Nadya-85/Grupo-3--FUNBIO/Documentación/Taller/Taller 10 - Actividad 3.pdf

Parámetro | Valor Bajo | Valor Medio | Valor Alto | Efecto principal
Altura de capa | 0.1mm | 0.15mm | 0.2mm | La calidad superficial y tiempo de impresión
Densidad de relleno | 10% | 20% | 50% | Densidad mecánica de la pieza y consumo de material
Velocidad de impresión | 30 mm/s | 50 mm/s | 70 mm/s | Tiempo total de impresión y precisión/adhesi ón
Top/Bottom Thickness | 0.6 mm | 0.9 mm | 1.5 mm | Dirección de la resistencia mecánica
Walls thickness | 0.8 mm | 1.2 mm | 1.7 mm | Resistencia estructural externa y acabado estético
Cooling | 40% | 90% | 100% | En PLA, más ventilación mejora los detalles y evita deformaciones.
Temperatura de impresión | 190 °C | 200 °C | 220 °C | Temperatura de la boquilla de impresión.
Peso | 15g | 18g | 20g
Tiempo | 5 h 33 min | 3 h 0 min | 1 h 52 min
