Nadya-85/Grupo-3--FUNBIO/Documentación/Entregables/Entrgable N°9/Entregable N°9.pdf

GUIA DE ENTREGABLE N°9

CASO 3:
Lesión medular por proyectil / paraplejia

INTEGRANTES:
Quezada Ponciano, Nadya Lyz Peñaloza Díaz, Matias Alejandro Silva Avileno, Fabiana Valery Palacin Hilario, Jeanpierre Ramirez Rodriguez, Alexandra Fajardo Peña, Edwin José Guillermo

ÍNDICE:
a) Hardware electrónico
b) Software
c) Fabricación digital
d) Plan de usabilidad basado en evidencias

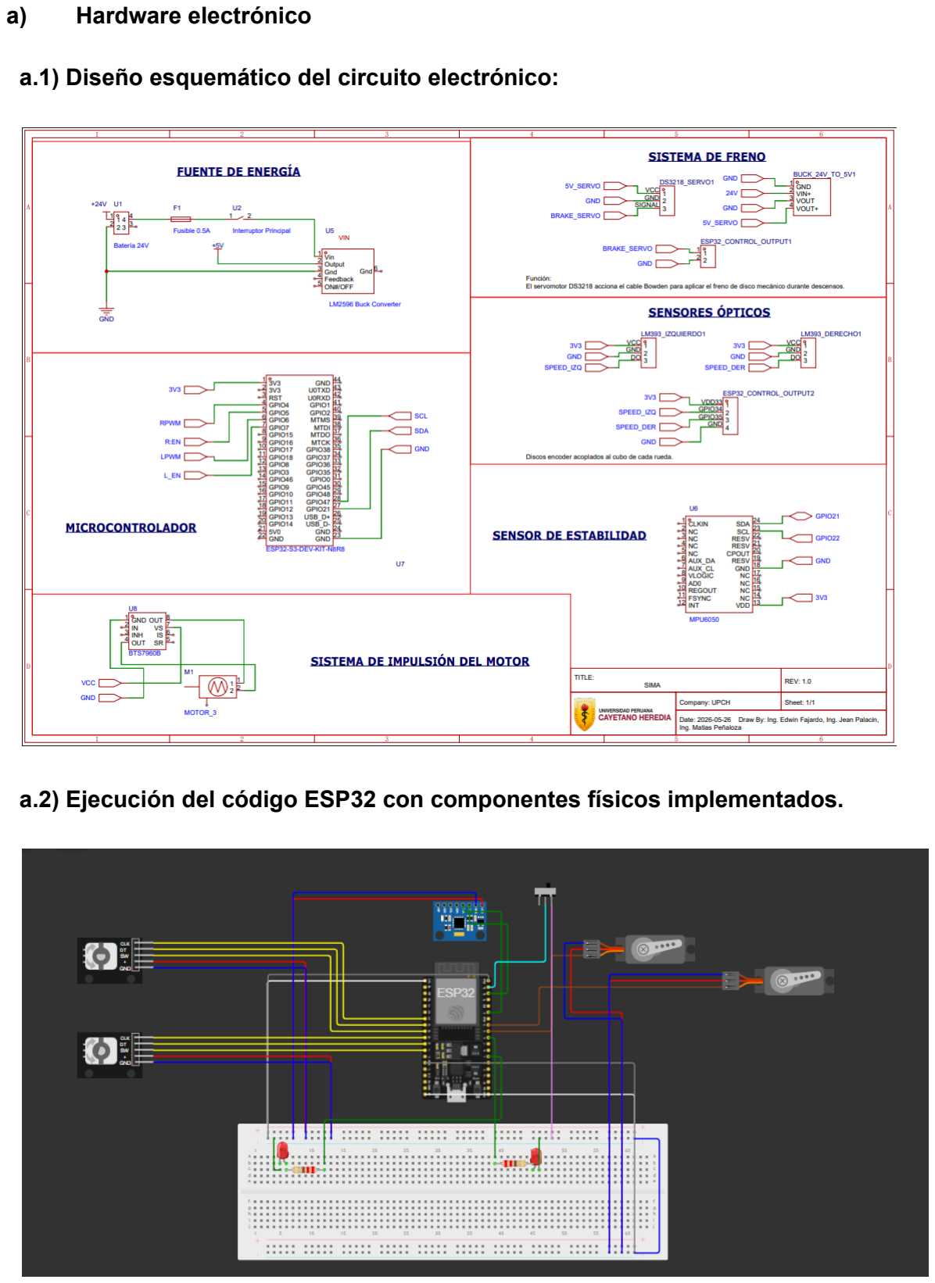
[picture p50: page 2]

a) Hardware electrónico

a.1) Diseño esquemático del circuito electrónico:

a.2) Ejecución del código ESP32 con componentes físicos implementados.

a.3) Avance de su prototipado electrónico.

Funcionamiento en casos:

- Caso 1: SISTEMA APAGADO

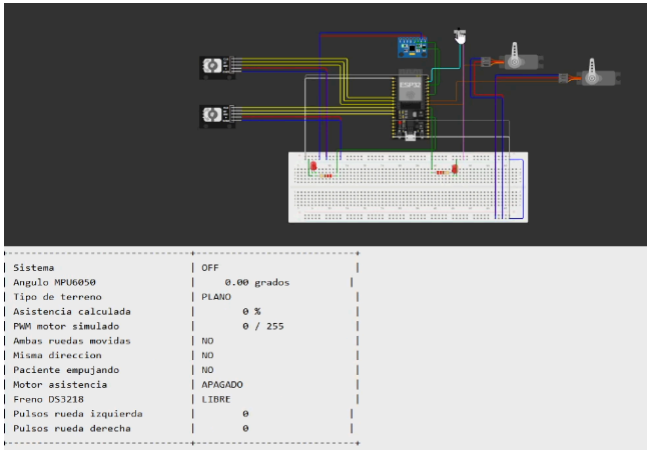
[picture p51: figure]

- Caso 2: MPU6050 detecta subida y el porcentaje de asistencia.

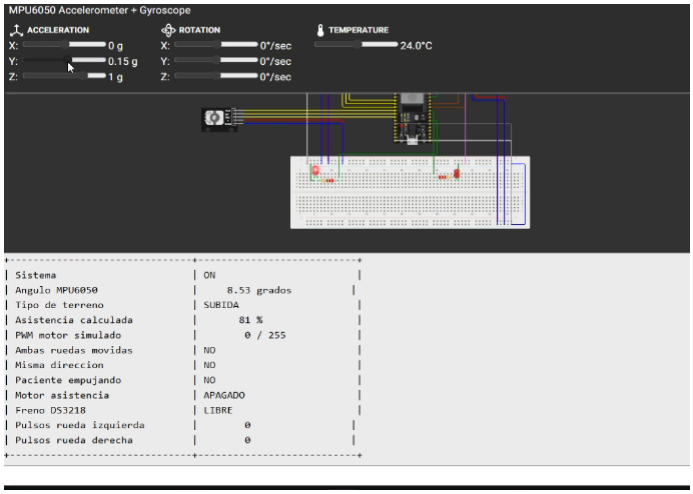
[picture p52: figure]

- Caso 3: MPU6050 detecta bajada e inhabilita la asistencia y activa los frenos intermitentemente.

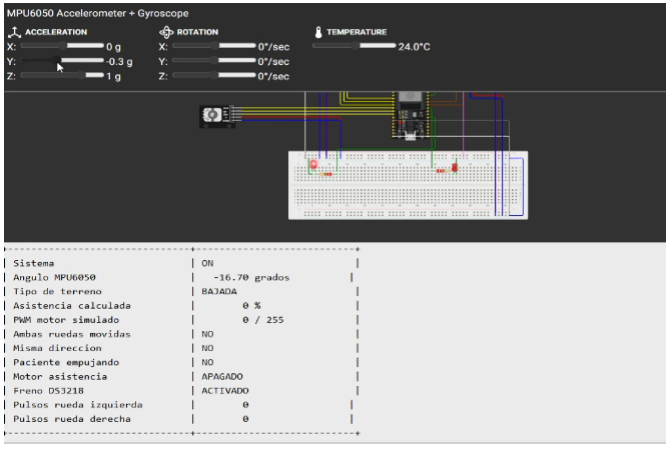
[picture p53: figure]

- Caso 4: Los sensores detectan el empuje y simultaneidad del movimiento de las ruedas y activa asistencia.

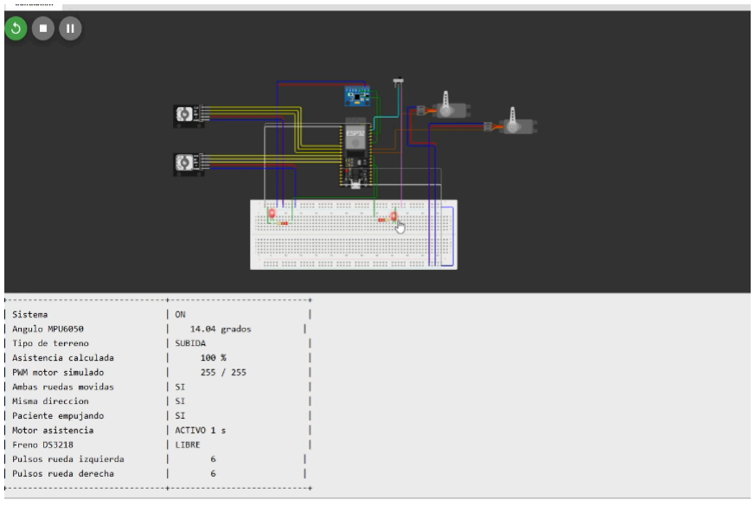
[picture p54: figure]

- Caso 5: Sensores detectan empuje y simultaneidad pero no activan la asistencia y bloquean el freno intermitentemente por bajada.

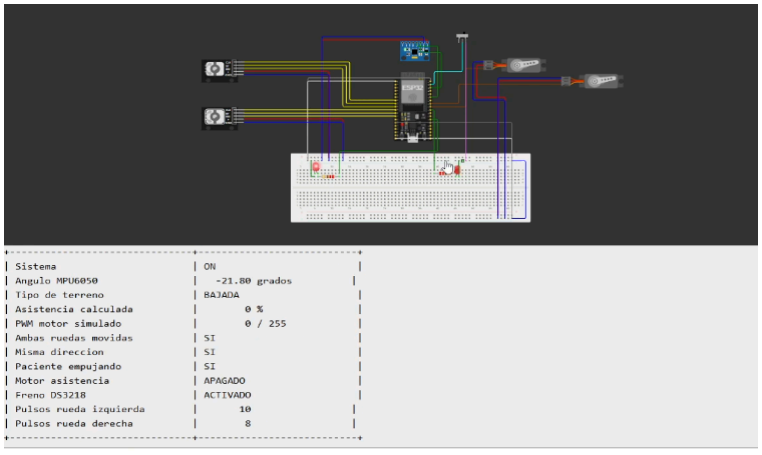
[picture p55: figure]

b) Software

b.1) Script de programación para el microcontrolador

Software.ino (https://drive.google.com/open?id=1QNNkiSALg92ZPX-Y5VDY9vaBm5gV7uGd)

c) Fabricación digital
c.1) Modelado digital del prototipo completo

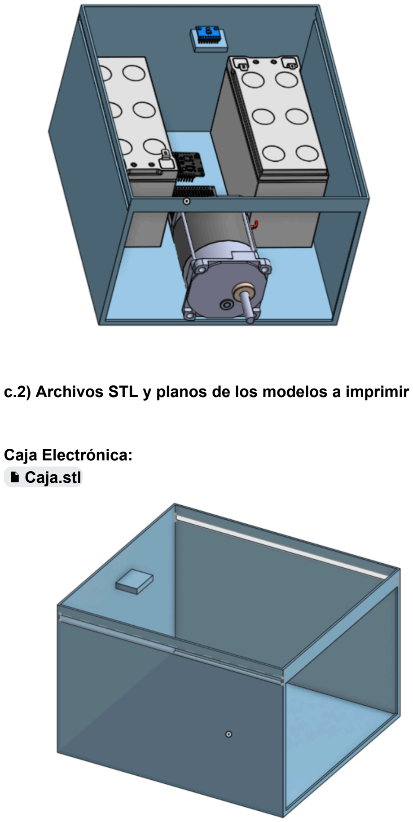
[picture p56: page 8]

c.2) Archivos STL y planos de los modelos a imprimir

Caja Electrónica:
Caja.stl (https://drive.google.com/open?id=1Idi60X_xnom6asZyzeSryu2H1RnrhICt)

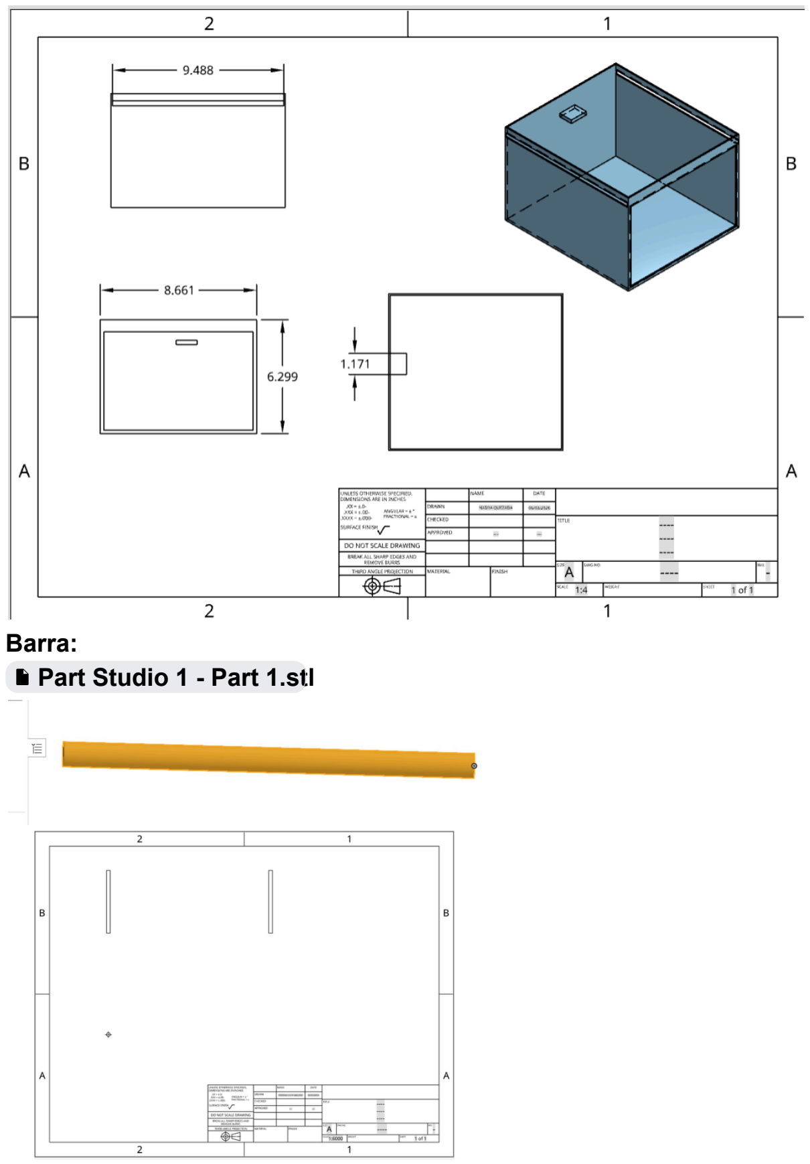
[picture p57: page 9]

Barra:
Part Studio 1 - Part 1.stl (https://drive.google.com/open?id=1k5roUTsqK_4T5D3ctGGkcU61z_Ii1c35)

Engranaje:
https://cad.onshape.com/documents/0c8cfb7354d4f6df7f082058/w/bfc970ec4490c92dce513070/e/b32831fdd1642657cbf62373 (https://cad.onshape.com/documents/0c8cfb7354d4f6df7f082058/w/bfc970ec4490c92dce513070/e/b32831fdd1642657cbf62373)

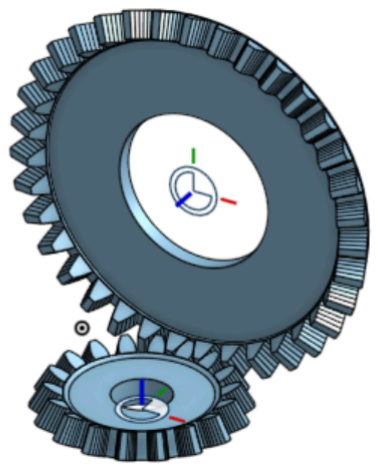
[picture p58: figure]
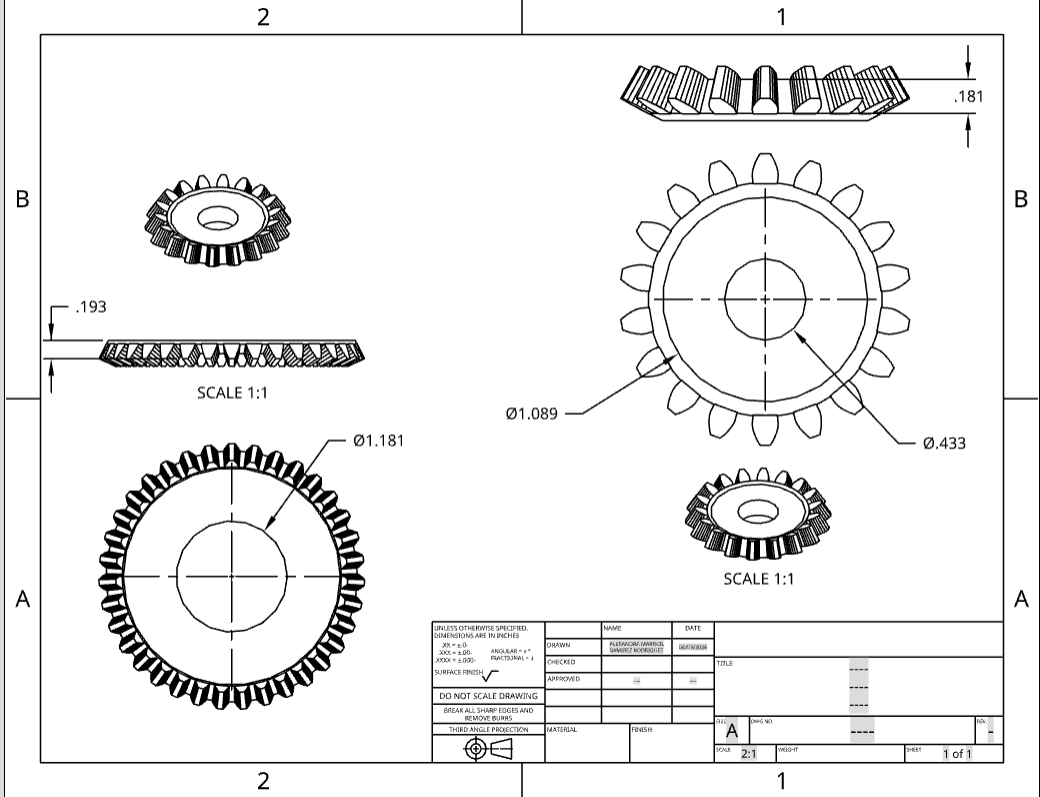
[picture p59: figure]

Archivos STL
https://github.com/Nadya-85/Grupo-3--FUNBIO/blob/5a6e28614ed48188a40b07a3fd94a64e7c92d70e/Documentaci%C3%B3n/Entregables/Entrgable%20N%C2%B09/Modelado%203D/engranaje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 (https://github.com/Nadya-85/Grupo-3--FUNBIO/blob/5a6e28614ed48188a40b07a3fd94a64e7c92d70e/Documentaci%C3%B3n/Entregables/Entrgable%20N%C2%B09/Modelado%203D/en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) https://github.com/Nadya-85/Grupo-3--FUNBIO/blob/5a6e28614ed48188a40b07a3fd94a64e7c92d70e/Documentaci%C3%B3n/Entregables/Entrgable%20N%C2%B09/Modelado%203D/engranaje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

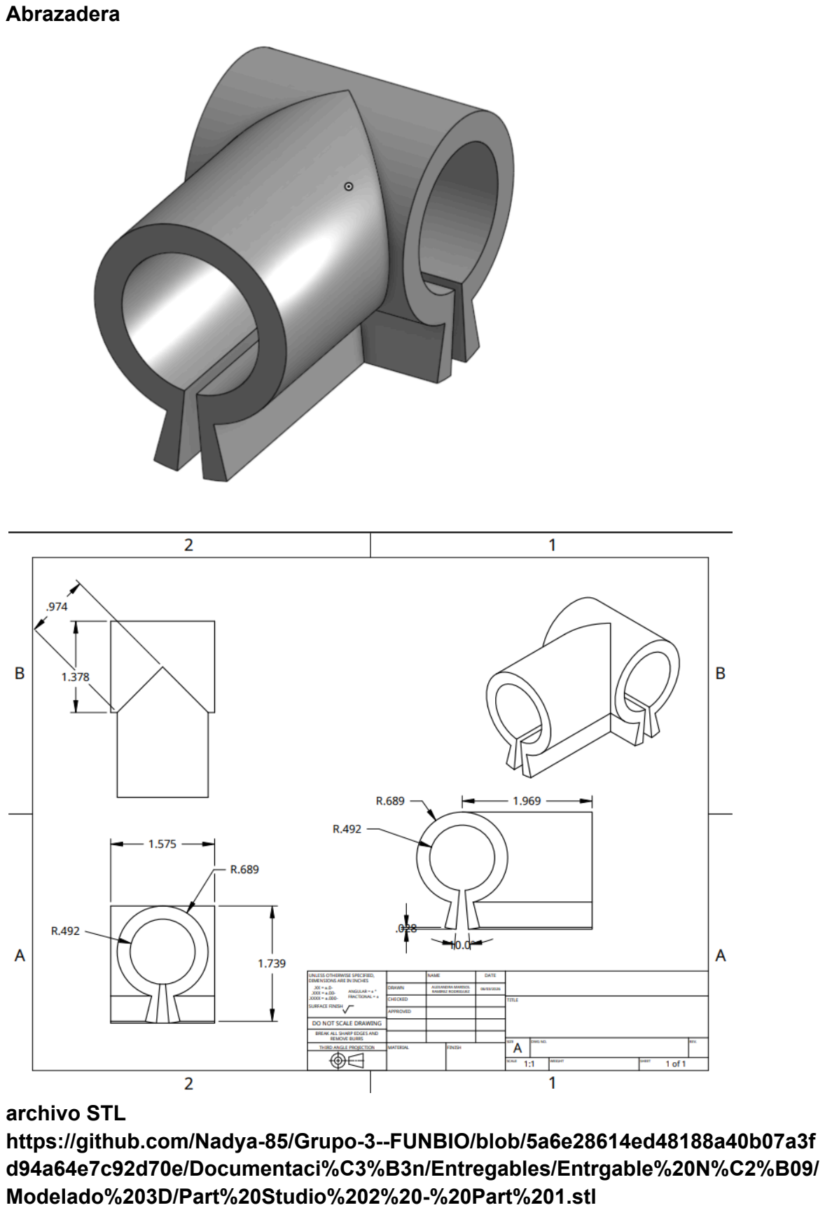
[picture p60: page 11]

Abrazadera

archivo STL
https://github.com/Nadya-85/Grupo-3--FUNBIO/blob/5a6e28614ed48188a40b07a3fd94a64e7c92d70e/Documentaci%C3%B3n/Entregables/Entrgable%20N%C2%B09/Modelado%203D/Part%20St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 d) Plan de usabilidad basado en evidencias
Sección de plan | ¿Qué es? | ¿Qué hacer ? | ¿Qué evidencias deben incluir ?
Contexto de uso | Sistema de asistencia y frenado inteligente para usuarios de silla de ruedas manual en entornos urbanos. | Identificar usuario, lugares de uso (rampas, veredas, hospitales) y frecuencia de uso. | Modelo 3D o boceto mostrando el Kit Urbano C7 instalado en la silla.
Perfil de usuario | Usuario de silla de ruedas con limitaciones motoras que afectan su movilidad e independencia. | Identificar limitaciones físicas relacionadas con movilidad y esfuerzo durante el desplazamiento. | Varón de 48 años destacando lesión medular, uso de silla de ruedas y dificultades de movilidad que justifican la implementación del Kit Urbano C7.
Analisis de tareas | Análisis de las acciones necesarias para instalar el Kit Urbano C7, activar la asistencia motorizada, desplazarse en pendientes y controlar la velocidad mediante el sistema de frenado. | Listar tareas como: instalar el kit, encender el sistema, desplazarse en terreno plano, subir pendientes con asistencia motorizada, bajar pendientes con frenado asistido y detener la silla. Identificar cuáles son críticas para la seguridad del usuario. | Tabla de tareas críticas, riesgos y consecuencias asociadas que se asocie a sus AVD (La tabla se mostrará en la siguiente figura) .
Criterios de exito | Definir valores aceptables para cada función del sistema, por ejemplo: precisión en la detección de pendientes, tiempo de respuesta, activación del frenado y nivel de seguridad durante el recorrido. | Definir objetivos de eficacia (activación correcta del sistema), eficiencia (tiempo de respuesta), satisfacción (comodidad y confianza del usuario) y seguridad (ausencia de incidentes). | Tabla con métricas cuantificables y resultados esperados. (La tabla se mostrará en la siguiente figura) .

Tabla de tareas críticas :

Tarea | Posible error | Riesgo | Criticidad
Instalar el kit | Mala fijación | Desprendimiento | Alta
Encender sistema | No verificar batería | Sistema inoperativo | Media
Subir pendiente | Asistencia insuficiente | Fatiga del usuario | Alta
Bajar pendiente | Fallo del frenado | Pérdida de control | Muy Alta

Tabla de métricas cuantificables y resultados esperados:

Indicador | Metodo de evaluacion | Valor objetivo
Detección de pendientes | Comparación con inclinación real | ≥ 95%
Activación de asistencia | Pruebas funcionales | ≥ 95%
Activación de frenado | Pruebas funcionales | ≥ 95%
Tiempo de respuesta | Cronómetro/registro del sistema | < 1 s
Satisfacción del usuario | Encuesta SUS | ≥ 80 puntos
Seguridad | Número de incidentes durante las pruebas | 0
