Nadya-85/Grupo-3--FUNBIO/Documentación/Entregables/Entregable N°8/Entregable N°8.pdf

GUIA DE ENTREGABLE N°8

CASO 3:
Lesión medular por proyectil / paraplejia

INTEGRANTES:
Quezada Ponciano, Nadya Lyz Peñaloza Díaz, Matias Alejandro Silva Avileno, Fabiana Valery Palacin Hilario, Jeanpierre Ramirez Rodriguez, Alexandra Fajardo Peña, Edwin José Guillermo

ÍNDICE
1. Importados
2. Modelados

Modelado 3D de los componentes

### 1. Importados

a) ESP32

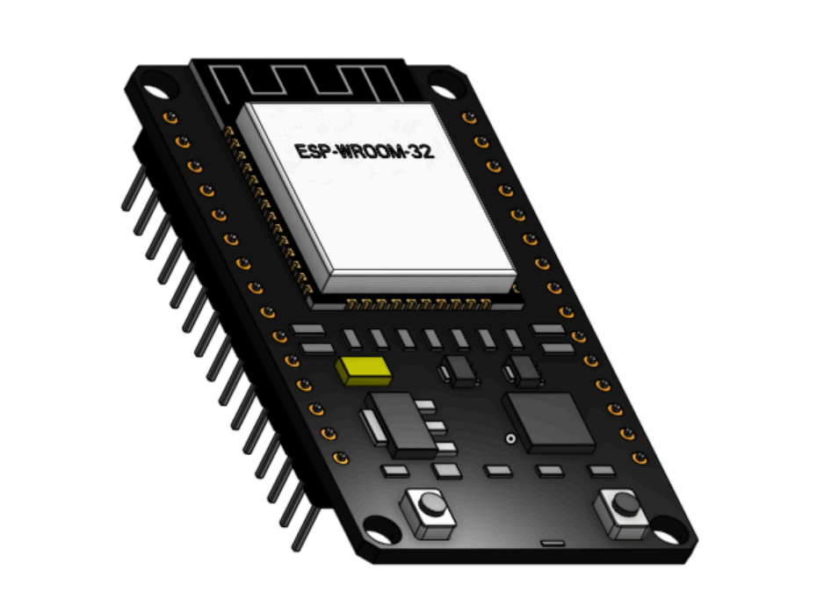
[picture p61: figure]

https://cad.onshape.com/documents/fe2fc5c113415b535518b715/w/49ef476d0d1d86e92a8f14a1/e/2e020fae72789caa4f564eb7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 23676df5edec03a35 (https://cad.onshape.com/documents/fe2fc5c113415b535518b715/w/49ef476d0d1d86e92a8f14a1/e/2e020fae72789caa4f564eb7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)

b) Motor DC 24V

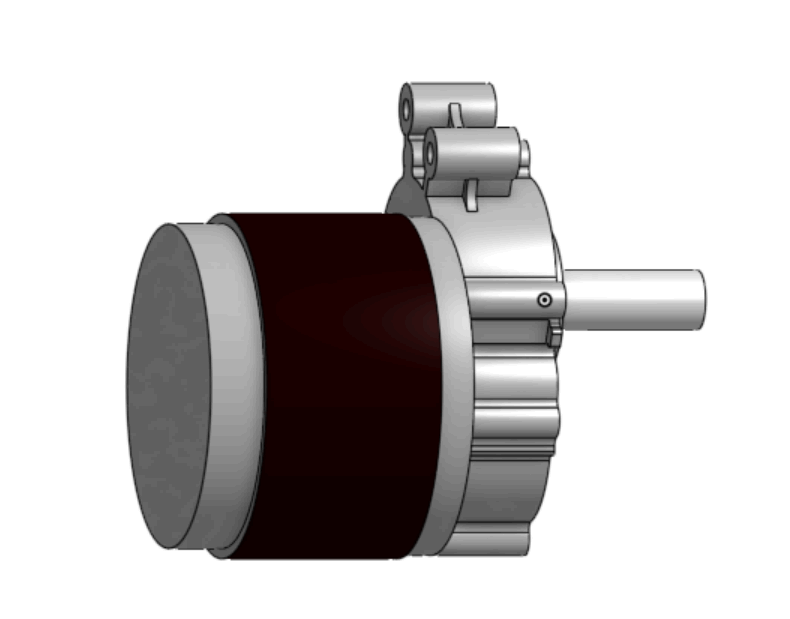
[picture p62: figure]

https://cad.onshape.com/documents/29574c1c496ad6fbb76fa65f/w/c6939c078cb6e51be4b720a7/e/403110079cfe1cae44fe99f7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 e4df02ca1f19e2636 (https://cad.onshape.com/documents/29574c1c496ad6fbb76fa65f/w/c6939c078cb6e51be4b720a7/e/403110079cfe1cae44fe99f7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)

c) Driver de motor (BTS7960 43A)

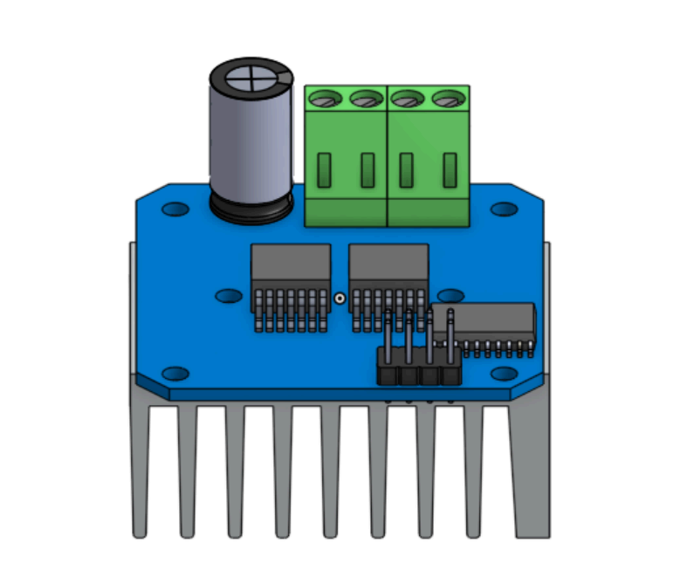
[picture p63: figure]

https://cad.onshape.com/documents/722dbbecc4ac26e69685e04b/w/de750ad9b3bf6ea111d73016/e/7e61f720ef6a980854f621ba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 9e605cd60c42166c (https://cad.onshape.com/documents/722dbbecc4ac26e69685e04b/w/de750ad9b3bf6ea111d73016/e/7e61f720ef6a980854f621ba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)

d) Regulador LM2596

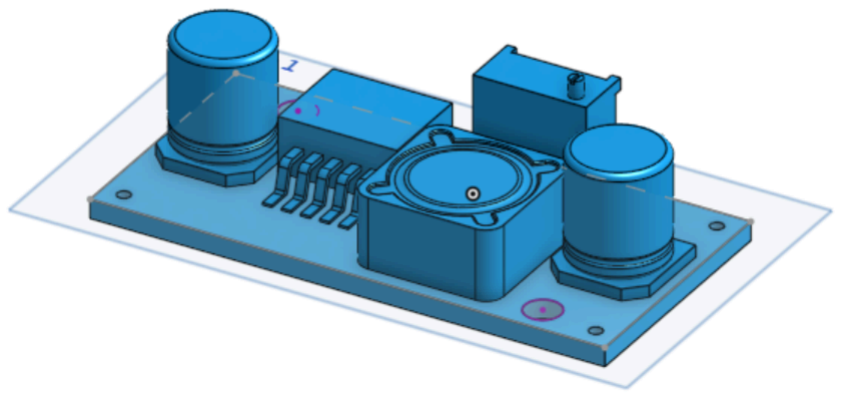
[picture p64: figure]

https://cad.onshape.com/documents/b7b84f8724b1efabd3e8bedd/w/a21f4455c5390d7d0d2bf8c8/e/14543a8e8df9499e86e28706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 45721502616d5c2a6 (https://cad.onshape.com/documents/b7b84f8724b1efabd3e8bedd/w/a21f4455c5390d7d0d2bf8c8/e/14543a8e8df9499e86e28706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)

e) Switch ON/OFF

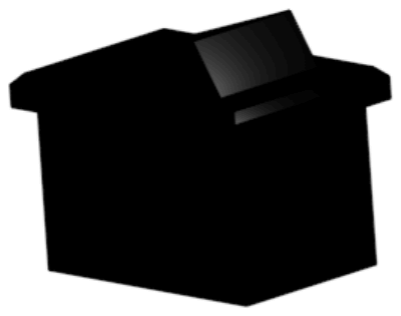
[picture p65: figure]

https://cad.onshape.com/documents/ade0a61845ae4fb3431f720c/w/565239054fb8be03dde38aee/e/1b88e0a8e63dd7065da3dd35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 3f5721502616d5c101 (https://cad.onshape.com/documents/ade0a61845ae4fb3431f720c/w/565239054fb8be03dde38aee/e/1b88e0a8e63dd7065da3dd35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)

f) LM393

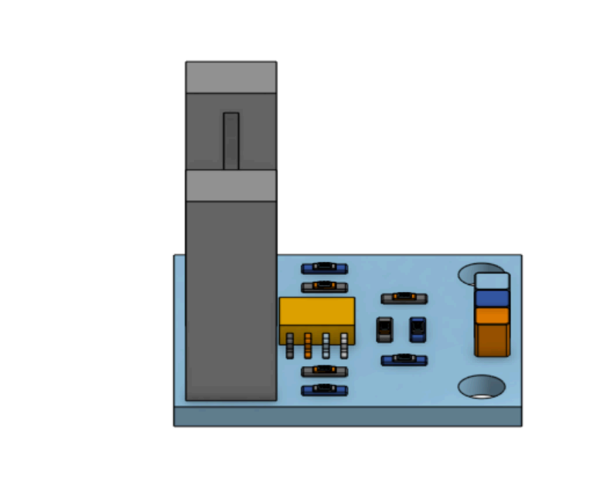
[picture p66: figure]

https://cad.onshape.com/documents/a74c2326ba62b3aa8945d9c9/w/44dd0150f07406c4244389be/e/a022ccecb725c4a6901df66b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 7b468401201dcc69f (https://cad.onshape.com/documents/a74c2326ba62b3aa8945d9c9/w/44dd0150f07406c4244389be/e/a022ccecb725c4a6901df66b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)

g) MPU 6050

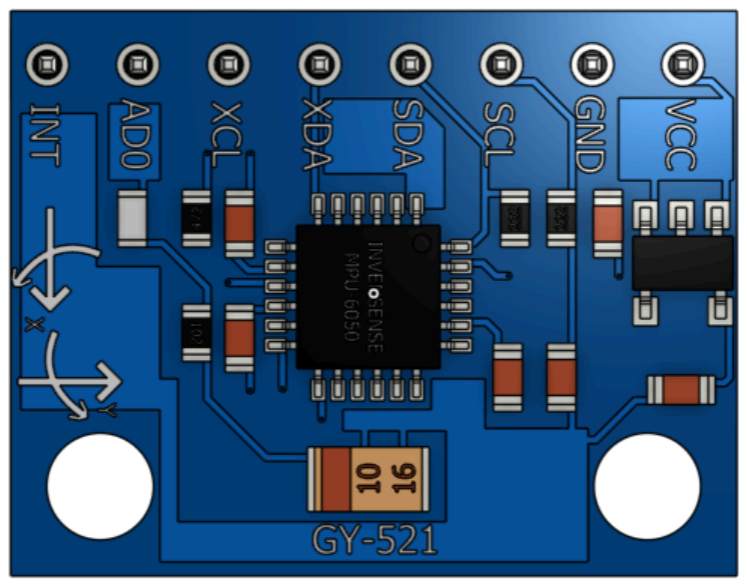
[picture p67: figure]

https://cad.onshape.com/documents/0f27ed9f233e3be8bb802911/w/502657e910908bda854d1360/e/78c170c33b39e40b5ba9a4cb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 c3bcc75bd5e84913b4 (https://cad.onshape.com/documents/0f27ed9f233e3be8bb802911/w/502657e910908bda854d1360/e/78c170c33b39e40b5ba9a4cb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)

h) Servo DS3218

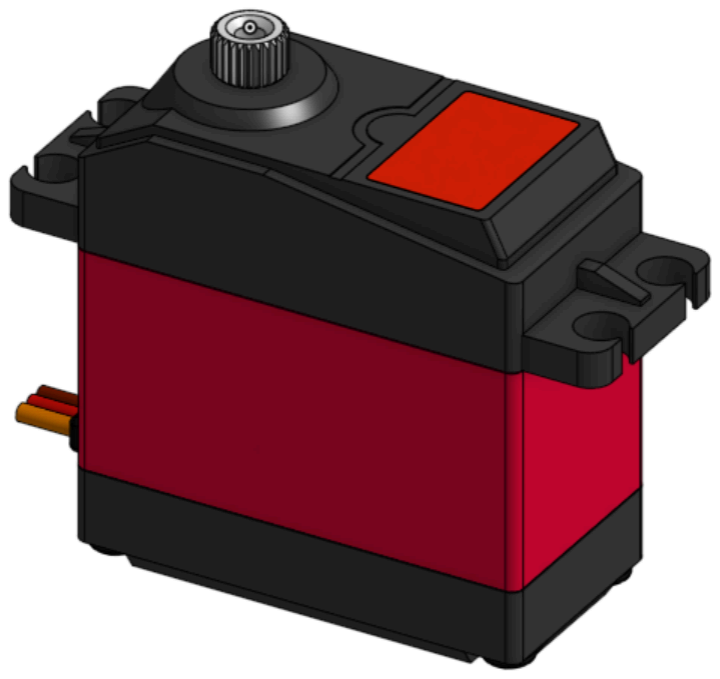
[picture p68: figure]

https://cad.onshape.com/documents/d5c7789b7a614957c1189cbd/w/ce6124b3abbf0c9b08c676d4/e/8ea79ae3aaf09e6f7db1e214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 0f739b181326bd891 (https://cad.onshape.com/documents/d5c7789b7a614957c1189cbd/w/ce6124b3abbf0c9b08c676d4/e/8ea79ae3aaf09e6f7db1e214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)
i) Buck 5V

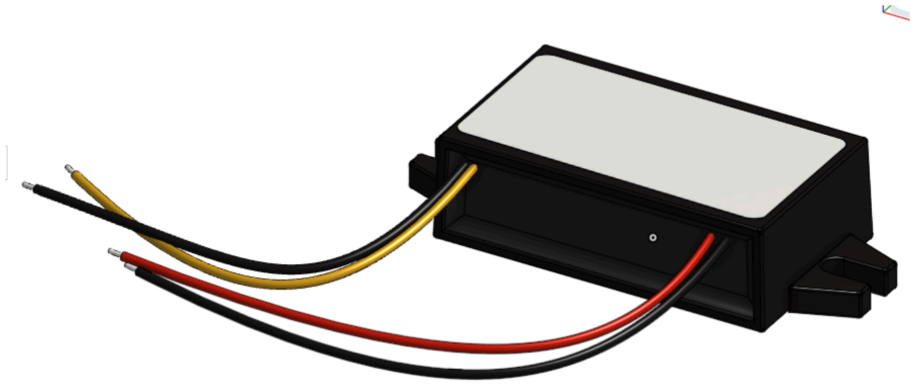
[picture p69: figure]

https://cad.onshape.com/documents/6bf642ec03a6724235cac885/w/3cc0e38e2b2c3b097d9072ba/e/ca223f1ae1df0242dc7e0e98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 73db0dc0b4097176f (https://cad.onshape.com/documents/6bf642ec03a6724235cac885/w/3cc0e38e2b2c3b097d9072ba/e/ca223f1ae1df0242dc7e0e98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)

### 2. Modelados (colocar la imagen y el link del componente)

a) Caja para la electrónica - Versión 1

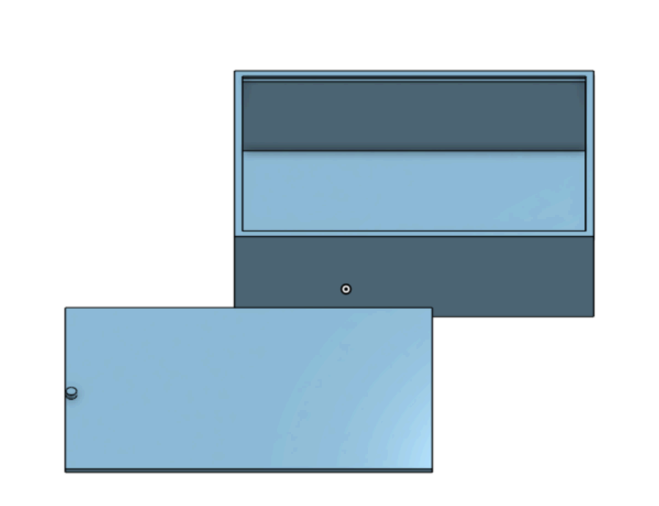
[picture p70: figure]

https://cad.onshape.com/documents/ded1ce054706ec6fbc7535f1/w/0c0e8277efb87ba04d14f22f/e/1e055f56dfcda0f58cce56e2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 57 (https://cad.onshape.com/documents/ded1ce054706ec6fbc7535f1/w/0c0e8277efb87ba04d14f22f/e/1e055f56dfcda0f58cce56e2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)
