Nadya-85/Grupo-3--FUNBIO/Documentación/Entregables/Presentaciones/PPT Entregable N°8.pdf

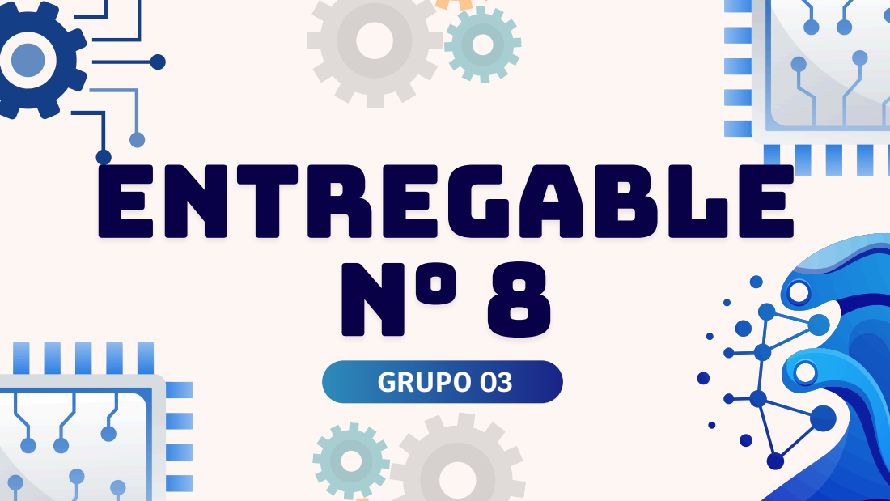
[picture p71: page 1]
GRUPO 03; ENTREGABLE N° 8

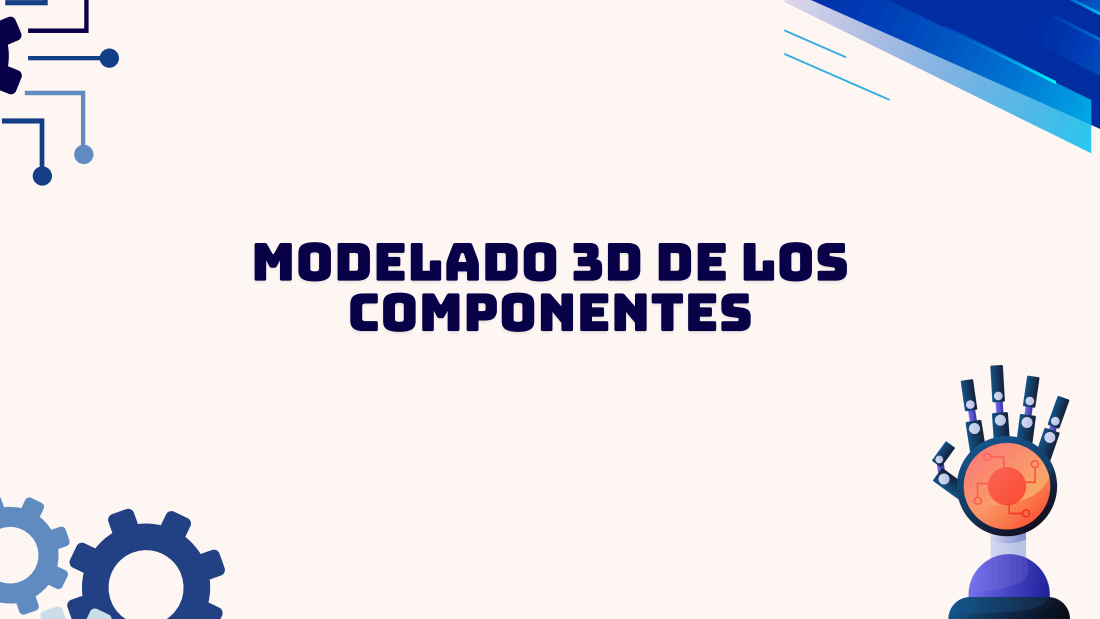
[picture p72: page 2]

Modelado 3D de los
componentes

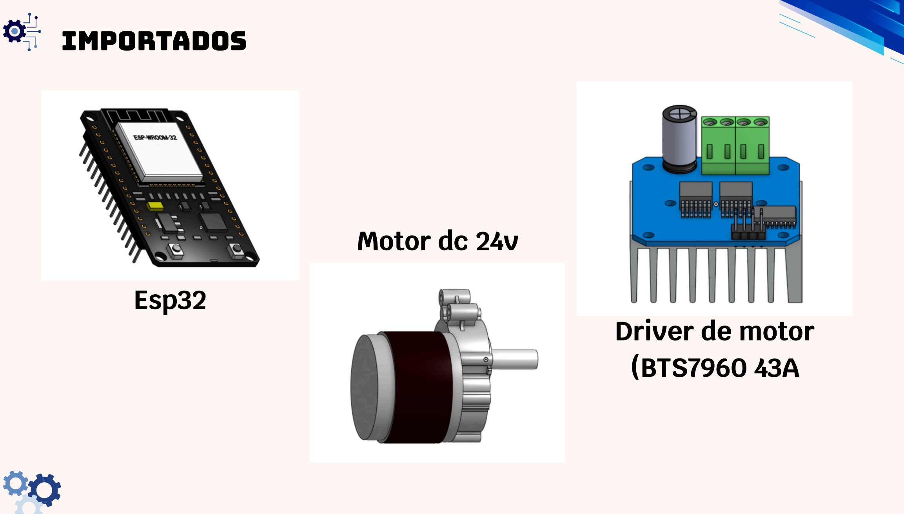
[picture p73: page 3]

Importados

Esp32

Motor dc 24v

Driver de motor
(BTS7960 43A

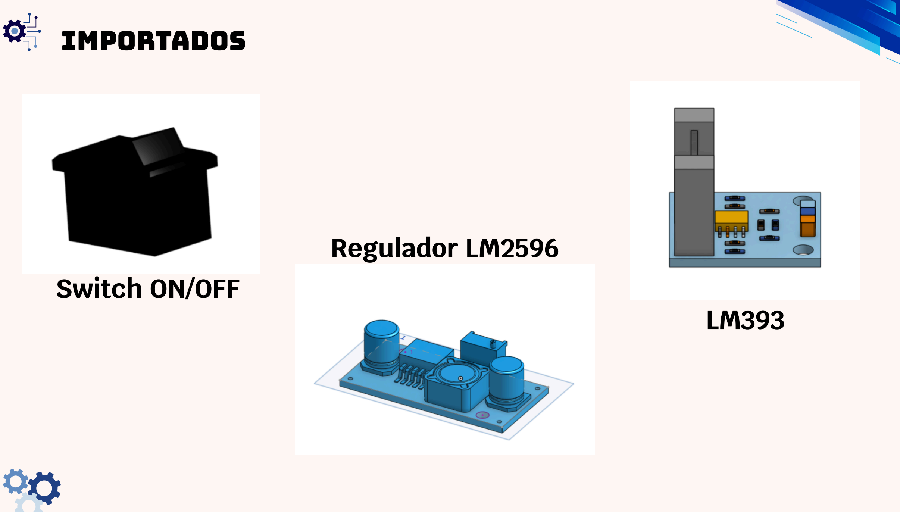
[picture p74: page 4]

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
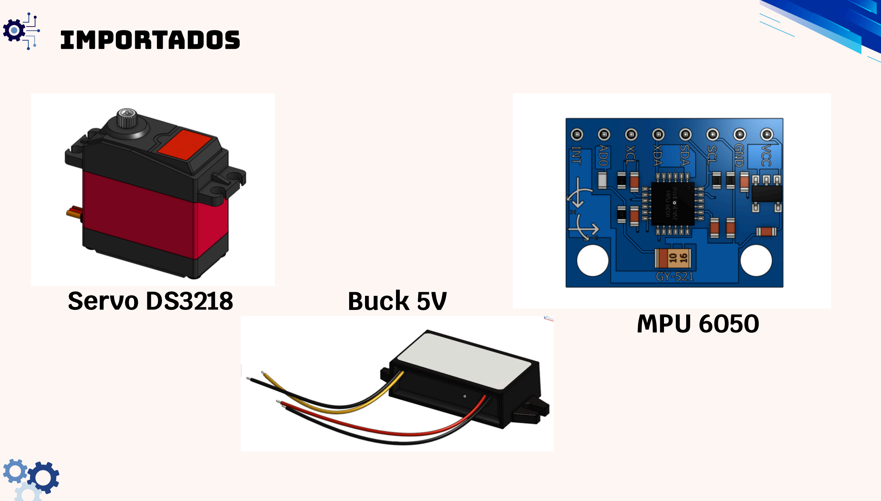
[picture p75: page 5]

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
Modelados


Caja para la
electrónica

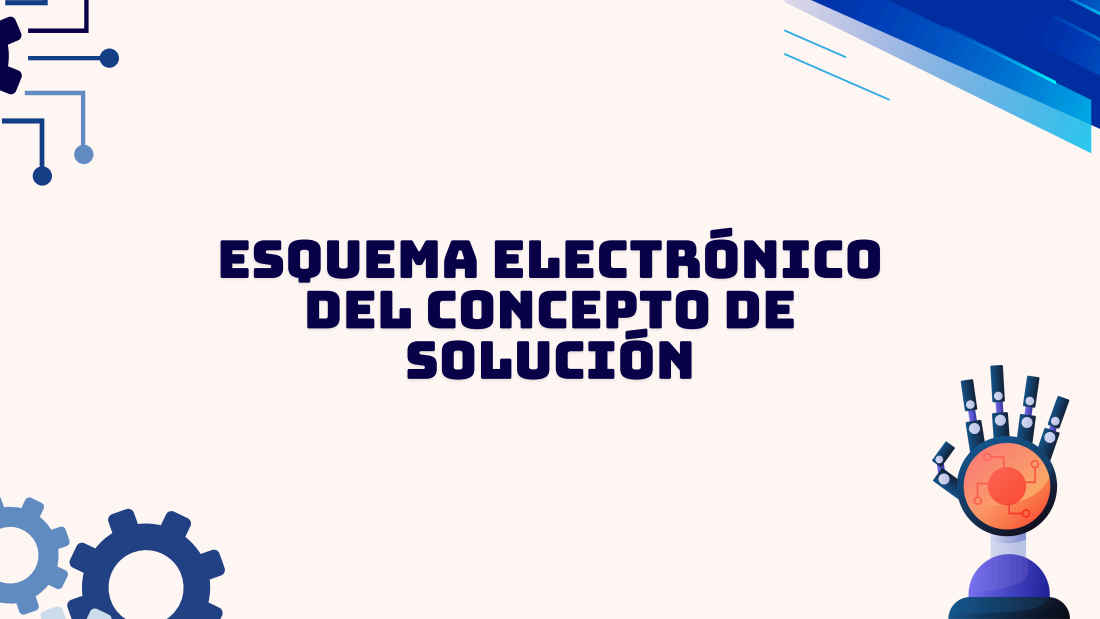
[picture p76: page 7]

Esquema Electrónico
del concepto de
solución

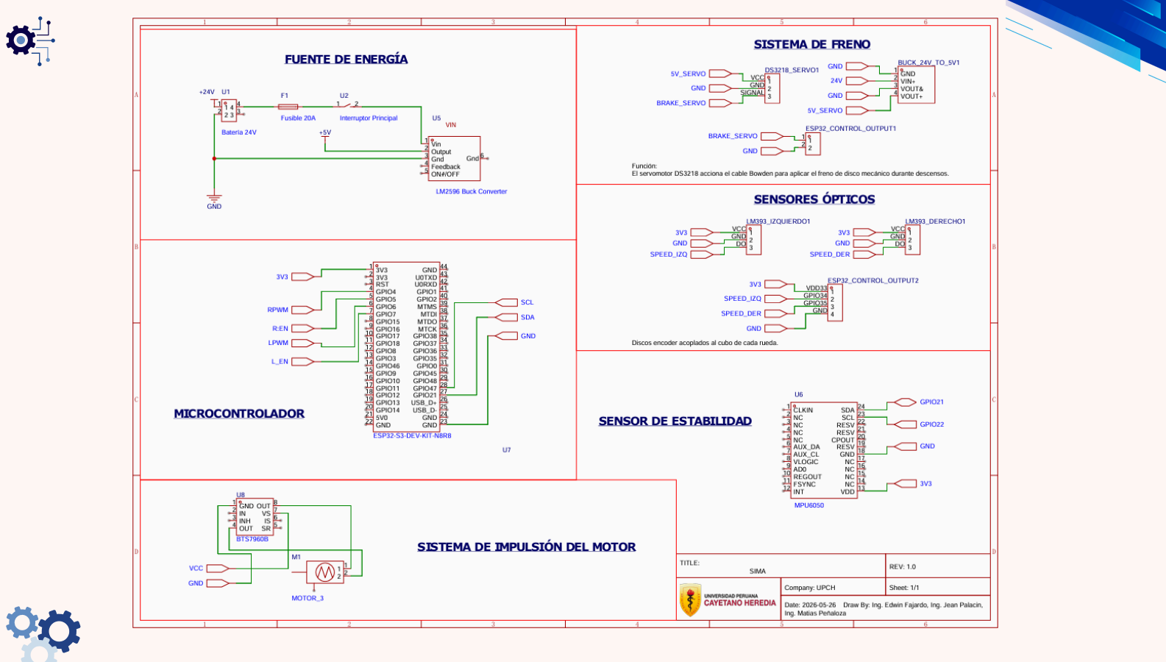
[picture p77: page 8]
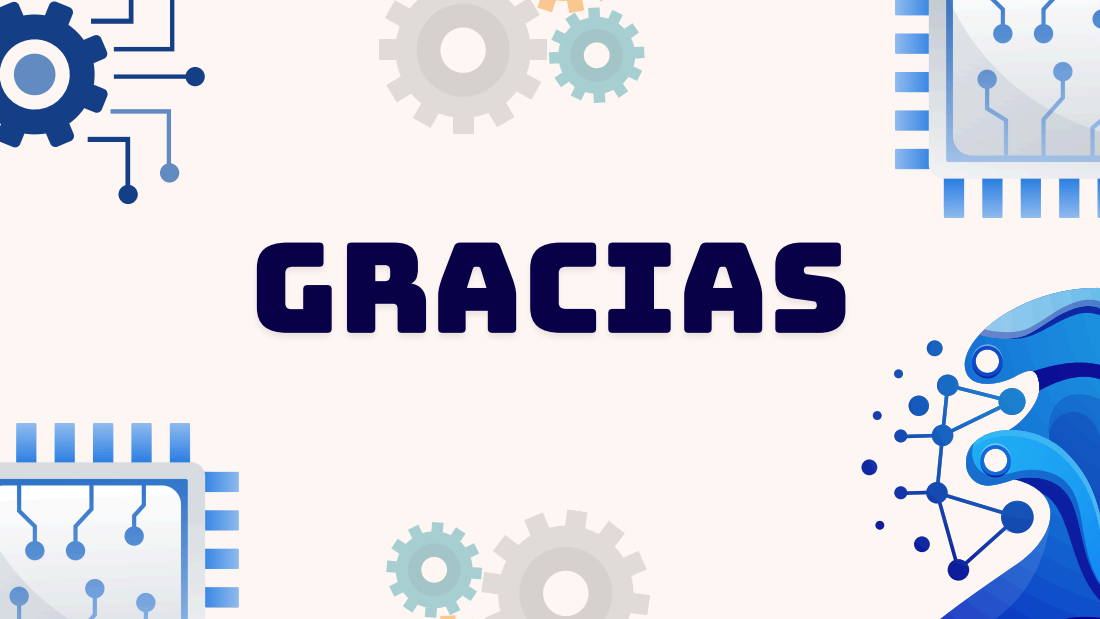
[picture p78: page 9]
GRACIAS
