Nadya-85/Grupo-3--FUNBIO/Documentación/Taller/Taller de Modelado 3D/Palacin Hilario, Jean/jeanpierre-palacin-hilario-b887ae31-cbae-40d7-aa20-296a3640dcb6-certificate.pdf

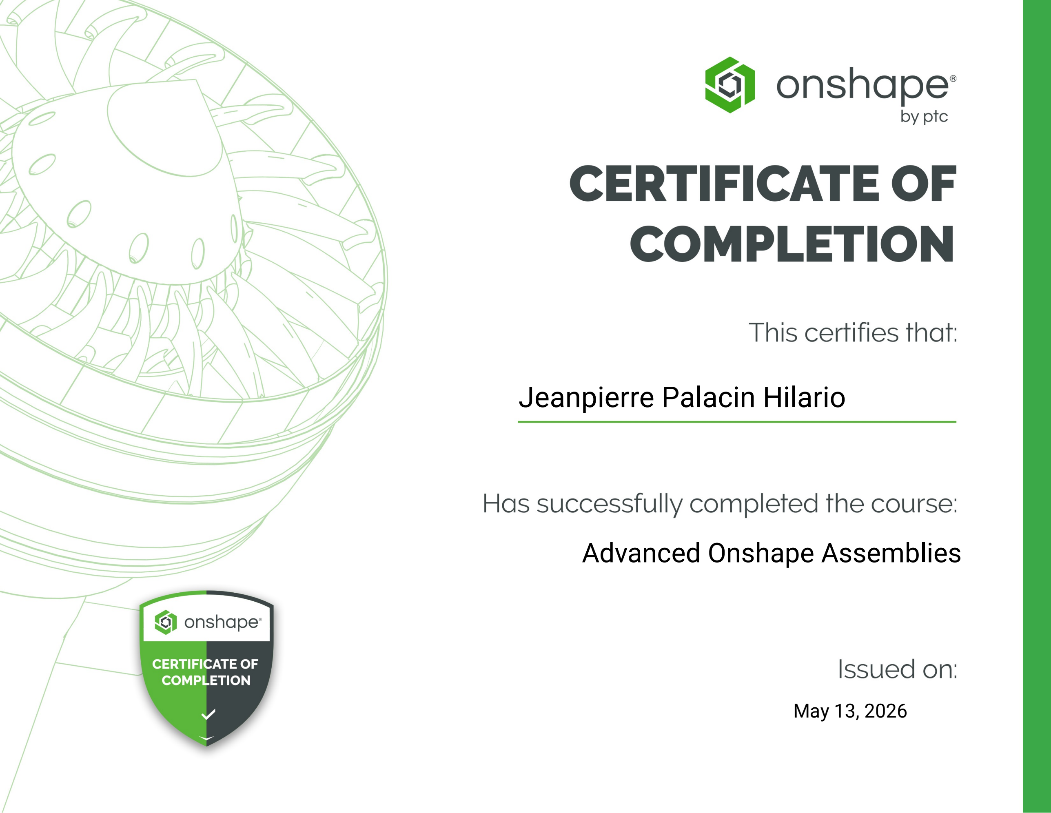
[picture p79: page 1]

Jeanpierre Palacin Hilario

Advanced Onshape Assemblies

May 13, 2026
