Nadya-85/Grupo-3--FUNBIO/Documentación/Taller/Taller de Modelado 3D/Silva Avileno, Fabiana/fabiana-silva-avileno-cdda89d0-f8d7-4462-bd3a-523eefe1cc21-certificate.pdf

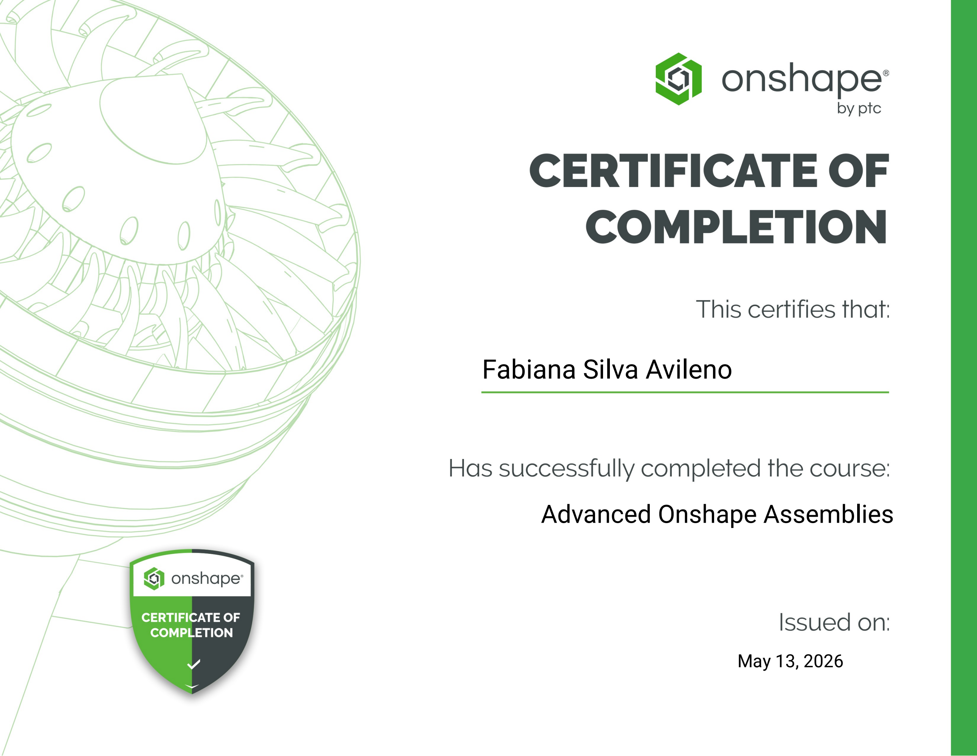
[picture p80: page 1]

Fabiana Silva Avileno

Advanced Onshape Assemblies

May 13, 2026
