Nadya-85/Grupo-3--FUNBIO/Documentación/Taller/Taller de Modelado 3D/Fajardo Peña, Edwin/Taller de Elementos Mecánicos.pdf

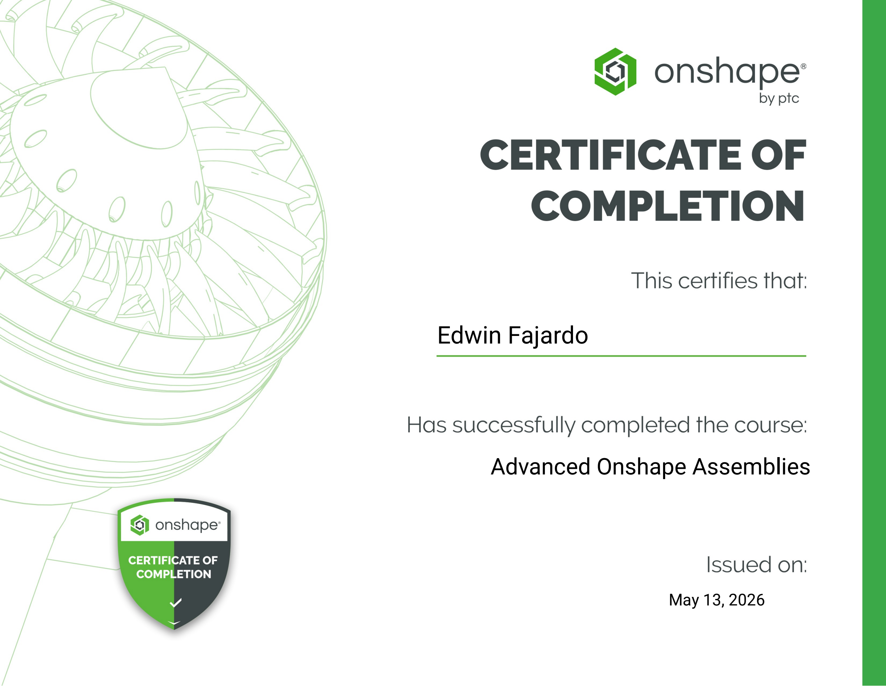
[picture p81: page 1]

Edwin Fajardo

Advanced Onshape Assemblies

May 13, 2026
