Nadya-85/Grupo-3--FUNBIO/Documentación/Taller/Taller de Modelado 3D/Silva Avileno, Fabiana/fabiana-silva-avileno-certificate.pdf

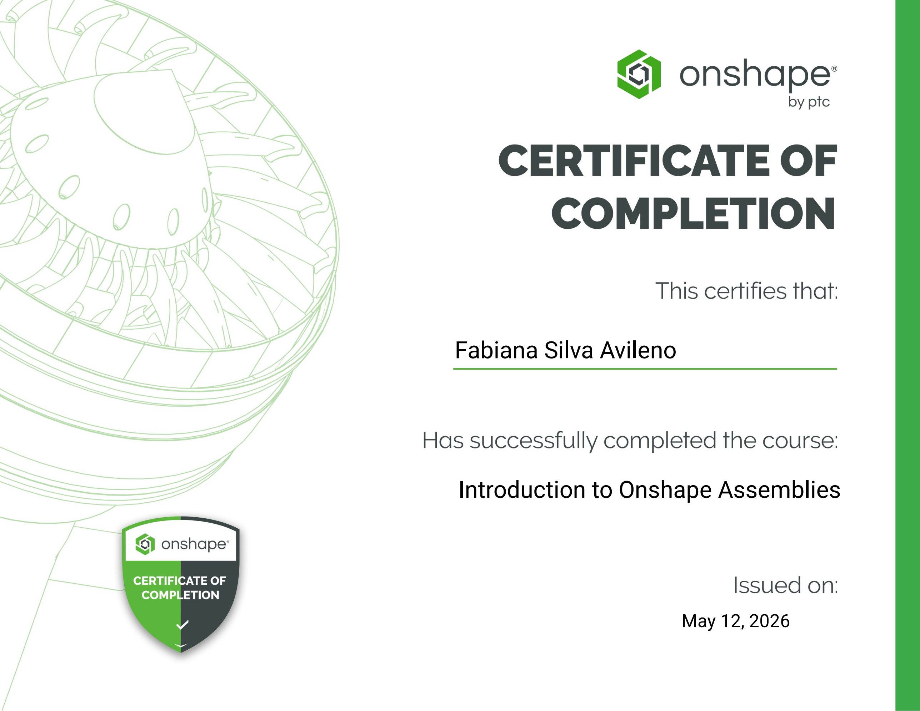
[picture p82: page 1]

Fabiana Silva Avileno

May 12, 2026

Introduction to Onshape Assemblies
