Nadya-85/Grupo-3--FUNBIO/Documentación/Taller/Taller de Modelado 3D/Palacin Hilario, Jean/jeanpierre-palacin-hilario-5044f47b-e34a-427e-8ce7-2f9dff3e71ce-certificate.pdf

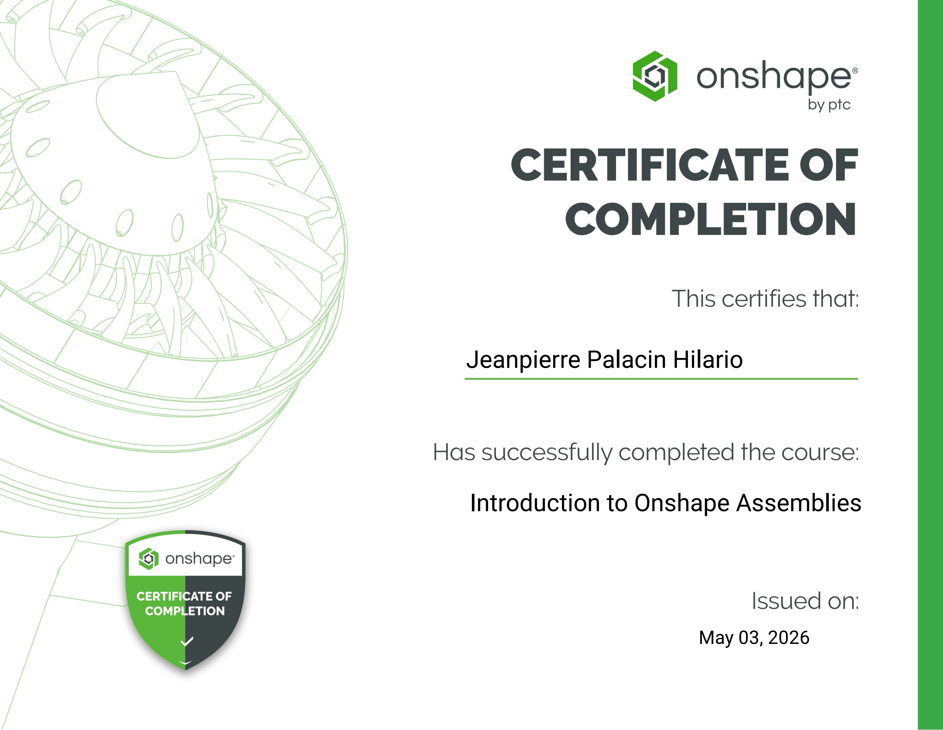
[picture p83: page 1]

Jeanpierre Palacin Hilario

May 03, 2026

Introduction to Onshape Assemblies
