Nadya-85/Grupo-3--FUNBIO/Documentación/Taller/Taller de Modelado 3D/Palacin Hilario, Jean/jeanpierre-palacin-hilario-8060c102-7970-424b-bebe-bbf9b13b87c1-certificate.pdf

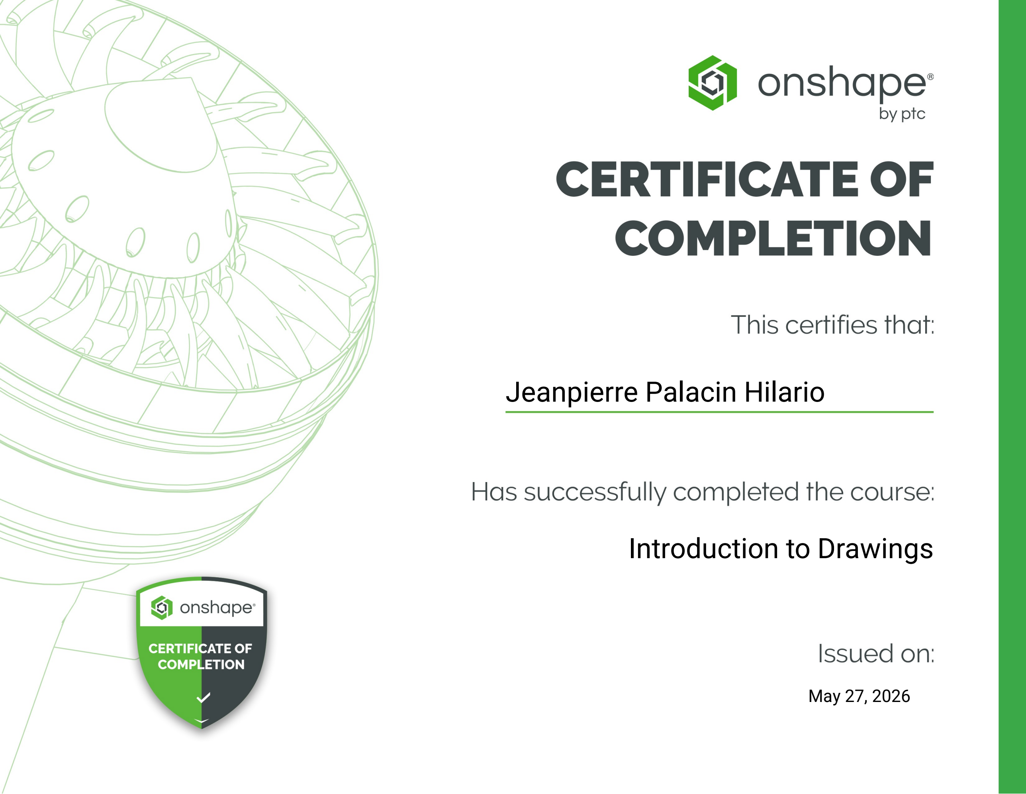
[picture p90: page 1]

Jeanpierre Palacin Hilario

May 27, 2026

Introduction to Drawings
