Nadya-85/Grupo-3--FUNBIO/Documentación/Taller/Taller de Modelado 3D/Fajardo Peña, Edwin/Introducción al dibujo.pdf

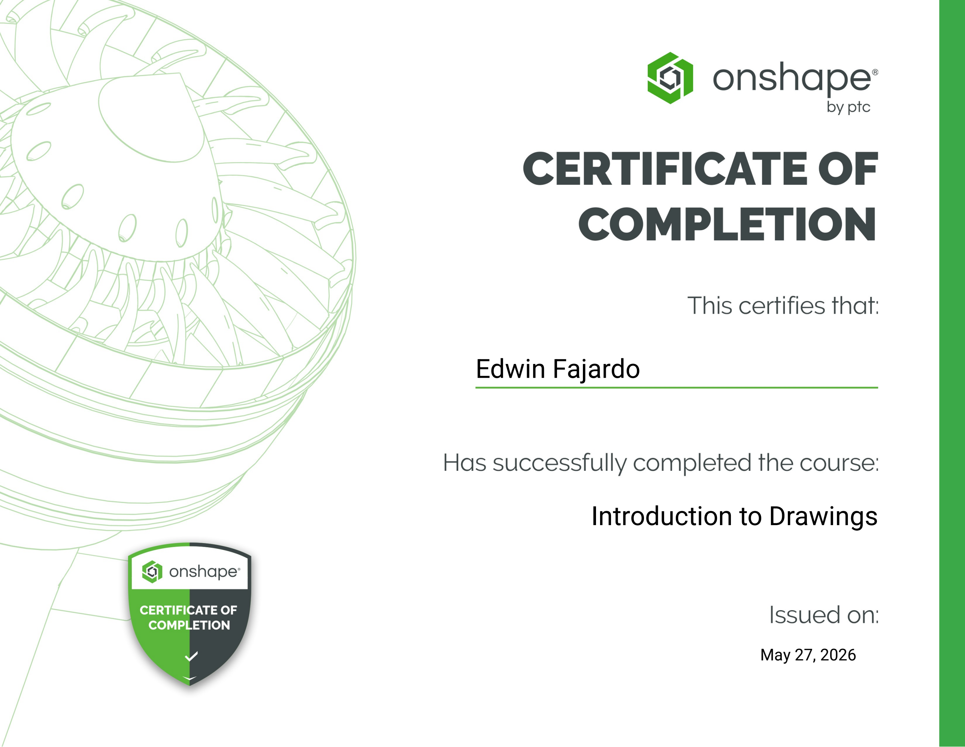
[picture p91: page 1]

Edwin Fajardo

May 27, 2026

Introduction to Drawings
