Nadya-85/Grupo-3--FUNBIO/Documentación/Taller/Taller de Modelado 3D/Ramirez Rodrigruez, Alexandra/alexandra-marisol-ramirez-rodriguez-234f79e6-4456-4ad6-a180-819df46c84fc-certificate.pdf

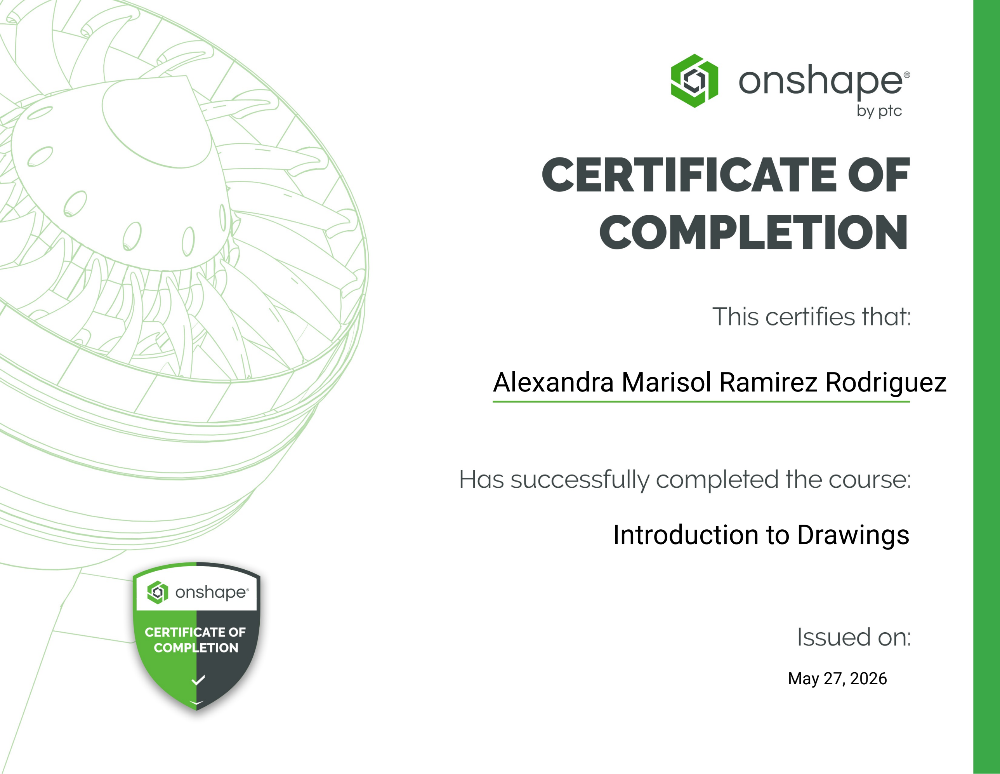
[picture p92: page 1]

Alexandra Marisol Ramirez Rodriguez

May 27, 2026

Introduction to Drawings
