Nadya-85/Grupo-3--FUNBIO/Documentación/Taller/Taller de Modelado 3D/Silva Avileno, Fabiana/fabiana-silva-avileno-78b4e4ff-3e47-40f5-b854-3cc98decb57e-certificate.pdf

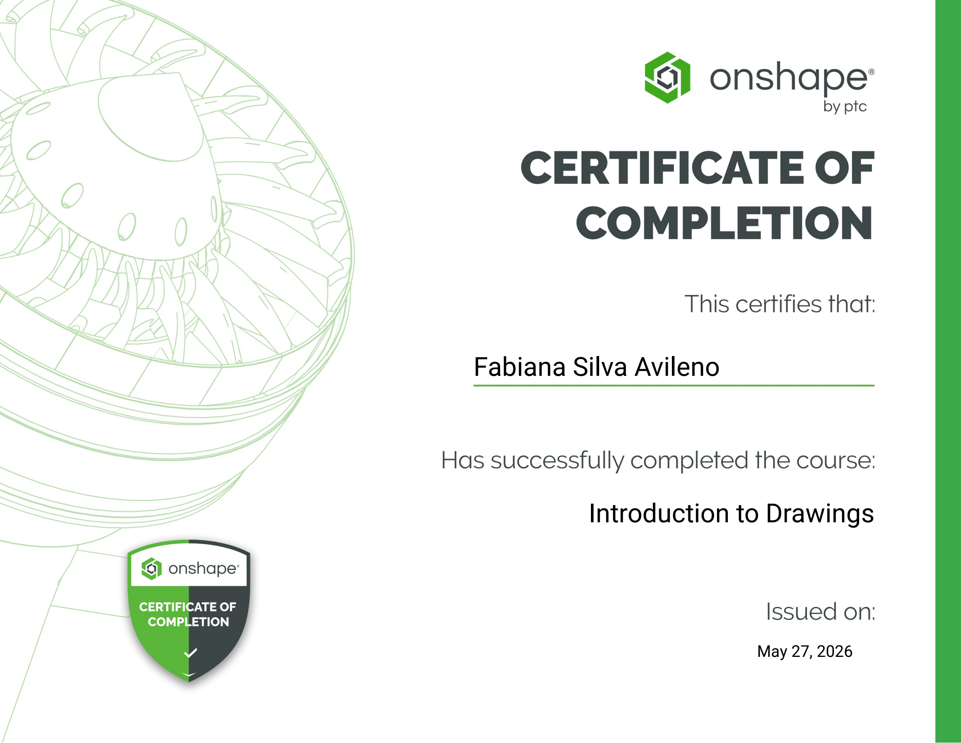
[picture p93: page 1]

Fabiana Silva Avileno

May 27, 2026

Introduction to Drawings
