Nadya-85/Grupo-3--FUNBIO/Documentación/Taller/Taller de Modelado 3D/Peñaloza Días, Matías/INTRODUCTION TO DRAWINGS CERTIFICATE.pdf

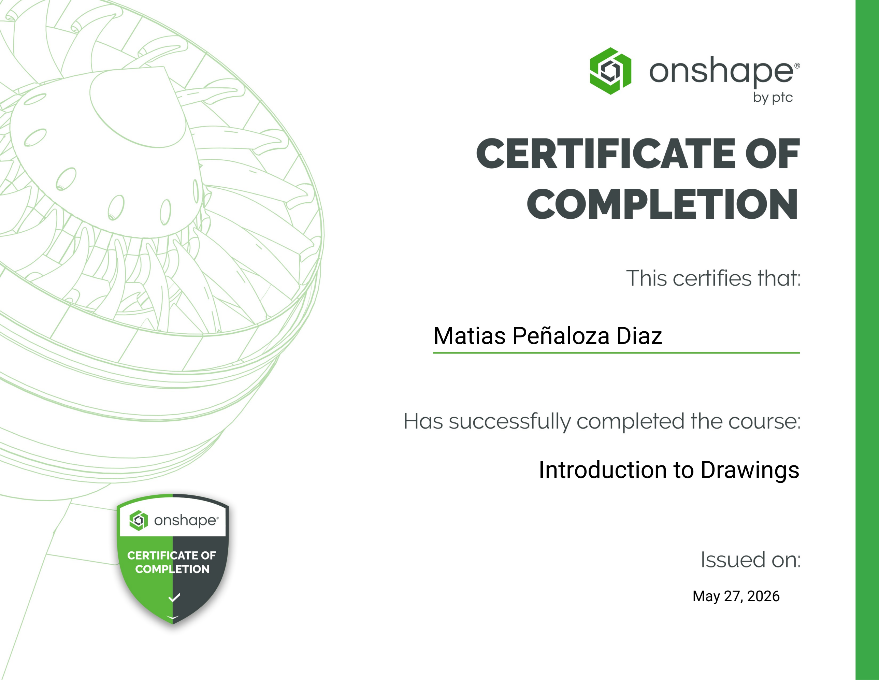
[picture p94: page 1]

Matias Peñaloza Diaz

May 27, 2026

Introduction to Drawings
