Nadya-85/Grupo-3--FUNBIO/Documentación/Taller/Taller de Modelado 3D/Quezada Ponciano, Nadya/Certificado Introduction to Drawings.pdf

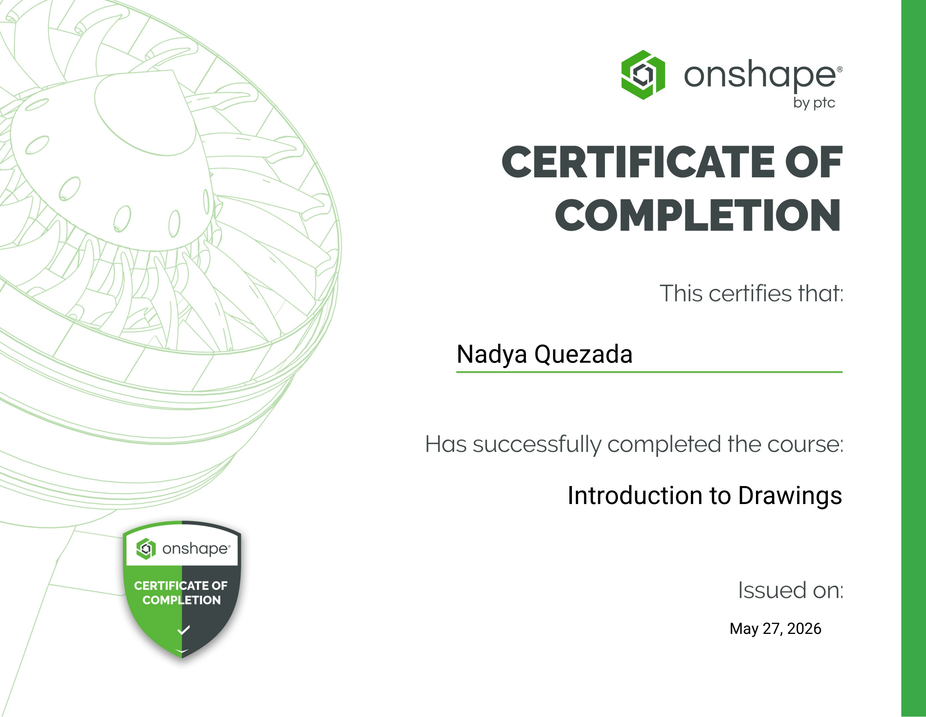
[picture p95: page 1]

Nadya Quezada

May 27, 2026

Introduction to Drawings
