Nadya-85/Grupo-3--FUNBIO/Documentación/Taller/Taller de Modelado 3D/Peñaloza Días, Matías/Certificate Detailed Drawings.pdf

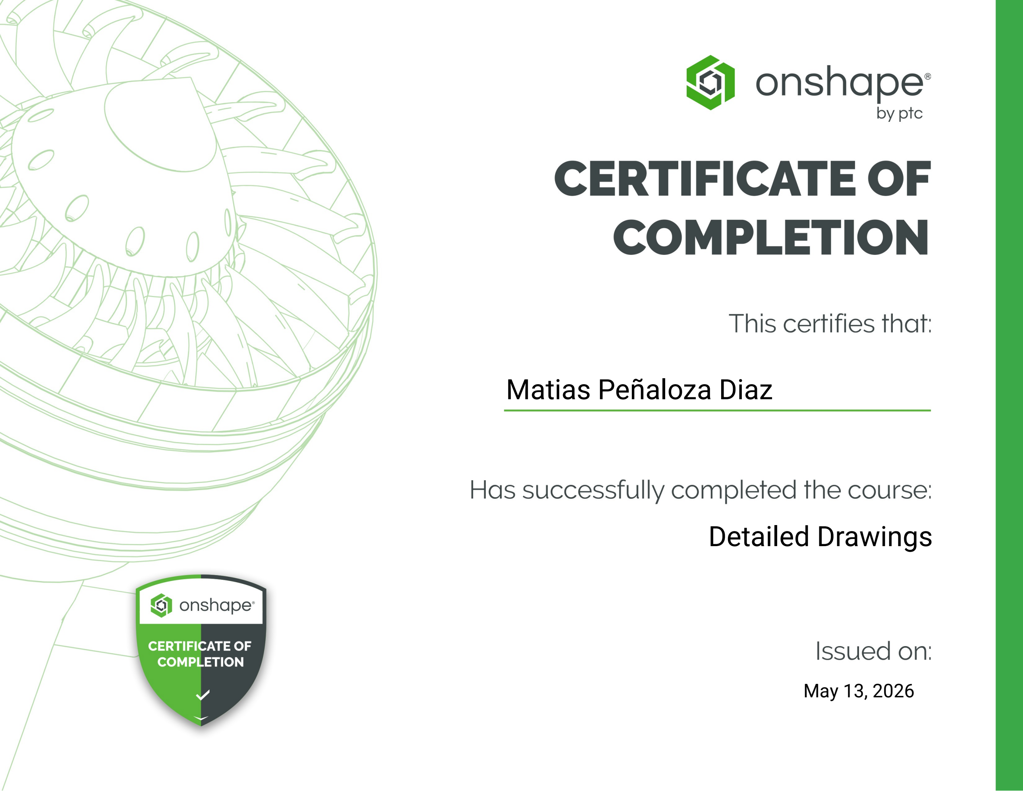
[picture p96: page 1]

Matias Peñaloza Diaz

May 13, 2026

Detailed Drawings
