Nadya-85/Grupo-3--FUNBIO/Documentación/Taller/Taller de Modelado 3D/Quezada Ponciano, Nadya/Certificado Detailed Drawings.pdf

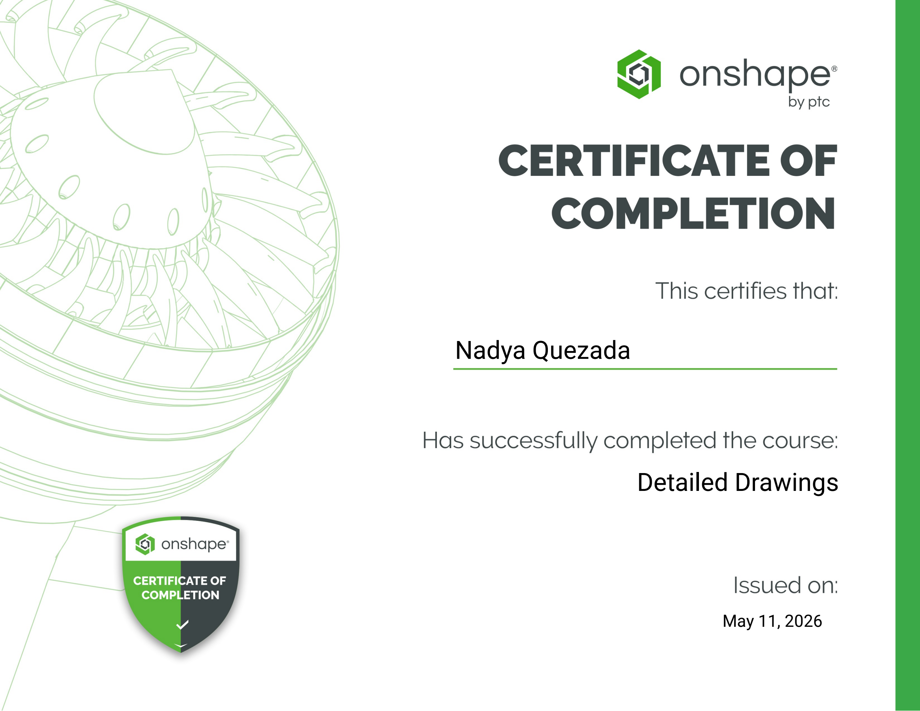
[picture p98: page 1]

Nadya Quezada

May 11, 2026

Detailed Drawings
