Nadya-85/Grupo-3--FUNBIO/Documentación/Taller/Taller de Modelado 3D/Silva Avileno, Fabiana/fabiana-silva-avileno-b40027ed-caf4-42f7-b9bb-7214b6094ab7-certificate.pdf

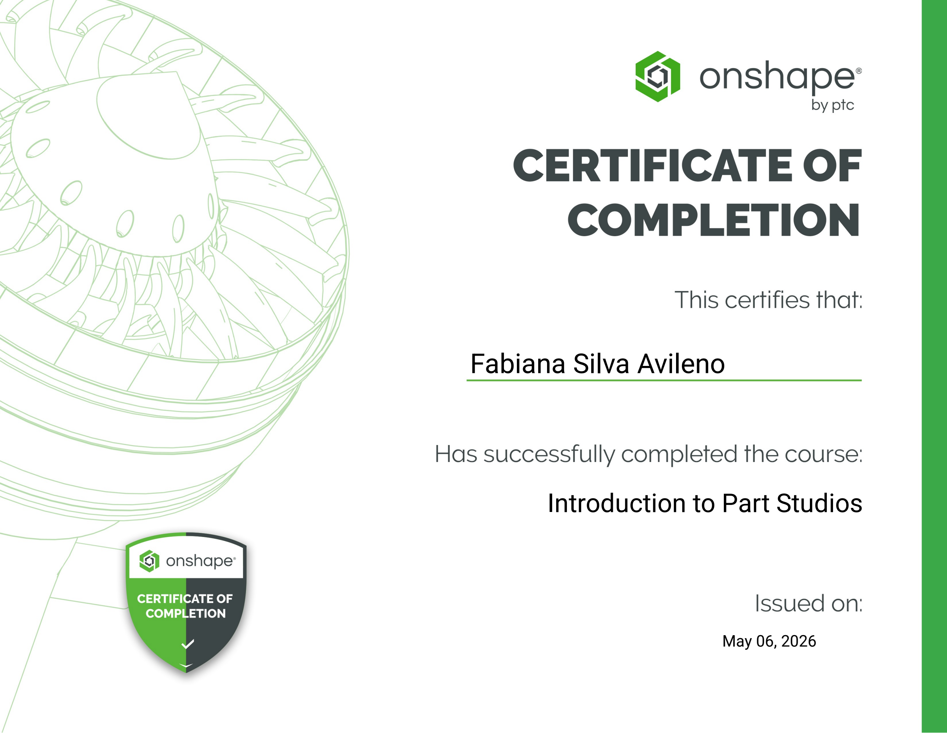
[picture p99: page 1]

Fabiana Silva Avileno

Introduction to Part Studios

May 06, 2026
