Nadya-85/Grupo-3--FUNBIO/Documentación/Taller/Taller de Modelado 3D/Silva Avileno, Fabiana/fabiana-silva-avileno-06bc0f4b-026d-48a2-befe-6cc15d7d204a-certificate.pdf

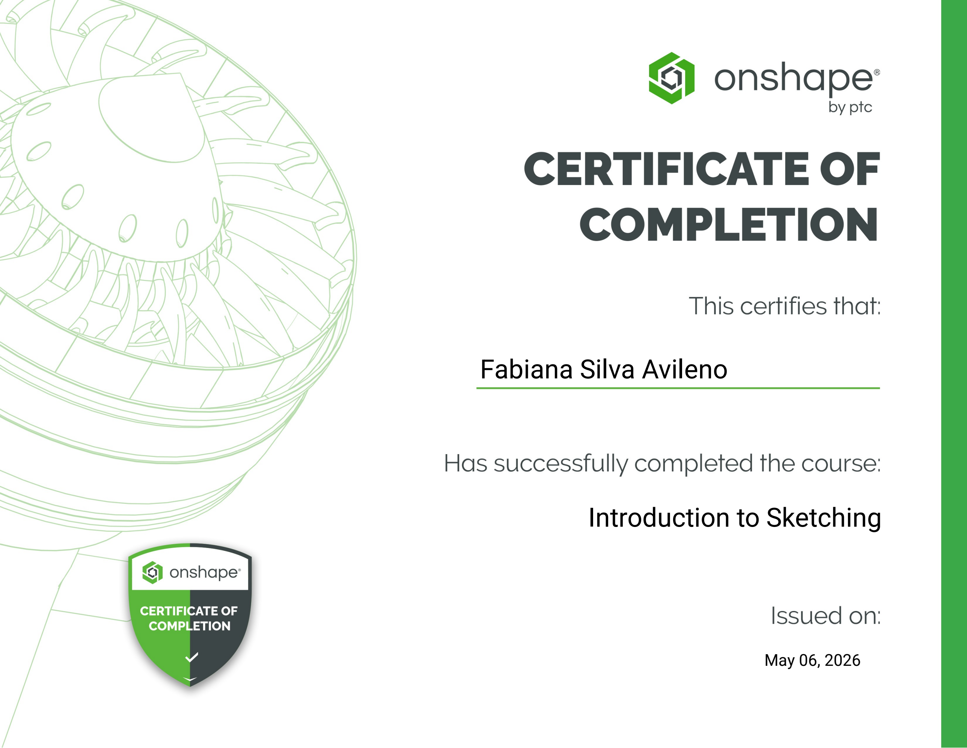
[picture p100: page 1]

Fabiana Silva Avileno

Introduction to Sketching

May 06, 2026
