Nadya-85/Grupo-3--FUNBIO/Documentación/Taller/Taller de Modelado 3D/Palacin Hilario, Jean/jeanpierre-palacin-hilario-adb4fa14-db75-4a18-b274-abc16a8aa3f7-certificate.pdf

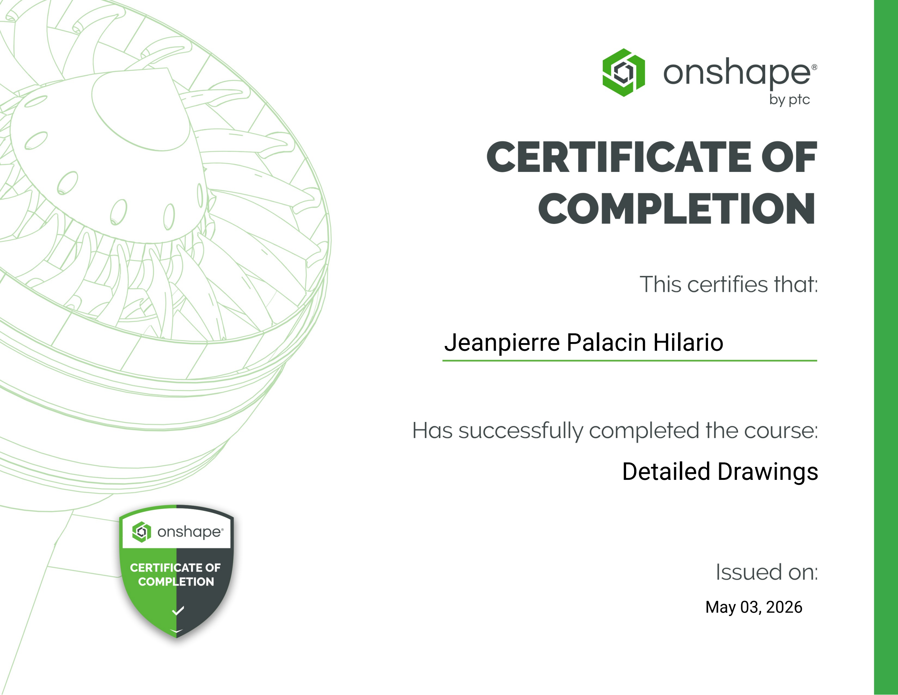
[picture p101: page 1]

Jeanpierre Palacin Hilario

May 03, 2026

Detailed Drawings
