Nadya-85/Grupo-3--FUNBIO/Documentación/Taller/Taller de Modelado 3D/Palacin Hilario, Jean/jeanpierre-palacin-hilario-bdbf6ba0-1abd-4a10-af73-c884655db4cd-certificate.pdf

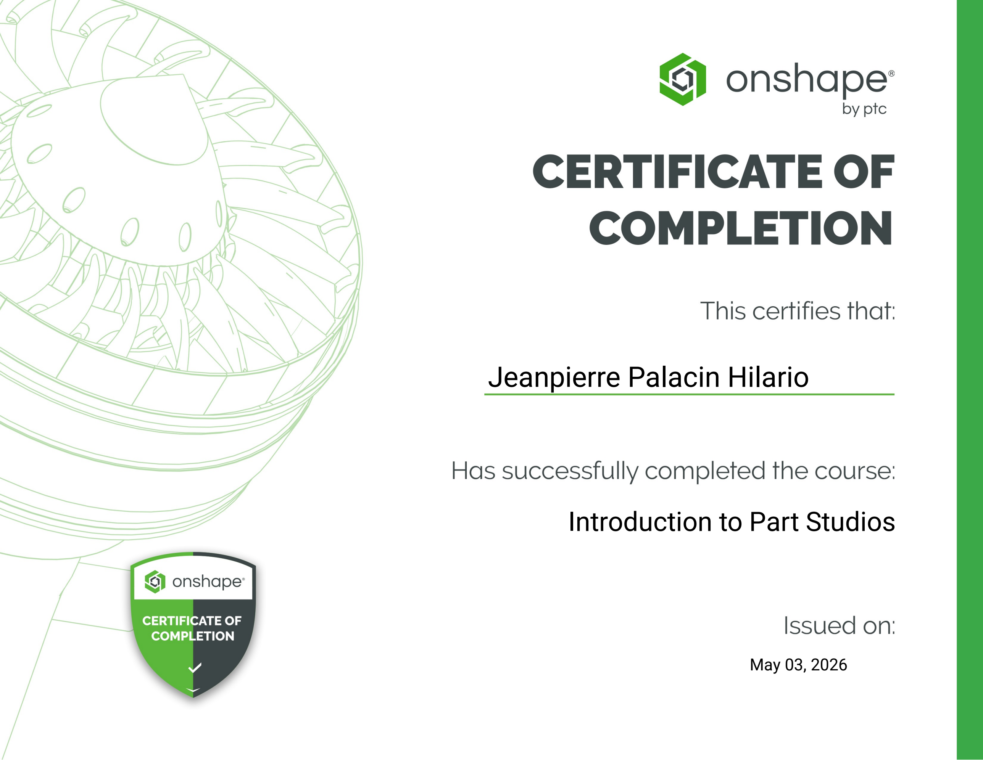
[picture p102: page 1]

Jeanpierre Palacin Hilario

Introduction to Part Studios

May 03, 2026
