Nadya-85/Grupo-3--FUNBIO/Documentación/Taller/Taller de Modelado 3D/Palacin Hilario, Jean/jeanpierre-palacin-hilario-ed611196-b9ae-48b9-a2fc-f8175e02a7de-certificate.pdf

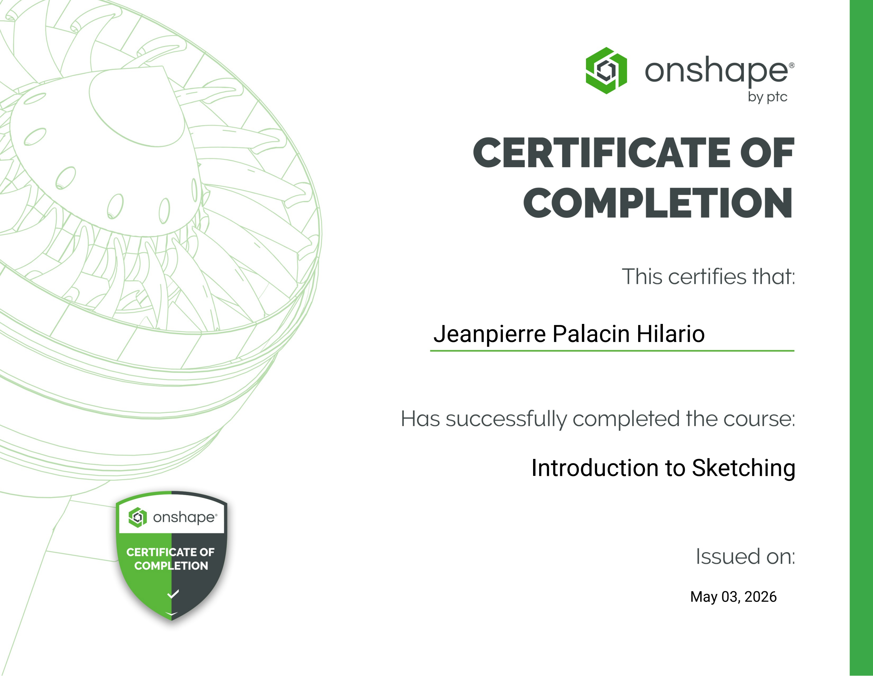
[picture p103: page 1]

Jeanpierre Palacin Hilario

Introduction to Sketching

May 03, 2026
