Nadya-85/Grupo-3--FUNBIO/Documentación/Taller/Taller de Modelado 3D/Quezada Ponciano, Nadya/Certificado Introduction to Part Studios.pdf

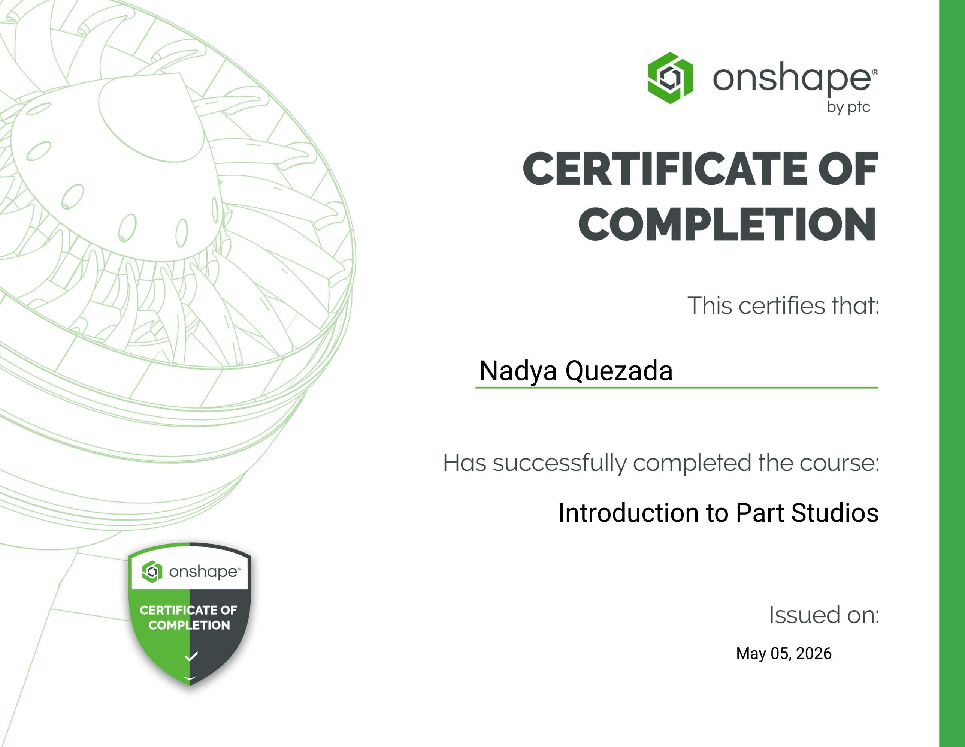
[picture p104: page 1]

Nadya Quezada

Introduction to Part Studios

May 05, 2026
