Nadya-85/Grupo-3--FUNBIO/Documentación/Taller/Taller de Modelado 3D/Quezada Ponciano, Nadya/Certificado Introduction to Sketching.pdf

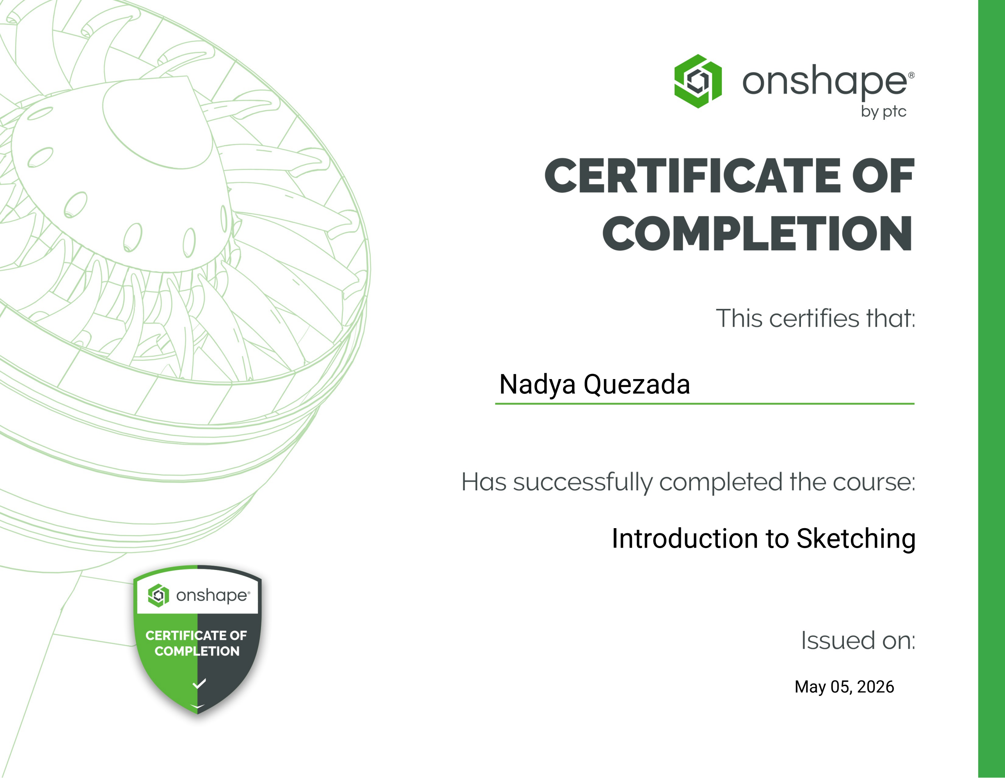
[picture p105: page 1]

Nadya Quezada

Introduction to Sketching

May 05, 2026
