Nadya-85/Grupo-3--FUNBIO/Documentación/Taller/Taller de Modelado 3D/Ramirez Rodrigruez, Alexandra/DIBUJO DETALLADO.pdf

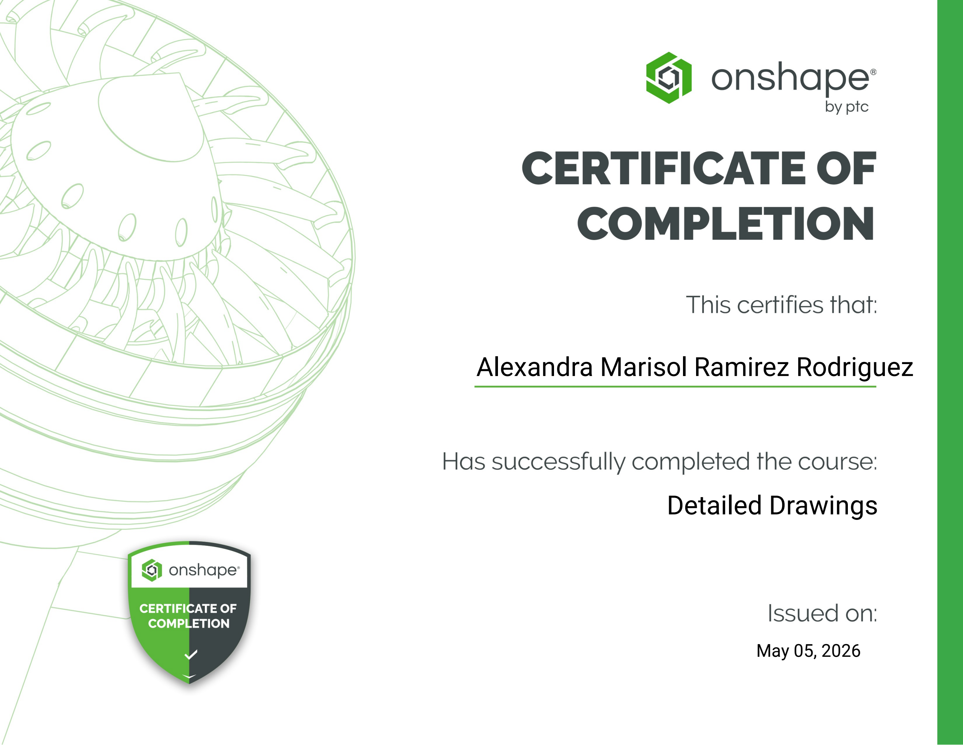
[picture p106: page 1]

Alexandra Marisol Ramirez Rodriguez

May 05, 2026

Detailed Drawings
