Nadya-85/Grupo-3--FUNBIO/Documentación/Taller/Taller de Modelado 3D/Ramirez Rodrigruez, Alexandra/INTRODUCCTION TO SKETCHING.pdf

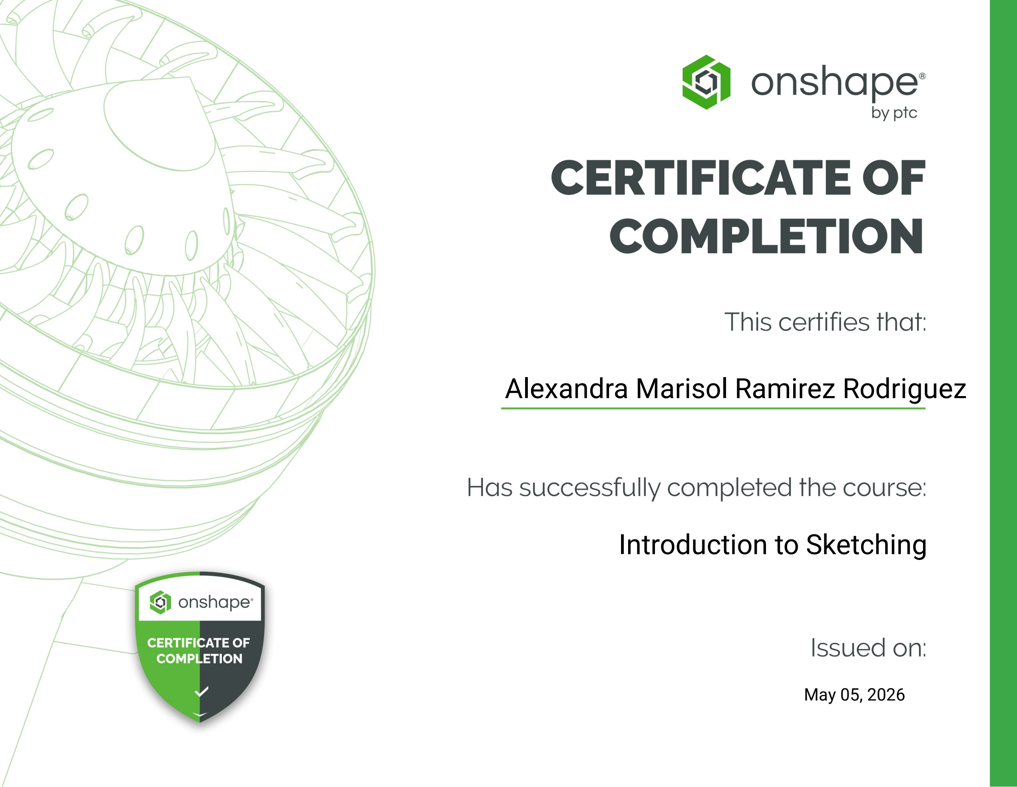
[picture p107: page 1]

Alexandra Marisol Ramirez Rodriguez

Introduction to Sketching

May 05, 2026
