Nadya-85/Grupo-3--FUNBIO/Documentación/Taller/Taller de Modelado 3D/Ramirez Rodrigruez, Alexandra/INTRODUCION A PART STUDIO.pdf

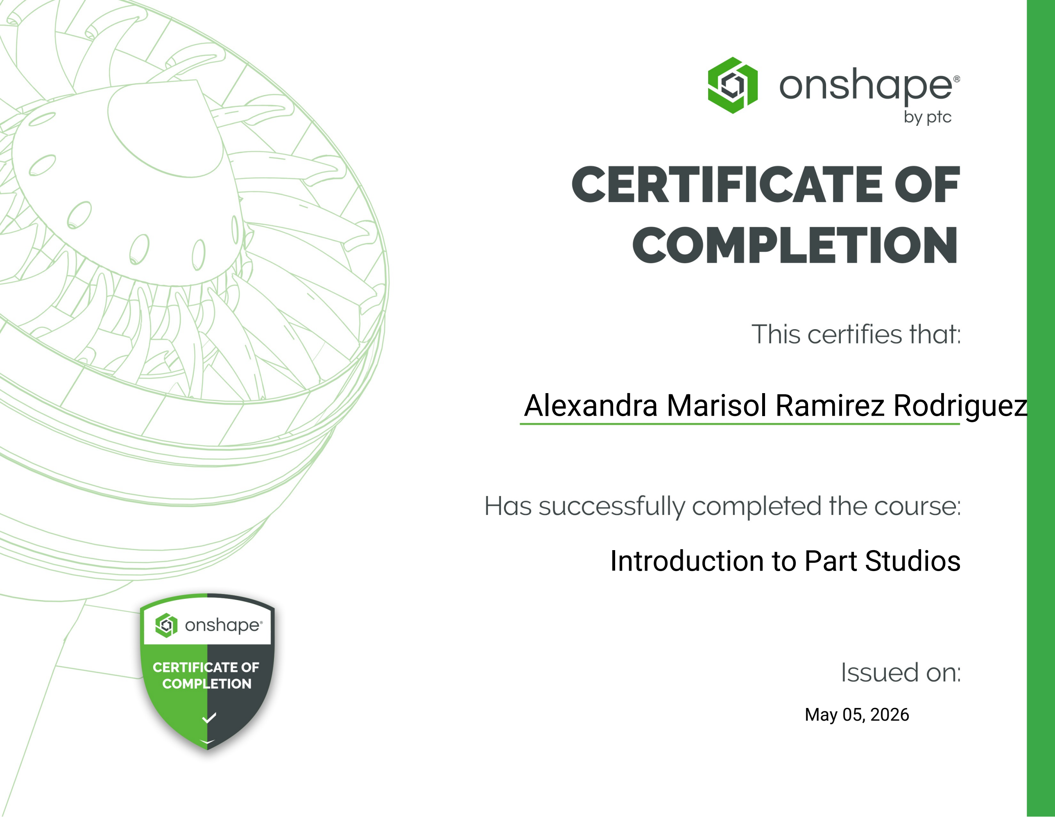
[picture p108: page 1]

Alexandra Marisol Ramirez Rodriguez

Introduction to Part Studios

May 05, 2026
