Nadya-85/Grupo-3--FUNBIO/Documentación/Taller/Taller de Modelado 3D/Peñaloza Días, Matías/CERTIFICADO Introduction to Part Studios.pdf

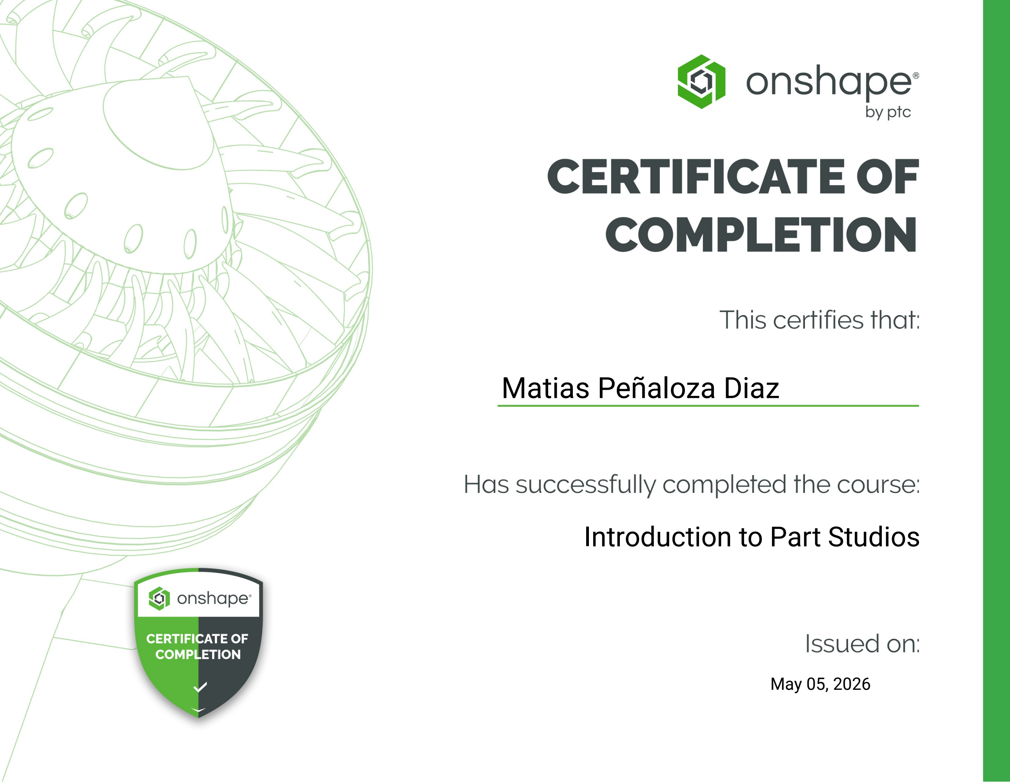
[picture p109: page 1]

Matias Peñaloza Diaz

Introduction to Part Studios

May 05, 2026
