Nadya-85/Grupo-3--FUNBIO/Documentación/Taller/Taller de Modelado 3D/Peñaloza Días, Matías/CERTIFICADO Introduction to Sketching.pdf

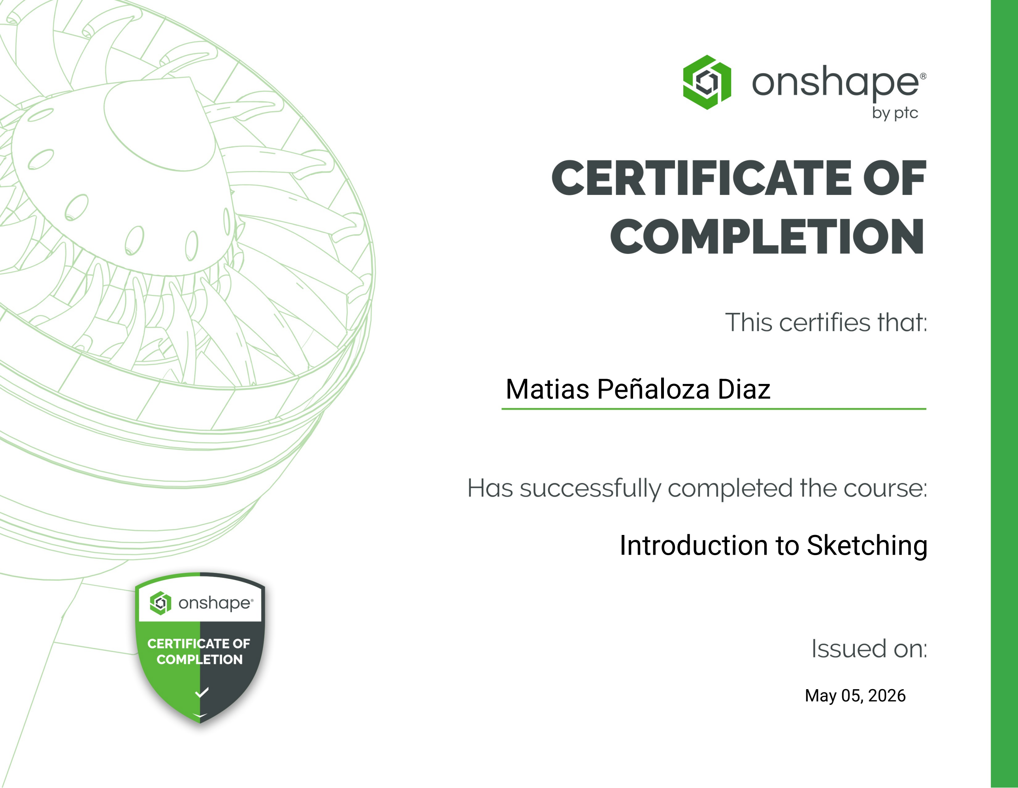
[picture p110: page 1]

Matias Peñaloza Diaz

Introduction to Sketching

May 05, 2026
