Nadya-85/Grupo-3--FUNBIO/Documentación/Taller/Taller de Modelado 3D/Fajardo Peña, Edwin/Dibujos detallados.pdf

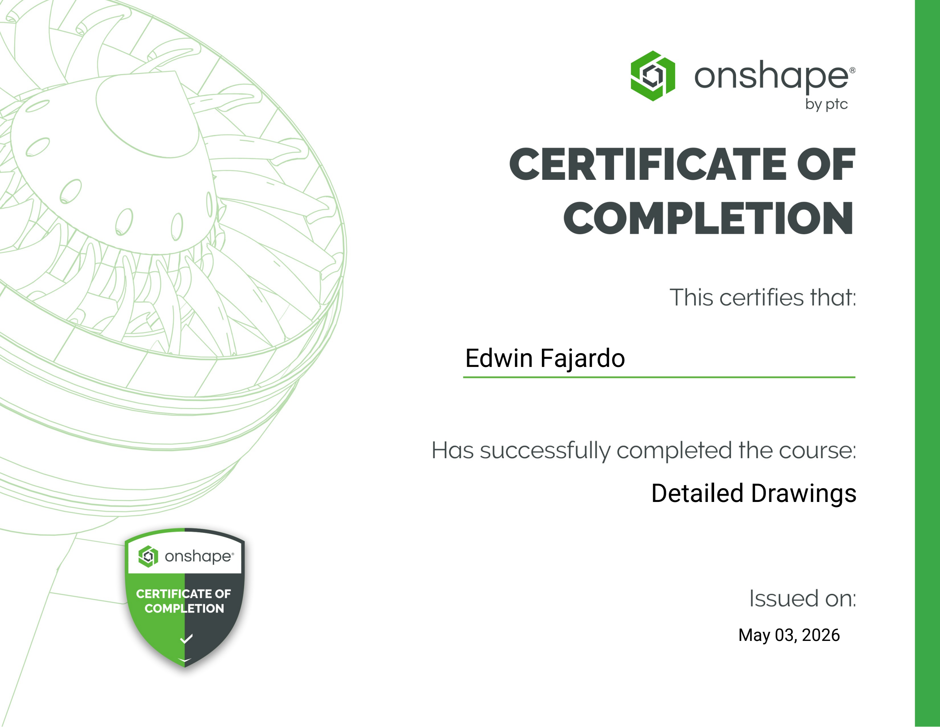
[picture p111: page 1]

Edwin Fajardo

May 03, 2026

Detailed Drawings
