Nadya-85/Grupo-3--FUNBIO/Documentación/Taller/Taller de Modelado 3D/Fajardo Peña, Edwin/Introducción a Part Studios.pdf

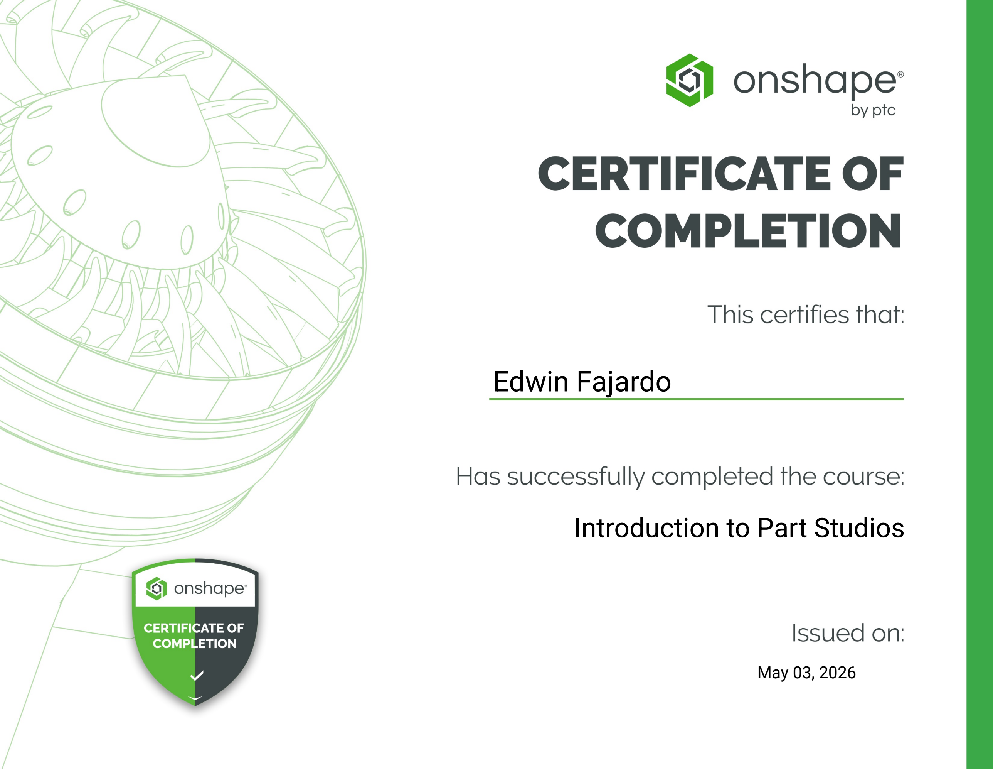
[picture p112: page 1]

Edwin Fajardo

Introduction to Part Studios

May 03, 2026
