Nadya-85/Grupo-3--FUNBIO/Documentación/Taller/Taller de Modelado 3D/Fajardo Peña, Edwin/Introducción al dibujo técnico.pdf

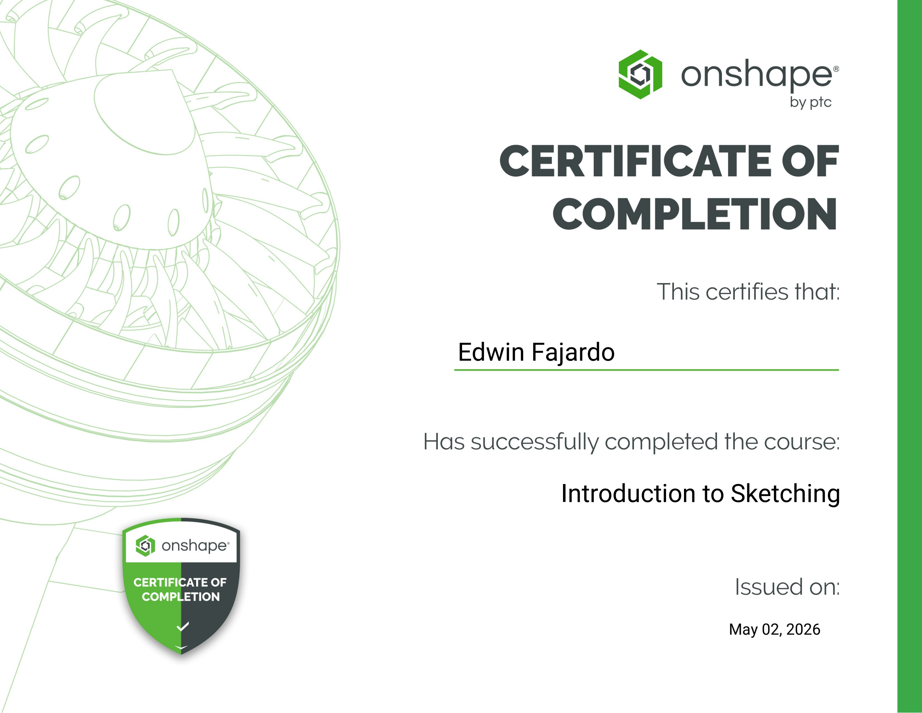
[picture p113: page 1]

Edwin Fajardo

Introduction to Sketching

May 02, 2026
