Nadya-85/Grupo-3--FUNBIO/Documentación/Hitos/Presentaciones/PPT Hito N°2 (1).pdf

GRUPO 03; HITO 2: SIMA

Sistema Inteligente de
Movilidad Asistida

# Integrantes y roles


1.Nadya Quezada Ponciano - Diseño y
Mecánica
2.Matías Peñaloza Díaz - Electrónica y
Diseño
3.Fabiana Valery Silva Avileno -
Diseño e Investigación
4.JeanPierre Palacin Hilario -
Electrónica y Programación
5.Edwin José Guillermo Fajardo Peña -
6.Alexandra Ramirez Rodriguez -
Prototipado

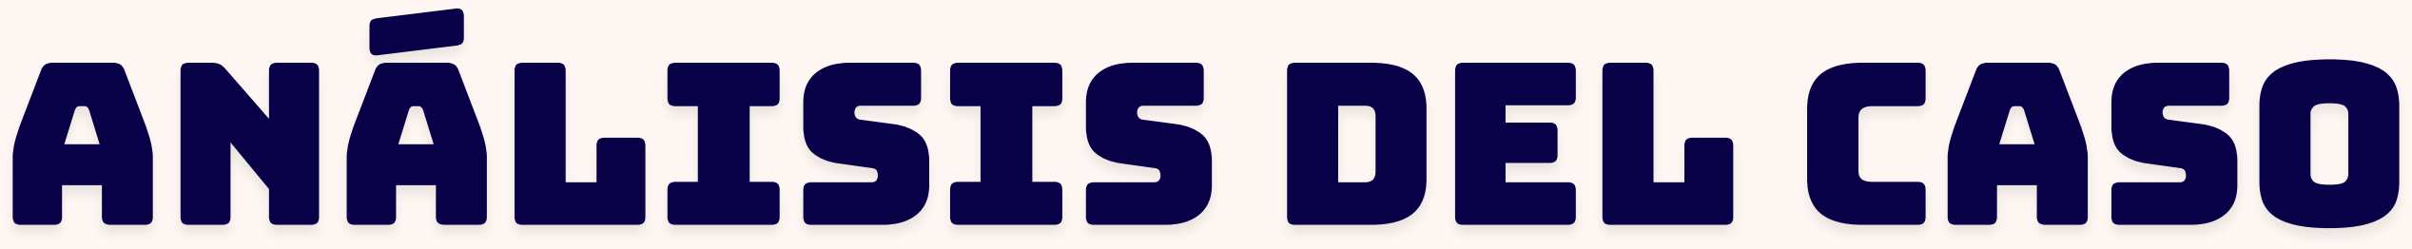
[picture p158: figure]
análisis del caso
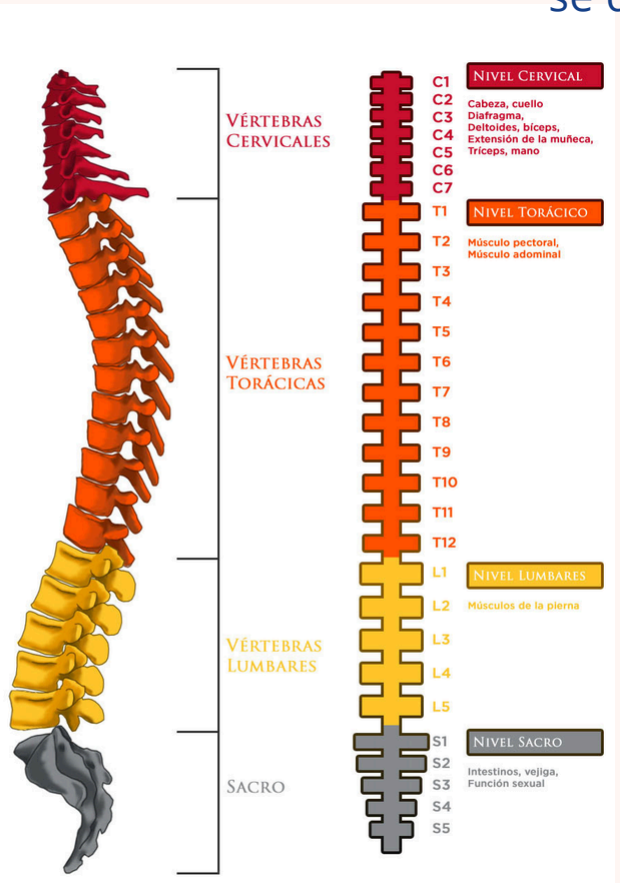
[picture p159: figure]

# C7 - ASIA “A”

## Más de 15,4 millones de personas con lesiones medulares y en la mayoría se deben a traumatismos causados por caídas o accidentes. OMS:

## Parálisis de miembros

inferiores.

## Aumento del tono muscular en extremidades inferiores

## Médula espinal: Transmitir información motora, sensitiva y autonómica entre el cerebro y el resto del cuerpo

## Ausencia total función motora ni sensitiva

## Debilidad en muñecas y

manos (C6-C8).

## Conserva función en

hombros y codos (C5).

# Problemática

## ¿Qué sucede en este caso?

hombros.; manual.; OMS:

Las sillas eléctricas son
costosas y reemplazan
totalmente la propulsión

Las sillas de ruedas
manuales requieren un alto
esfuerzo físico.

Produce fatiga en brazos y

El esfuerzo aumenta en
rampas y terrenos
irregulares.

Más de 80 millones de personas en el
mundo requieren una silla de ruedas, y
muchas no tienen acceso a soluciones
eléctricas por su alto costo.

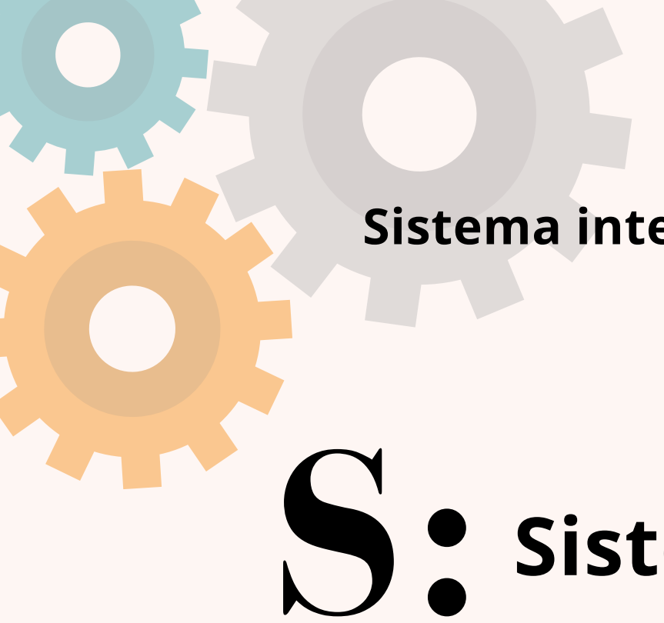
[picture p160: figure]
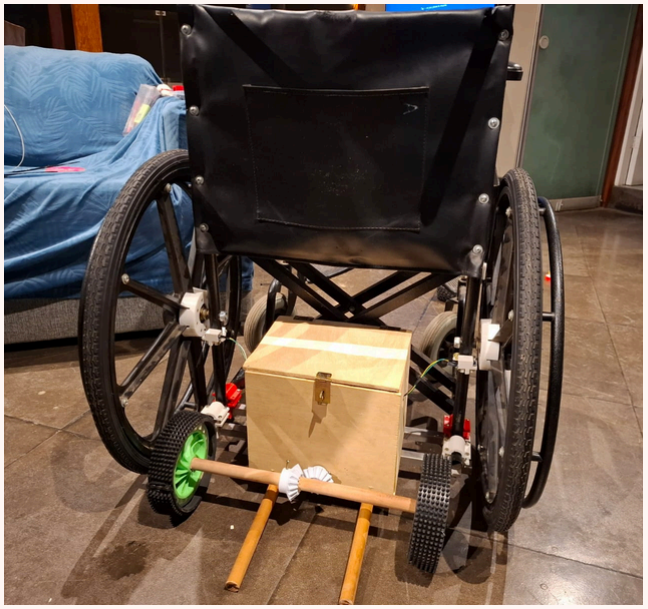
[picture p161: figure]

I:

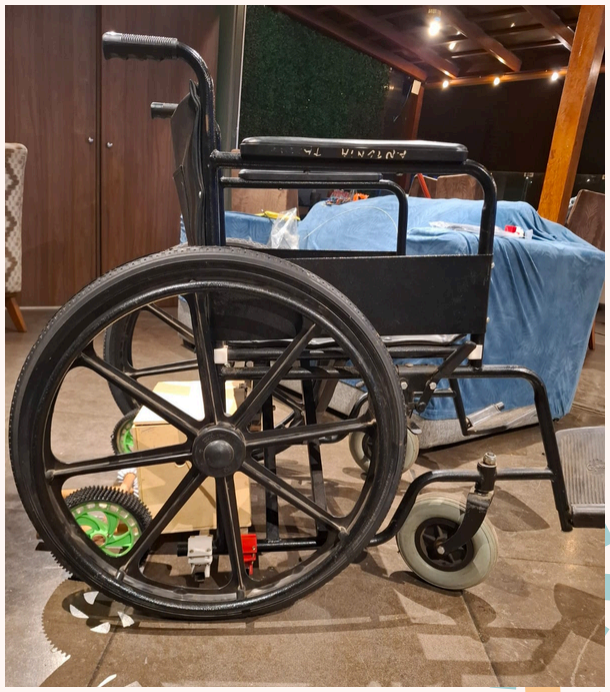
[picture p162: figure]

M:
A:

# Sistema

# Asistida

# Movilidad

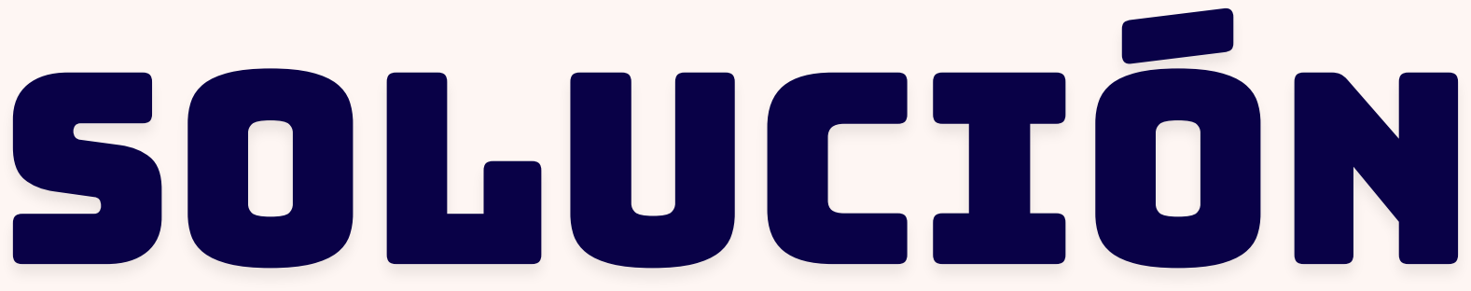
[picture p163: figure]
Solución

# Inteligente

Sistema inteligente de asistencia adaptable para sillas de ruedas manuales.

# funcionamiento

El MPU6050 detecta continuamente la inclinación del terreno.

El ESP32 procesa
dicha información
junto con la
velocidad medida
mediante sensores
Hall.

El driver BTS7960
controla el motor de
asistencia entregando
únicamente la potencia
necesaria para facilitar
el desplazamiento.

# Tracción

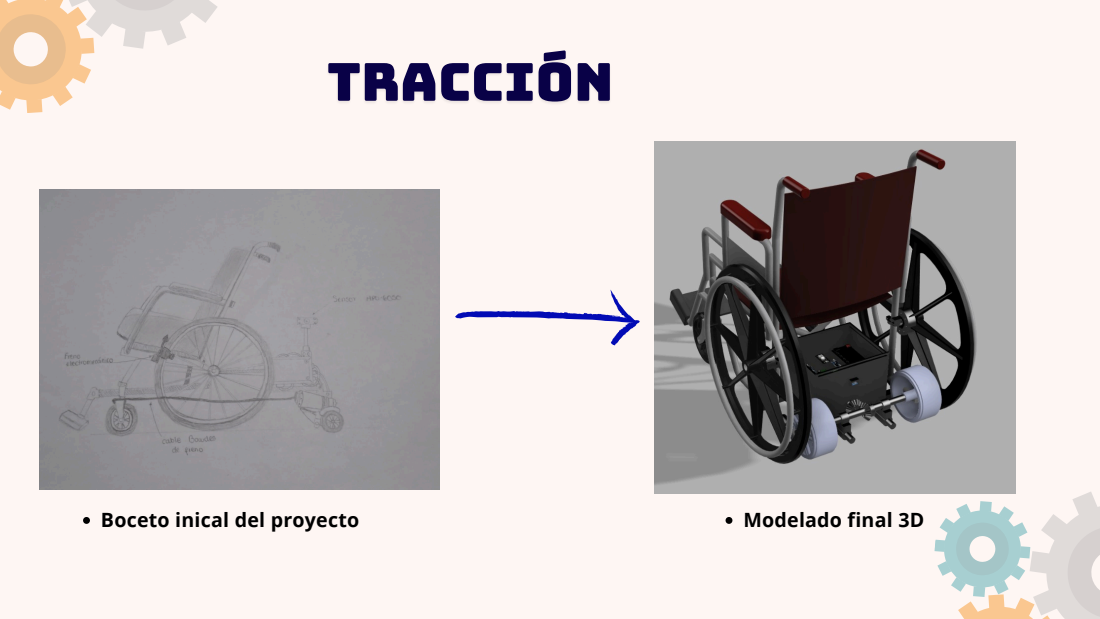
[picture p164: page 7]
Boceto inical del proyecto; Modelado final 3D

# manufacturación digital

## Durante el proceso se realizaron múltiples interacciones de fabricación

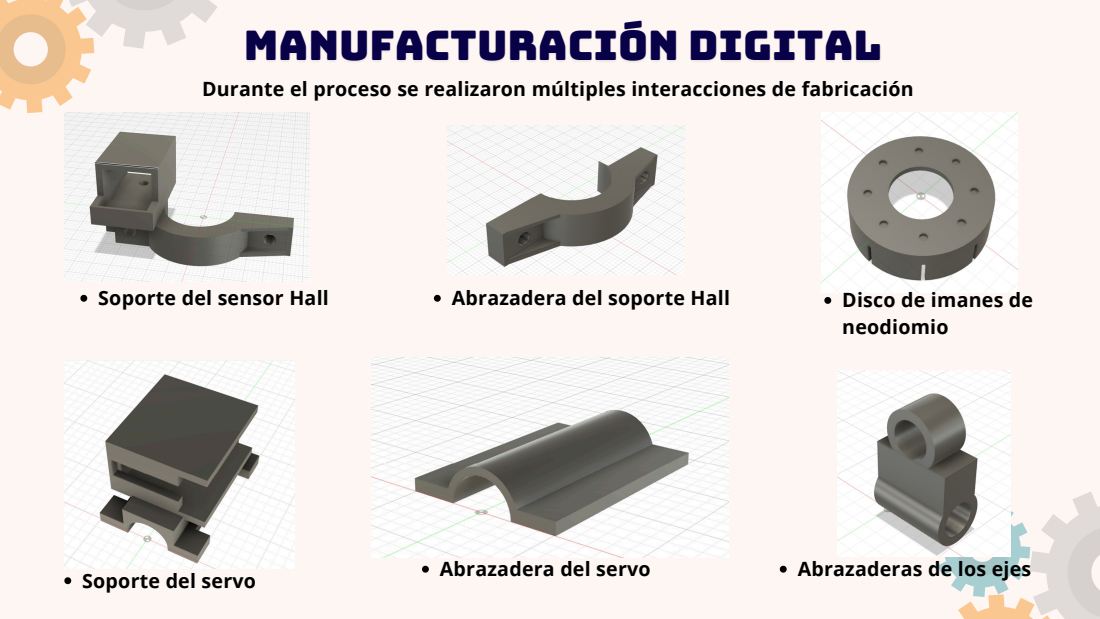
[picture p165: page 8]

Soporte del sensor Hall

Abrazadera del soporte Hall

Disco de imanes de
neodiomio

Abrazadera del servo

Abrazaderas de los ejes

Soporte del servo

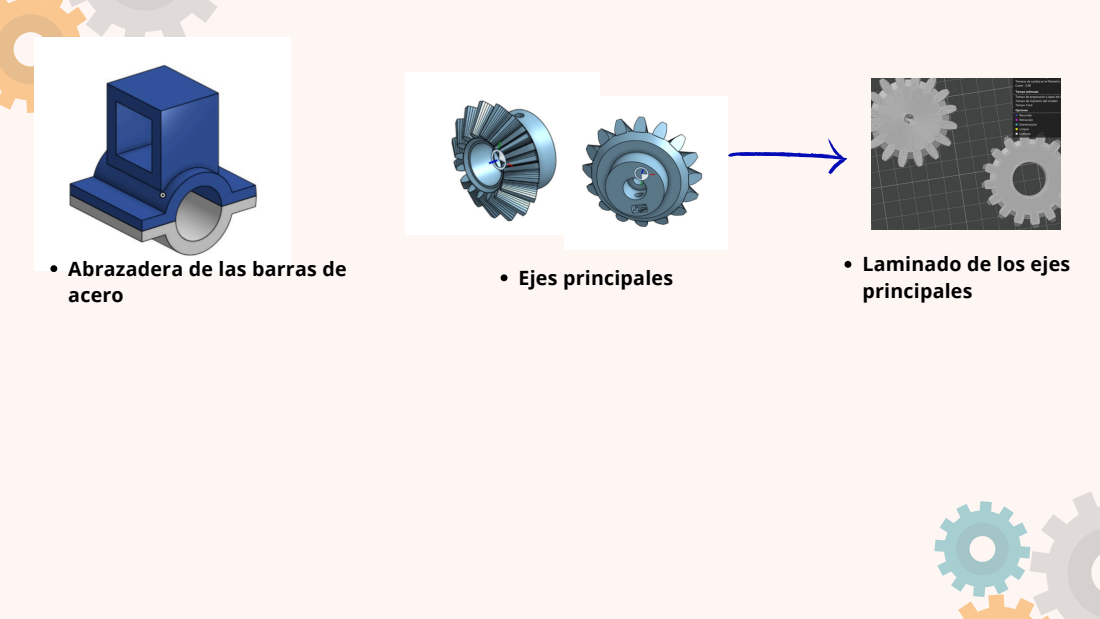
[picture p166: page 9]

# DIAGRAMA DEL PROTOTIPADO


# DIAGRAMA DEL PROTOTIPADO

https://cdn.phototourl.com/free/2026-07-01-995f4cc3-2f15-4c13-87ca-a7493f3b246b.png

# COMPONENTES ELECTRÓNICOS

## ESP32: unidad principal de procesamiento


Componente | Cantidad

ESP32 | 1

MPU6050: mide inclinación
BTS7950: control del motor
Motor DC 24V: proporciona la asistencia
Sensores Hall: calculan la velocidad
Convertidores Buck: alimenta la electrónica

Sensor MPU6050 | 1

Sensor Hall A3144 | 2

Imanes de neodimio | 16

Driver BTS7960 | 1

Motorreductor DC 24 V | 1

Batería de 24 V | 2

Convertidor Buck DC-DC | 1

Fusible | 1

Protoboard | 1

Todo el sistema comparte una referencia
común de tierra para garantizar una
correcta comunicación entre los módulos.

Cables de conexión | Según necesidad

Servo motor SG5010 | 2

# COMPONENTES ELECTRÓNICOS


# COMPONENTES ELECTRÓNICOS

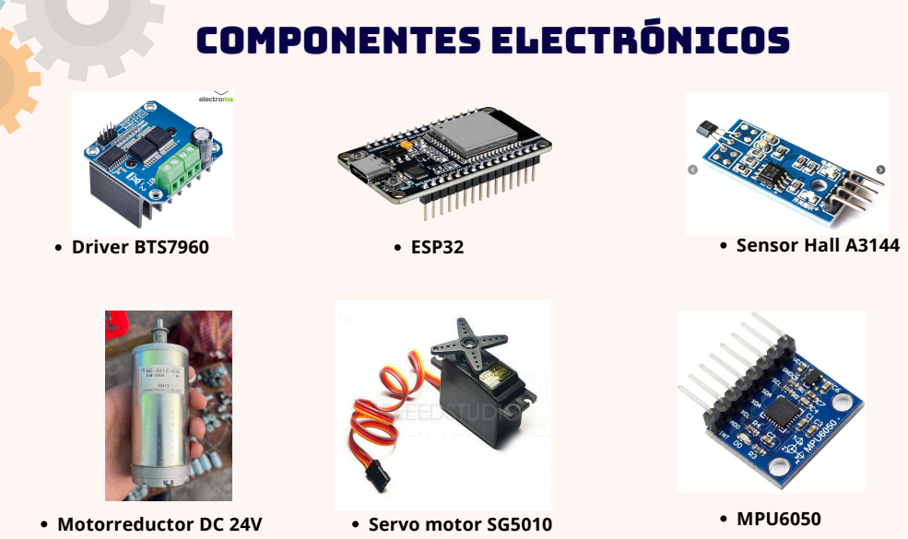
[picture p167: page 13]
Driver BTS7960; Servo motor SG5010; ESP32; Motorreductor DC 24V; MPU6050; Sensor Hall A3144

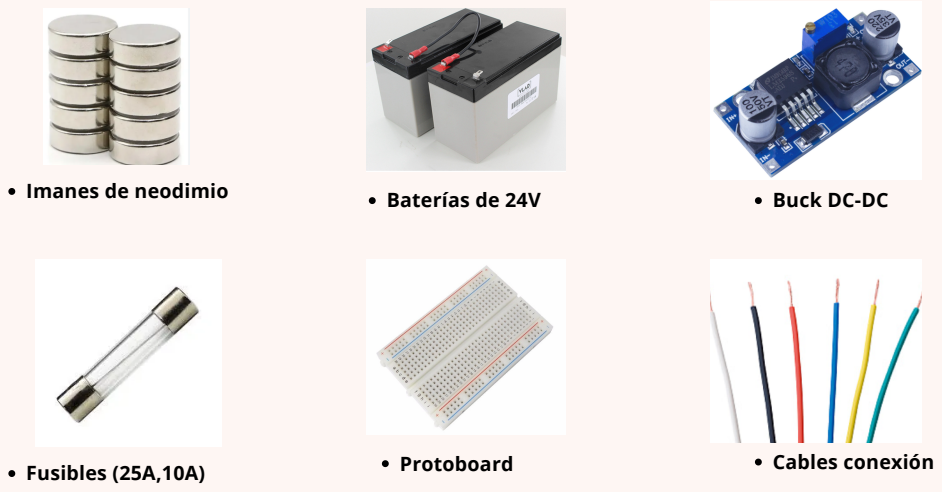
[picture p168: page 14]
Imanes de neodimio; Baterías de 24V; Buck DC-DC; Fusibles (25A,10A); Protoboard; Cables conexión

# ENSAMBLAJE ELECTRÓNICO


# ENSAMBLAJE ELECTRÓNICO

# modelado final 3d

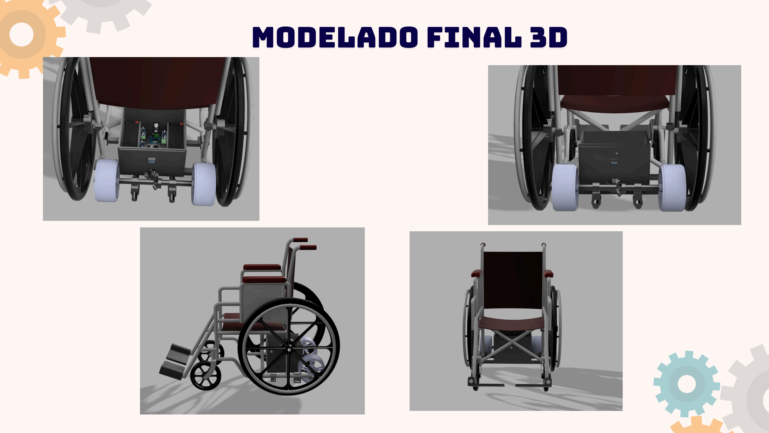
[picture p169: page 16]

# animación 3d


# ensamblaje del prototipado

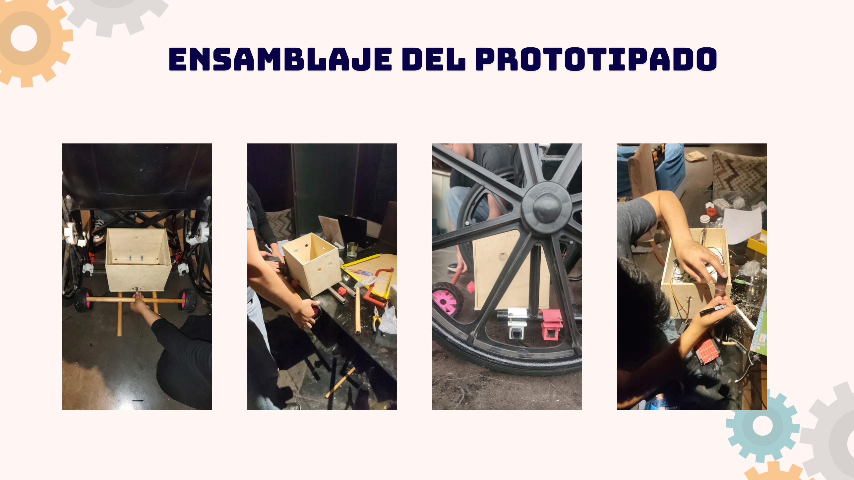
[picture p170: page 18]

# Funcionamiento del sistema electrónico


# Funcionamiento del sistema electrónico

Funcionamiento del sistema electrónico
evidencia del motor en funcionamiento

Limitación | Impacto | Medidas implementadas
Calibración del sensor de inclinación | Pequeñas inclinaciones iniciales alteraban la lectura | Se implementó una calibración automática al encender el sistema.
Asistencia dependiente de condiciones reales | El peso del usuario y el terreno modifican la respuesta | Se integraron sensores Hall para futuras estrategias de control adaptativo.
Limitaciones de espacio | Restricciones para ubicar los componentes | Se rediseñaron soportes mediante impresión 3D para optimizar el ensamblaje.
Consumo de corriente del motor | Altas corrientes durante el arranque | Se seleccionó un driver BTS7960 y fusibles de protección adecuados.

# Slide extra: Limitaciones

Trabajo futuro
Optimizar el algoritmo utilizando simultáneamente inclinación y velocidad. Realizar pruebas con usuarios de diferentes pesos y pendientes. Implementar estrategias de ahorro energético y protección térmica.

## Mejoras implementadas

# resultados

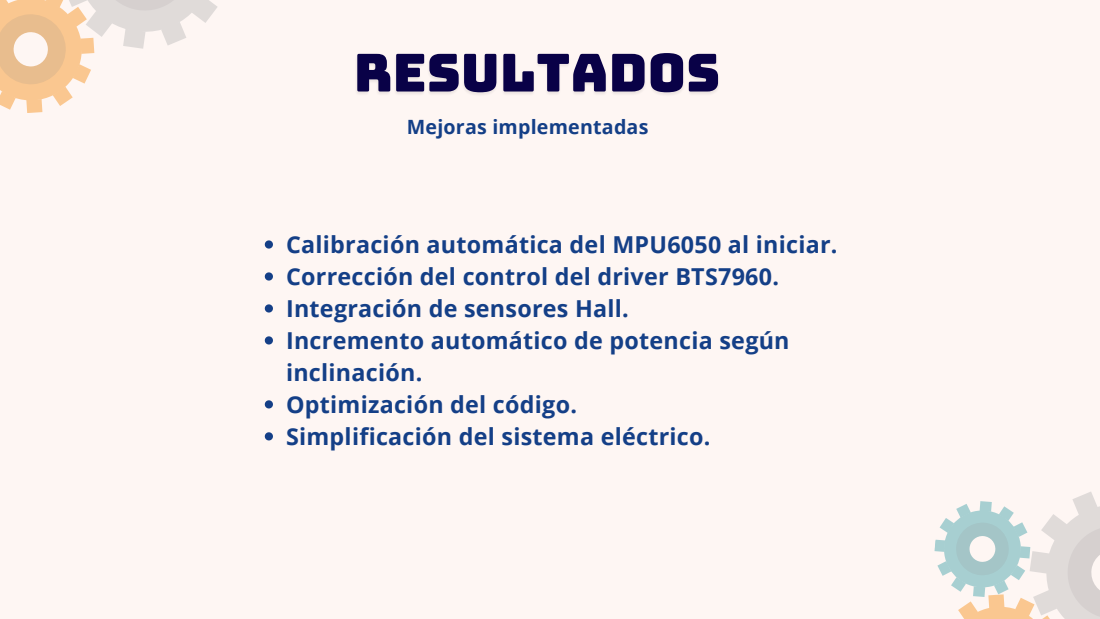
[picture p171: page 22]

Calibración automática del MPU6050 al iniciar.
Corrección del control del driver BTS7960.
Integración de sensores Hall.
Incremento automático de potencia según
inclinación.
Optimización del código.
Simplificación del sistema eléctrico.

## Cuadro de Relación: Inclinación (MPU6050) vs Respuesta del Motor

# resultados


Estado del terreno | Lectura MPU6050 | PWM aplicado | Respuesta del sistema

Bajada | Menor a -3° | 0 | Motor libre. Sin asistencia.

Plano | -3° a 3° | 95–120 | Asistencia mínima para vencer la inercia con baja velocidad.

Subida leve | 3° a 8° | 100–125 | Incremento moderado de torque manteniendo velocidad controlada.

Subida media | 8° a 14° | 125–145 | Mayor asistencia para facilitar el ascenso.

Subida fuerte | 14° a 18° | 145–155 | Asistencia máxima limitada para priorizar torque.

Arranque inicial | Durante los primeros 250 ms | 190 | Impulso corto para iniciar el movimiento sin mantener alta velocidad.

## Prototipo integrado

# resultados


Módulo | Variable evaluada | Criterio de aceptación | Resultado esperado

MPU6050 | Ángulo de inclinación | Lectura estable y calibración al inicio | Detección de plano, subida y bajada

Motor DC 24 V | Asistencia | Entrega de torque desde PWM mínimo | Inicio con suficiente fuerza

Driver BTS7960 | Control PWM | Respuesta a RPWM/LPWM sin fallos | Modulación estable del motor

Sensor Hall izquierdo | Pulsos | Conteo sin pérdidas | Velocidad rueda izquierda

Sensor Hall derecho | Pulsos | Conteo sin pérdidas | Velocidad rueda derecha

ESP32 | Procesamiento | Lectura y control en tiempo real | Control coordinado del sistema

Buck 24→5 V | Alimentación | 5 V estables | Funcionamiento de ESP32 y MPU

Buck 24→6 V | Alimentación servos | 6 V estables | Preparado para futura integración

# Slide extra: pruebas/test


Prueba | Objetivo | Resultado | Estado

ESP32 | Verificar programación y comunicación serial | Correcto | ✓

MPU6050 | Lectura de inclinación y calibración | Correcto | ✓

Driver BTS7960 | Control del motor mediante PWM | Correcto | ✓

Motor DC 24 V | Respuesta a diferentes niveles de PWM | Correcto | ✓

Sensores Hall | Conteo de pulsos y cálculo de velocidad | Correcto | ✓

Comunicación I²C | Detección del MPU6050 | Correcto | ✓

Fuente de alimentación | Estabilidad de voltajes | Correcto | ✓

Integración del sistema | Funcionamiento conjunto del prototipo | Correcto | ✓

# GRACIAS


# Referencias

[1] R. Rupp, F. Biering-Sørensen, S.P. Burns, D.E. Graves, J. Guest, L. Jones, M. Schmidt Read, G.M. Rodriguez, C. Schuld, K.E. Tansey, K. Walden, S. Kirshblum: International Standards for Neurological Classification of Spinal Cord Injury: Revised 2019. Top Spinal Cord Inj Rehabil 27 (2): 1–22, 2021. https://doi.org/10.46292/sci2702-1
[2] R. Splittgerber,

“Snell: Neuroanatomía clínica, 8e,

” Jan. 01, 2019. https://cienciasbasicas.lwwhealthlibrary.com/book.aspx?bookid=2891 (https://cienciasbasicas.lwwhealthlibrary.com/book.aspx?bookid=2891)

[3] World Health Organization: WHO,

“Lesión de la médula espinal,

” Apr. 16, 2024. https://www.who.int/es/news-room/fact-sheets/detail/spinal-cord-injury (https://www.who.int/es/news-room/fact-sheets/detail/spinal-cord-injury)

[4] S. C. Golden Jr.,

“Joint movement detection device and system for coordinating motor output with manual wheelchair propulsion,

” US20160361213A1, 2016.

[5] J. W. Britz,

“Wheelchair propulsion assist device,

” Patente US11590039B1.

[6] E. Peskin, V. Nagar, A. Wilson, and J. Slavin,

“Removable power assist for manual wheelchair,

” US10945899B2, Mar. 16, 2021.

[7] Rehabilitation Engineering and Assistive Technology Society of North America (RESNA),

“Meet the 2024 Developers' Showcase Participants,

” RESNA Member News, Jun. 5, 2024. [Online]. Available: https://www.resna.org/About/RESNA-News/Member-News?ArticleID=871&ArtMID=1009. (https://www.resna.org/About/RESNA-News/Member-News?ArticleID=871&ArtMID=1009) [Accessed: May 2, 2026].
[8] Wheel Freedom. (s.f.). Empulse StreetJet Handbike. https://www.wheelfreedom.com/products/empulse-streetjet/delivery
