Nadya-85/Grupo-3--FUNBIO/Documentación/Entregables/Presentaciones/PPT Entregable N°9_20260603_001016_0000.pdf

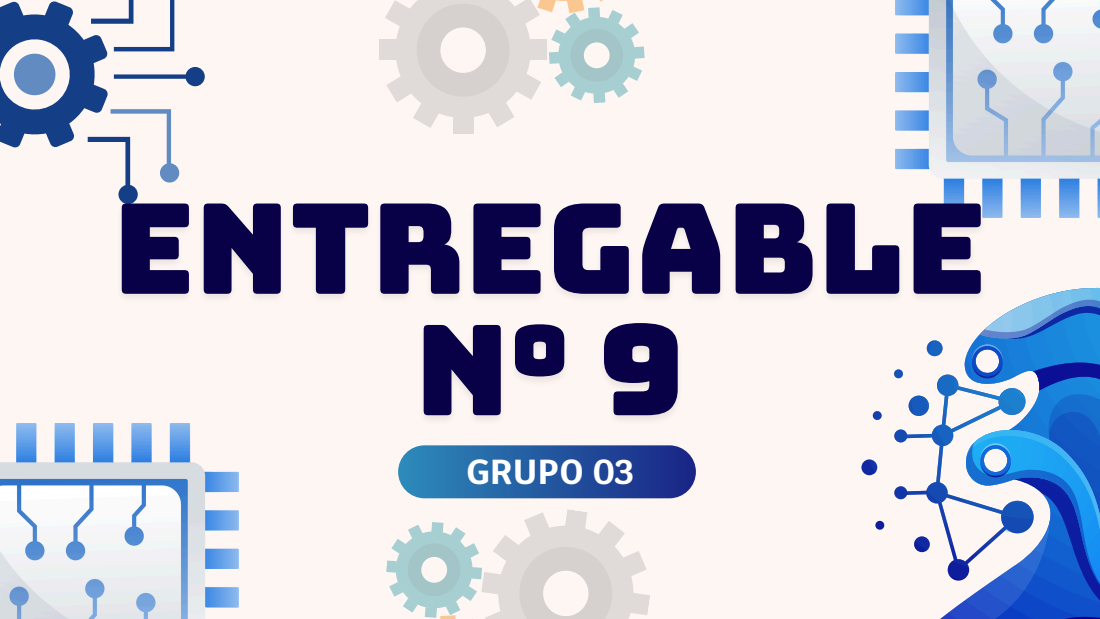
[picture p180: page 1]
GRUPO 03; ENTREGABLE N° 9

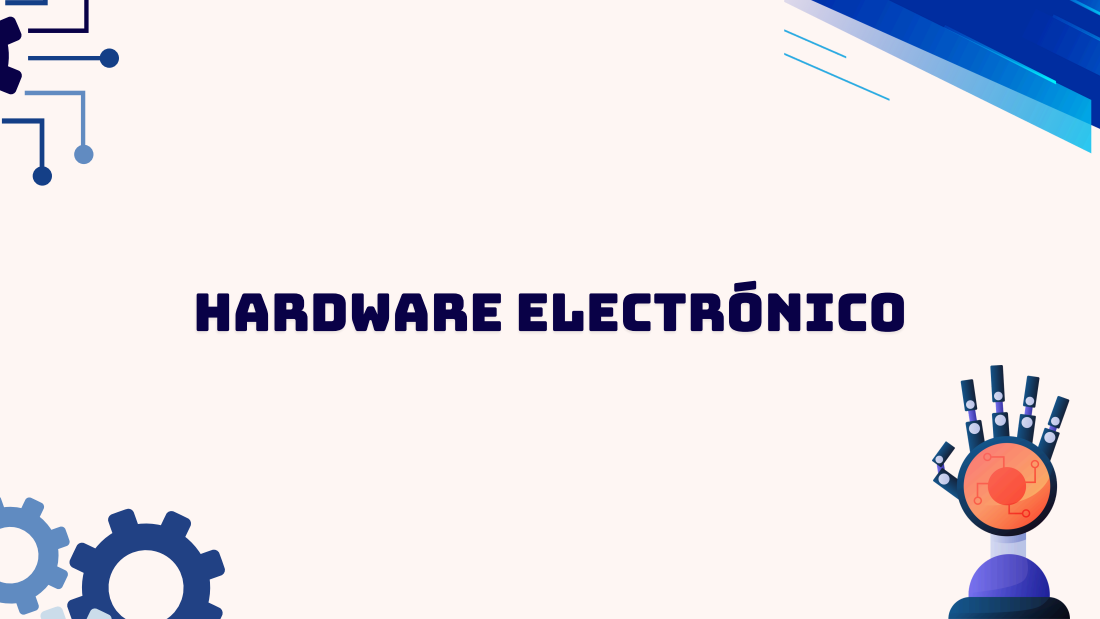
[picture p181: page 2]
Hardware electrónico

# Diseño esquemático del circuito electrónico

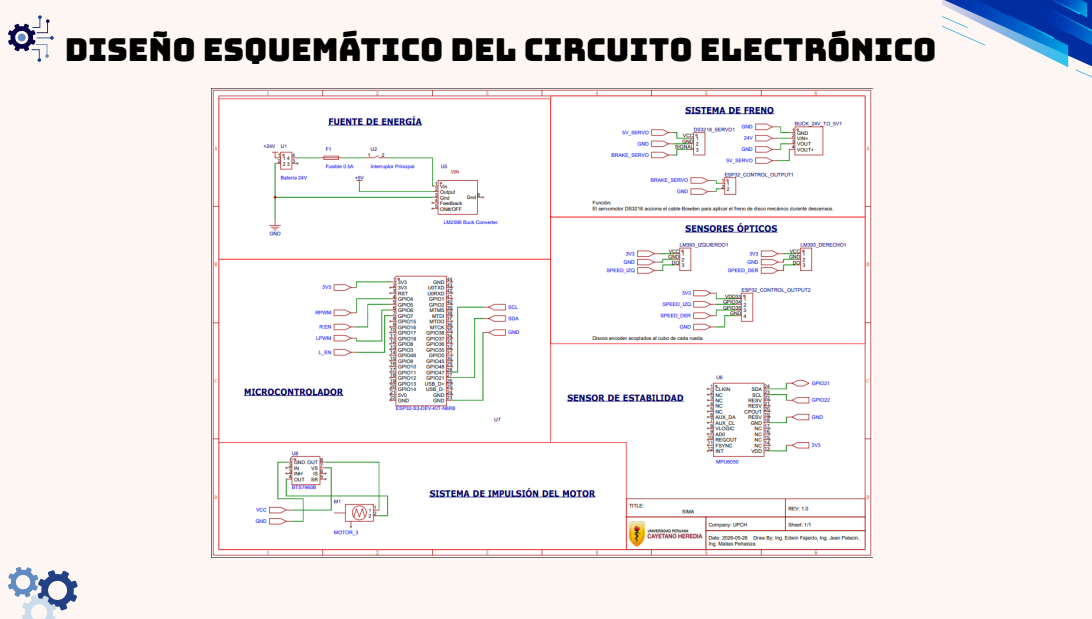
[picture p182: page 3]

# Ejecución del código ESP32 con componentes físico implementados

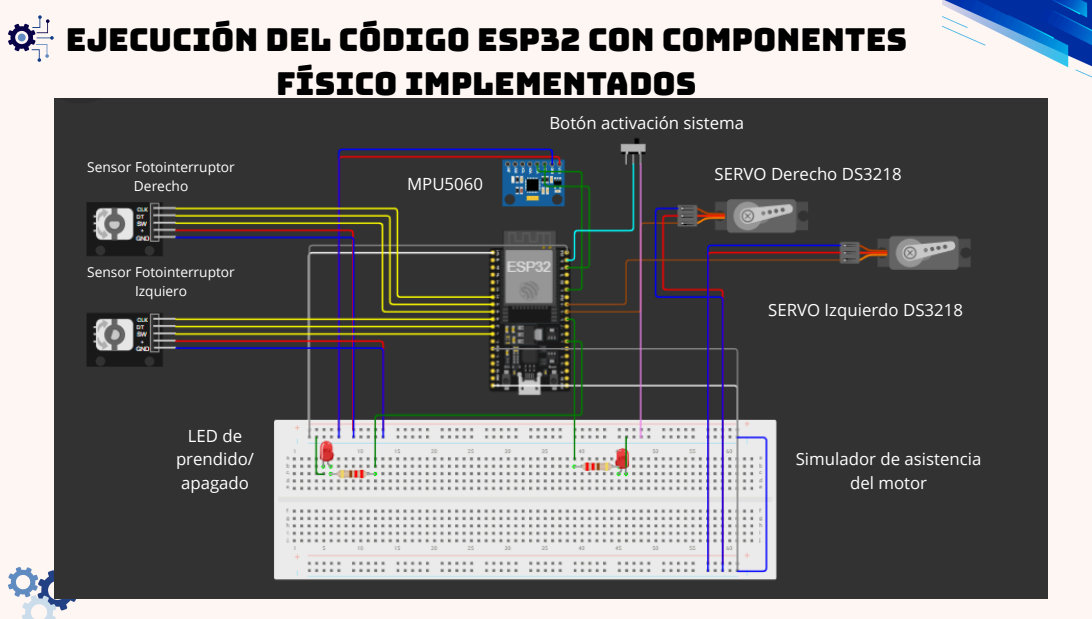
[picture p183: page 4]
SERVO Derecho DS3218; SERVO Izquierdo DS3218; MPU5060; Sensor Fotointerruptor Derecho; Sensor Fotointerruptor Izquiero; LED de prendido/ apagado

Botón activación sistema

Simulador de asistencia
del motor

# Avance de su prototipado electrónico

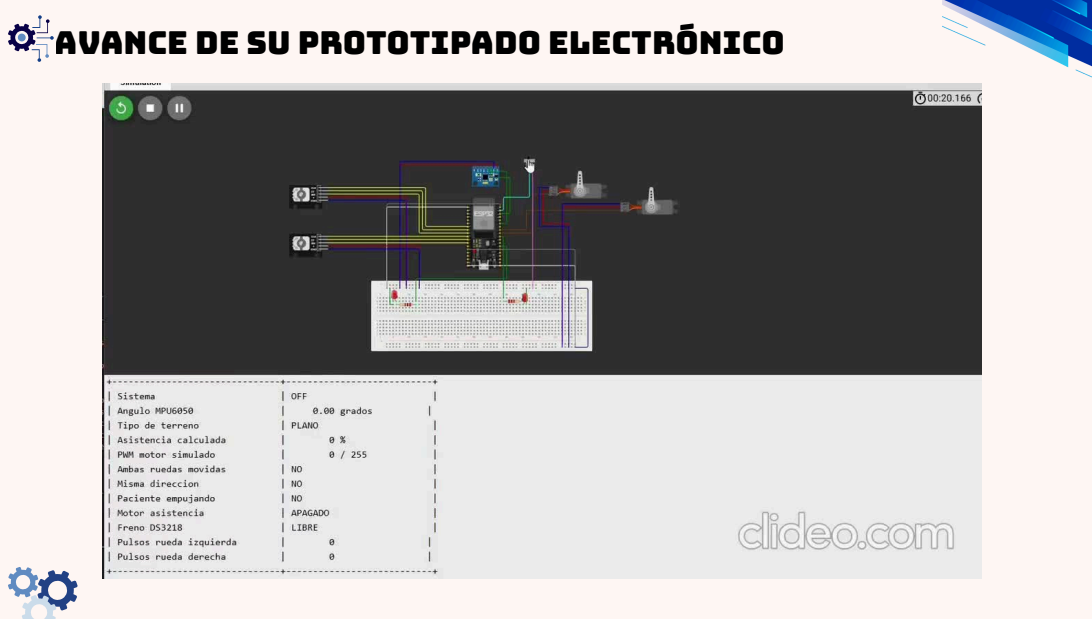
[picture p184: page 5]

# Modelado digital del prototipo completo

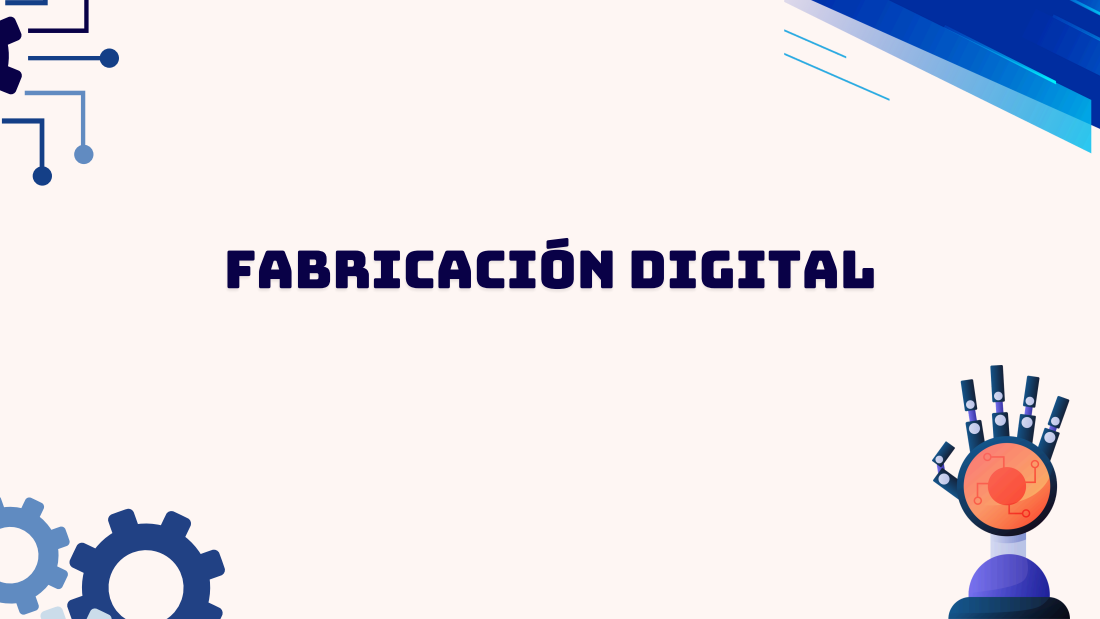
[picture p185: page 6]
Fabricación digital

# Modelado digital del prototipo completo

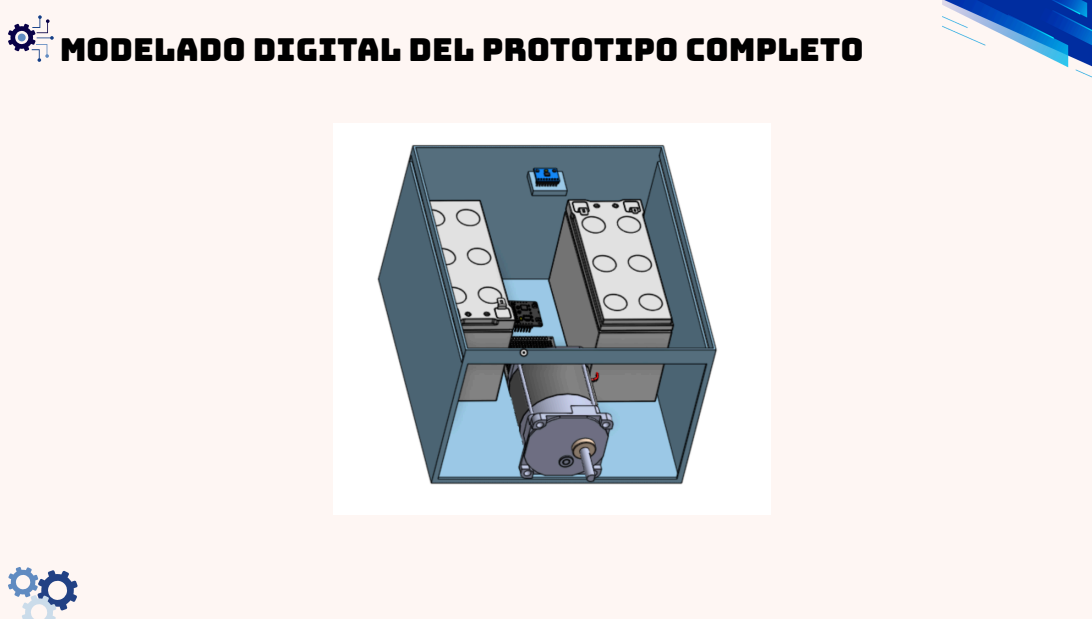
[picture p186: page 7]

# Archivos STL y planos de los modelos a imprimir

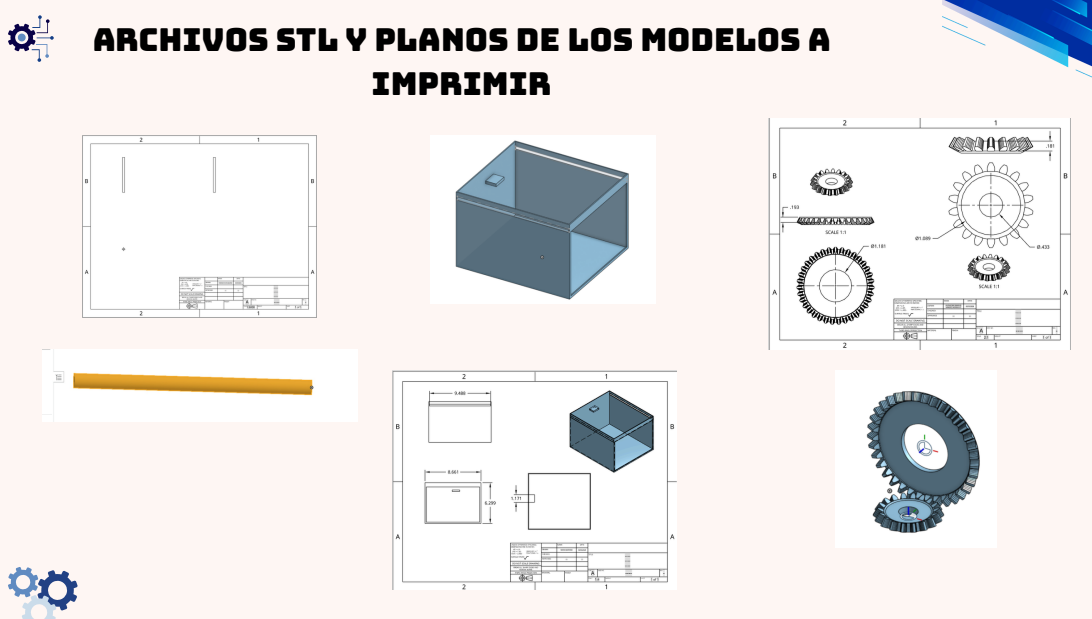
[picture p187: page 8]

# Plan de usabilidad basado en evidencias

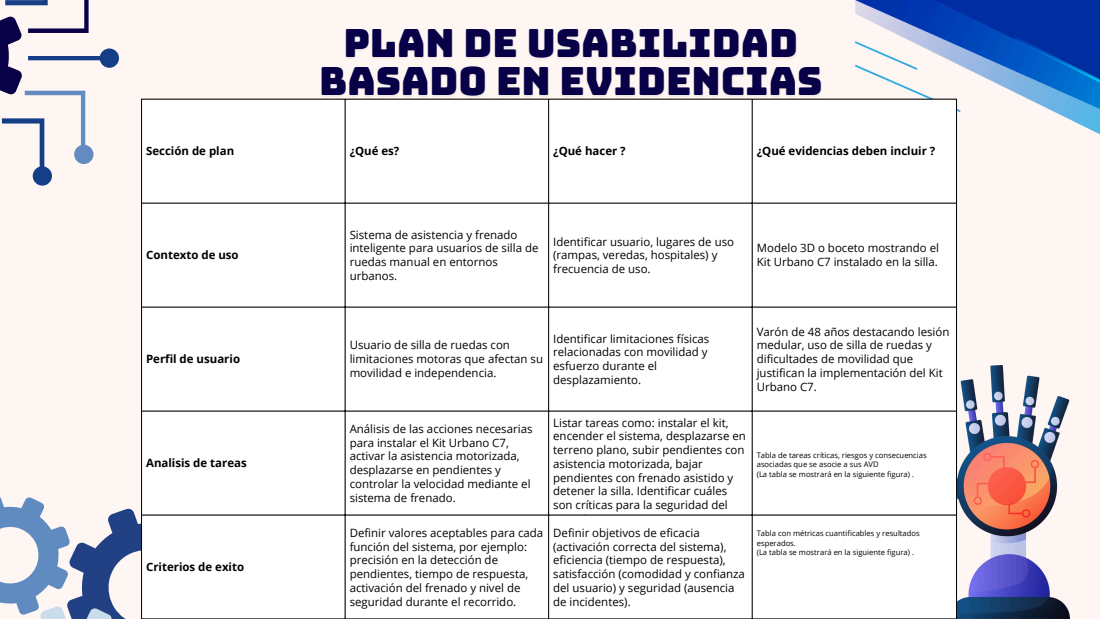
[picture p188: page 9]

Plan de usabilidad
basado en evidencias

Sección de plan | ¿Qué es? | ¿Qué hacer ? | ¿Qué evidencias deben incluir ?

Contexto de uso | Sistema de asistencia y frenado inteligente para usuarios de silla de ruedas manual en entornos urbanos. | Identificar usuario, lugares de uso (rampas, veredas, hospitales) y frecuencia de uso. | Modelo 3D o boceto mostrando el Kit Urbano C7 instalado en la silla.

Perfil de usuario | Usuario de silla de ruedas con limitaciones motoras que afectan su movilidad e independencia. | Identificar limitaciones físicas relacionadas con movilidad y esfuerzo durante el desplazamiento. | Varón de 48 años destacando lesión medular, uso de silla de ruedas y dificultades de movilidad que justifican la implementación del Kit Urbano C7.

Analisis de tareas | Análisis de las acciones necesarias para instalar el Kit Urbano C7, activar la asistencia motorizada, desplazarse en pendientes y controlar la velocidad mediante el sistema de frenado. | Listar tareas como: instalar el kit, encender el sistema, desplazarse en terreno plano, subir pendientes con asistencia motorizada, bajar pendientes con frenado asistido y detener la silla. Identificar cuáles son críticas para la seguridad del | Tabla de tareas críticas, riesgos y consecuencias asociadas que se asocie a sus AVD (La tabla se mostrará en la siguiente figura) .

Criterios de exito | Definir valores aceptables para cada función del sistema, por ejemplo: precisión en la detección de pendientes, tiempo de respuesta, activación del frenado y nivel de seguridad durante el recorrido. | Definir objetivos de eficacia (activación correcta del sistema), eficiencia (tiempo de respuesta), satisfacción (comodidad y confianza del usuario) y seguridad (ausencia de incidentes). | Tabla con métricas cuantificables y resultados esperados. (La tabla se mostrará en la siguiente figura) .

# Plan de usabilidad basado en evidencias

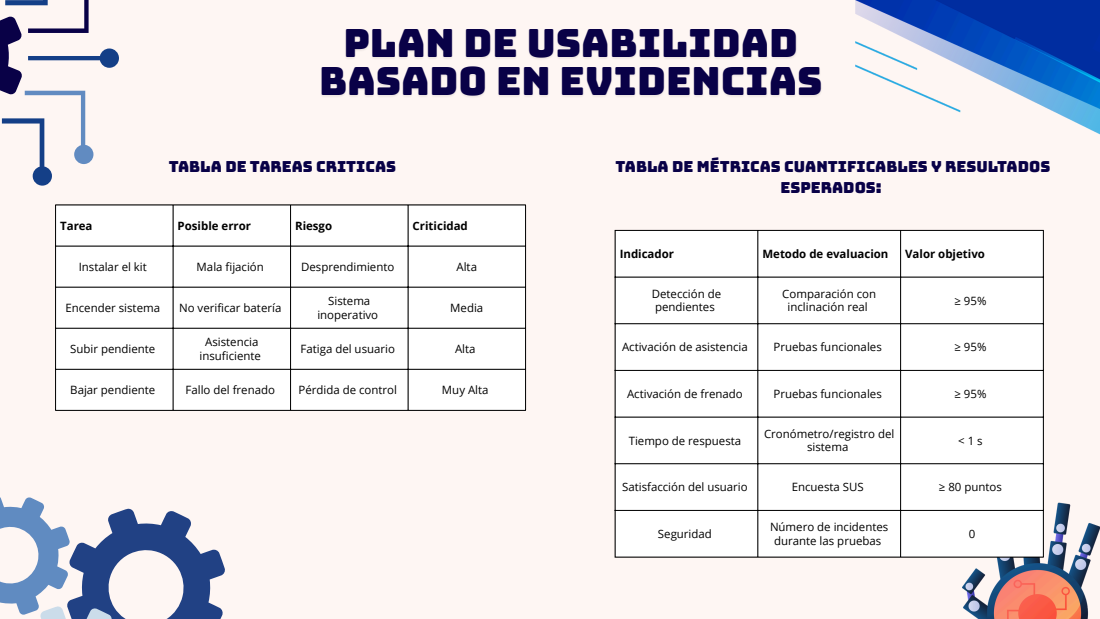
[picture p189: page 10]
Bajar pendiente; Fallo del frenado; Pérdida de control; Muy Alta; Activación de frenado; Pruebas funcionales; TABLA DE TAREAS CRITICAS; Tabla de métricas cuantificables y resultados; esperados:

Plan de usabilidad
basado en evidencias

Tarea | Posible error | Riesgo | Criticidad

Indicador | Metodo de evaluacion | Valor objetivo

Instalar el kit | Mala fijación | Desprendimiento | Alta

Detección de pendientes | Comparación con inclinación real | ≥ 95%

Encender sistema | No verificar batería | Sistema inoperativo | Media

Subir pendiente | Asistencia insuficiente | Fatiga del usuario | Alta

Activación de asistencia | Pruebas funcionales | ≥ 95%

Tiempo de respuesta | Cronómetro/registro del sistema | < 1 s

Satisfacción del usuario | Encuesta SUS | ≥ 80 puntos

Seguridad | Número de incidentes durante las pruebas | 0

GRACIAS
