Nadya-85/Grupo-3--FUNBIO/Documentación/Entregables/Entregable N°8/Esquema Electrónico.pdf

## SISTEMA DE FRENO FUENTE DE ENERGÍA

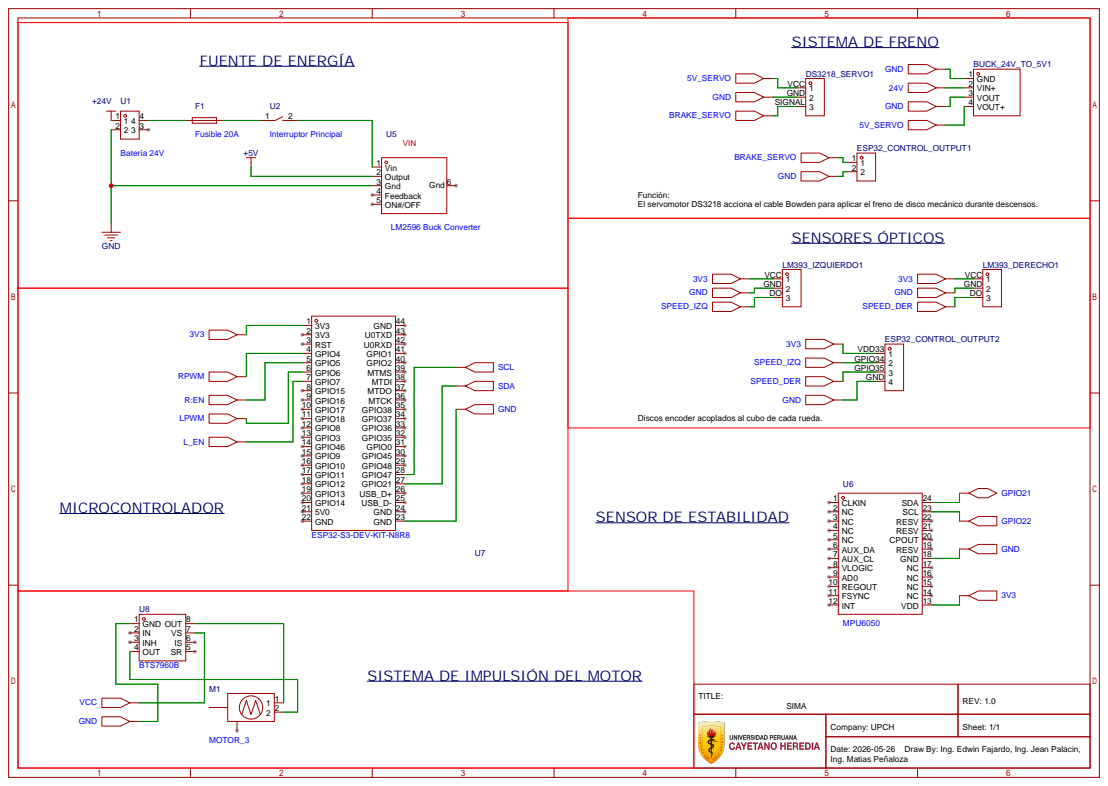
[picture p190: page 1]

Función:
El servomotor DS3218 acciona el cable Bowden para aplicar el freno de disco mecánico durante descensos.

Discos encoder acoplados al cubo de cada rueda.

SISTEMA DE IMPULSIÓN DEL MOTOR

TITLE: SIMA | REV: 1.0

Company: UPCH | Sheet: 1/1

Date: 2026-05-26 Draw By: Ing. Edwin Fajardo, Ing. Jean Palacin,
Ing. Matias Peñaloza
