Nadya-85/Grupo-3--FUNBIO/Documentación/Hitos/Presentaciones/PPT Hito N°1.pdf

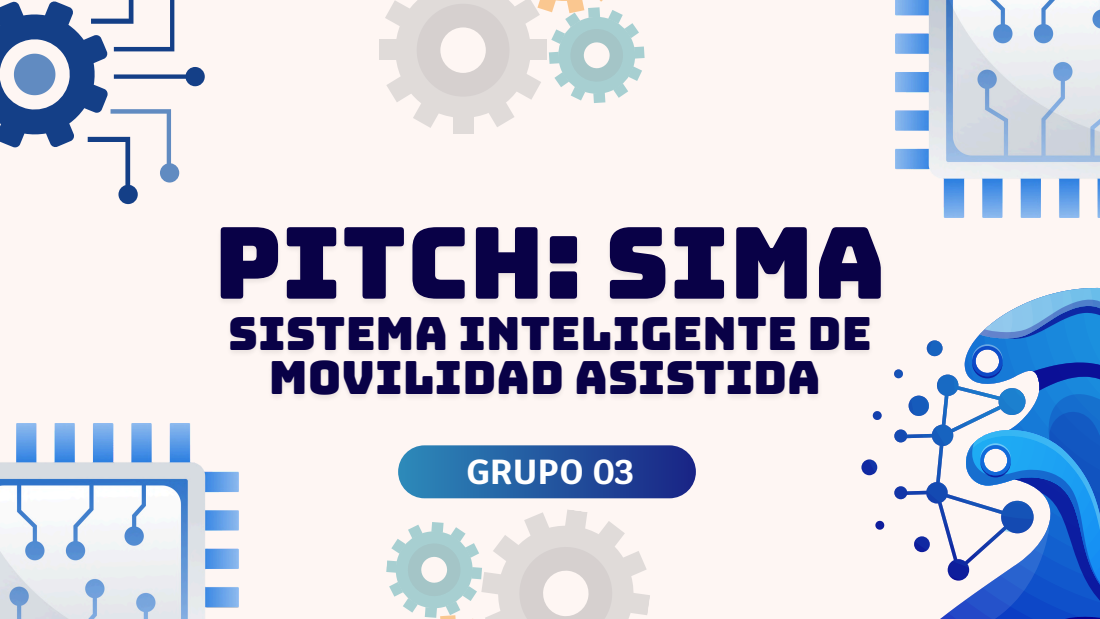
[picture p191: page 1]
GRUPO 03; Pitch: SIMA

Sistema Inteligente de
Movilidad Asistida

# Integrantes y roles

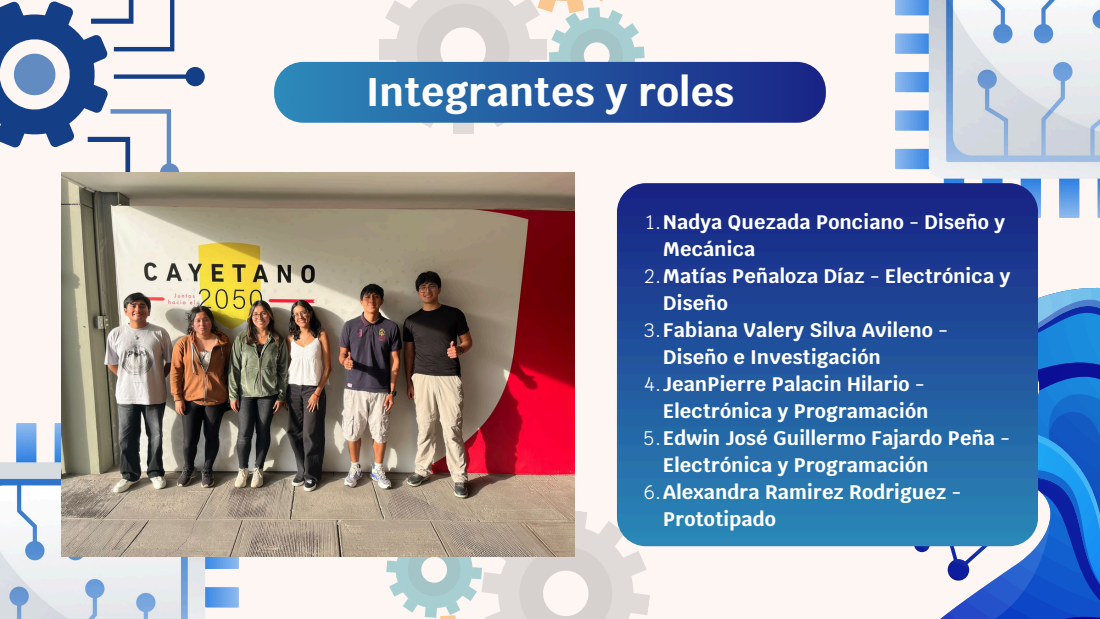
[picture p192: page 2]

1.Nadya Quezada Ponciano - Diseño y
Mecánica
2.Matías Peñaloza Díaz - Electrónica y
Diseño
3.Fabiana Valery Silva Avileno -
Diseño e Investigación
4.JeanPierre Palacin Hilario -
Electrónica y Programación
5.Edwin José Guillermo Fajardo Peña -
6.Alexandra Ramirez Rodriguez -
Prototipado

# Análisis del Caso

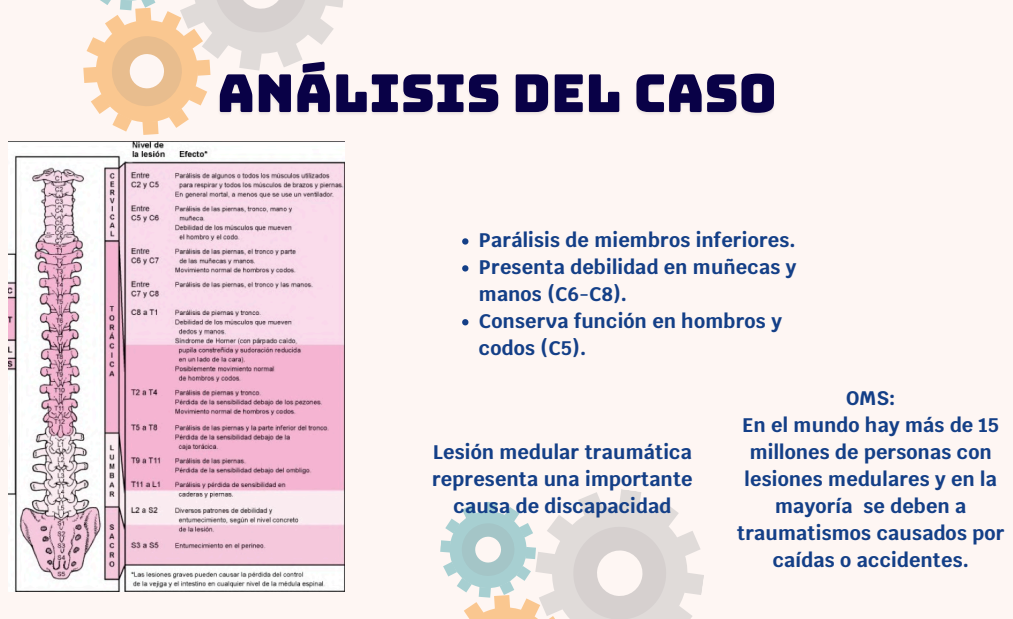
[picture p193: page 3]
OMS:

Parálisis de miembros inferiores.
Presenta debilidad en muñecas y
manos (C6-C8).
Conserva función en hombros y
codos (C5).

En el mundo hay más de 15
millones de personas con
lesiones medulares y en la
mayoría se deben a
traumatismos causados por
caídas o accidentes.

Lesión medular traumática
representa una importante
causa de discapacidad

# Análisis del Caso

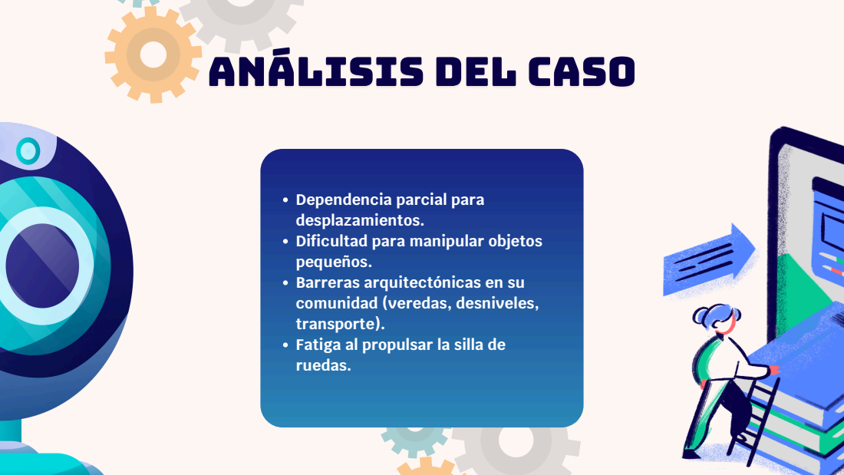
[picture p194: page 4]

Dependencia parcial para
desplazamientos.
Dificultad para manipular objetos
pequeños.
Barreras arquitectónicas en su
comunidad (veredas, desniveles,
transporte).
Fatiga al propulsar la silla de
ruedas.

# Análisis del Caso

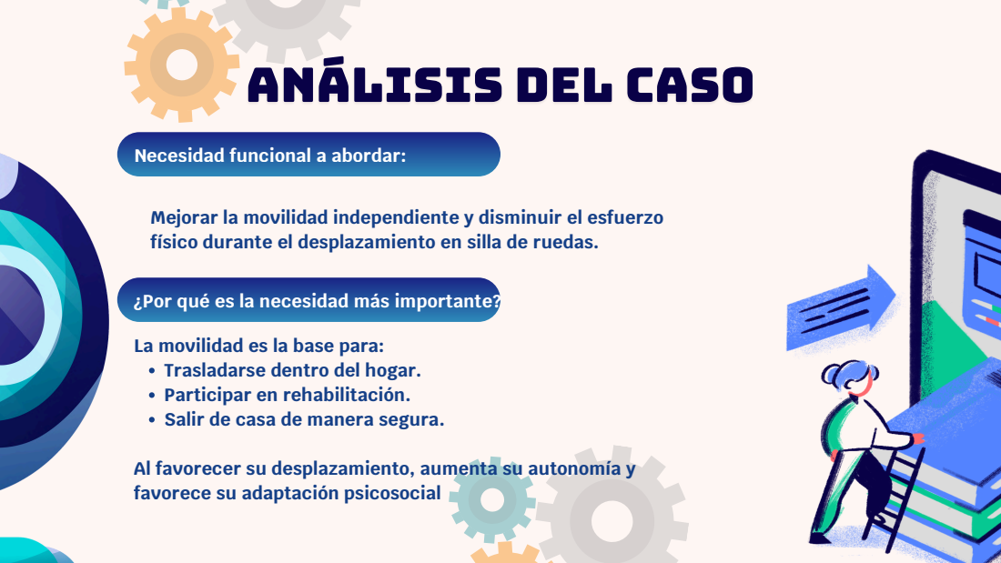
[picture p195: page 5]

Necesidad funcional a abordar:

Mejorar la movilidad independiente y disminuir el esfuerzo
físico durante el desplazamiento en silla de ruedas.

¿Por qué es la necesidad más importante?

La movilidad es la base para:
Trasladarse dentro del hogar.
Participar en rehabilitación.
Salir de casa de manera segura.

Al favorecer su desplazamiento, aumenta su autonomía y
favorece su adaptación psicosocial

# Estado del Arte ⁻ Patentes

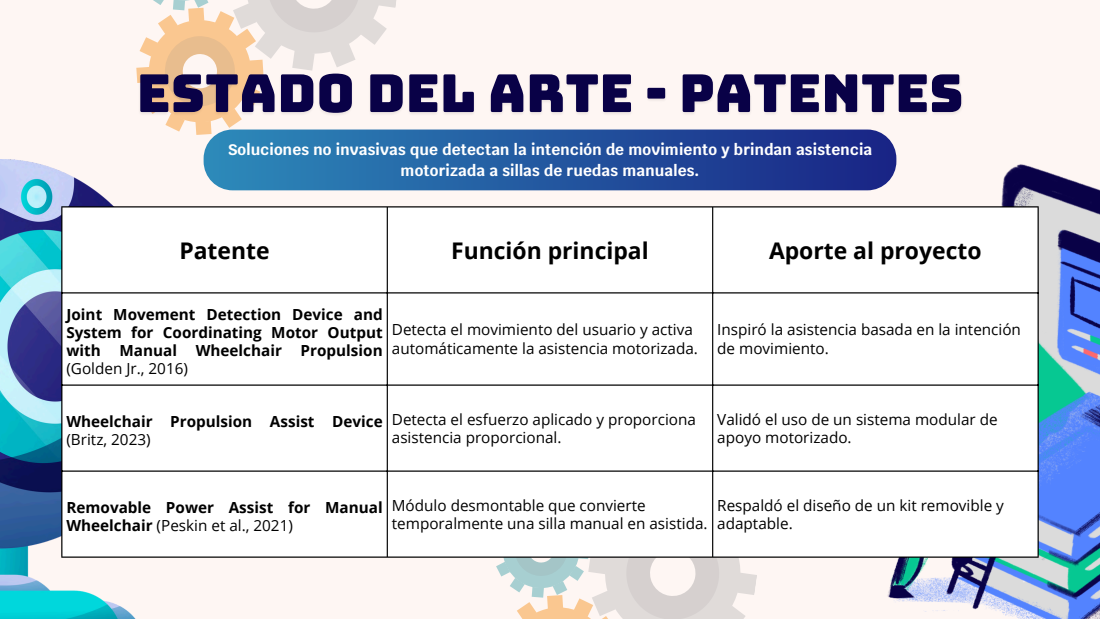
[picture p196: page 6]

Soluciones no invasivas que detectan la intención de movimiento y brindan asistencia

motorizada a sillas de ruedas manuales.

Patente | Función principal | Aporte al proyecto

Joint Movement Detection Device and System for Coordinating Motor Output with Manual Wheelchair Propulsion (Golden Jr., 2016) | Detecta el movimiento del usuario y activa automáticamente la asistencia motorizada. | Inspiró la asistencia basada en la intención de movimiento.

Wheelchair Propulsion Assist Device (Britz, 2023) | Detecta el esfuerzo aplicado y proporciona asistencia proporcional. | Validó el uso de un sistema modular de apoyo motorizado.

Removable Power Assist for Manual Wheelchair (Peskin et al., 2021) | Módulo desmontable que convierte temporalmente una silla manual en asistida. | Respaldó el diseño de un kit removible y adaptable.

# Estado del Arte ⁻ Productos

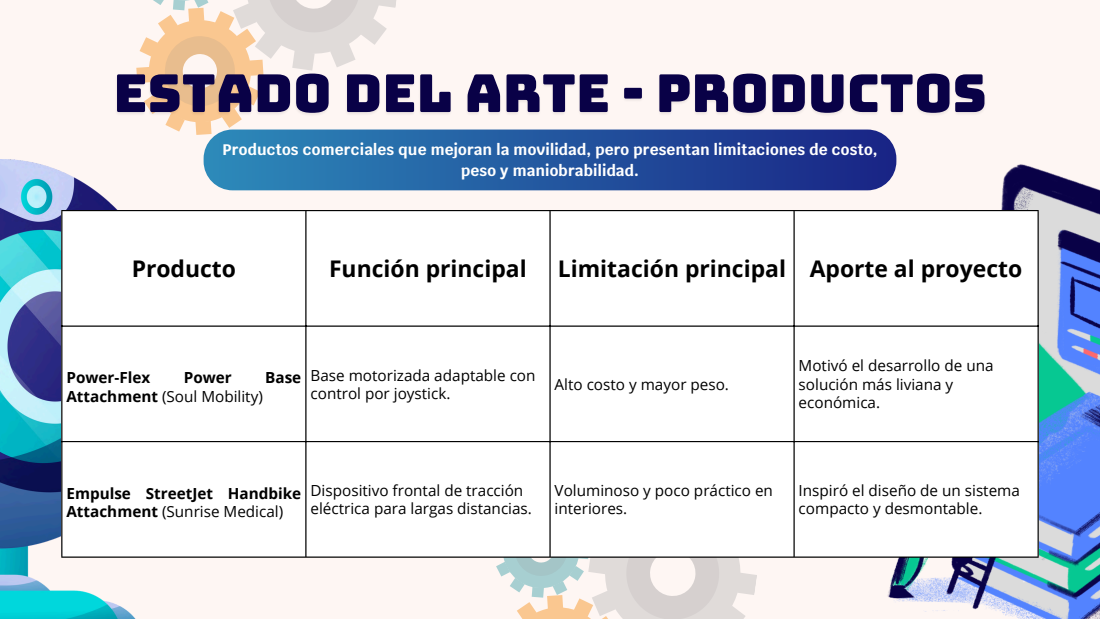
[picture p197: page 7]
peso y maniobrabilidad.

Productos comerciales que mejoran la movilidad, pero presentan limitaciones de costo,

Producto | Función principal | Limitación principal | Aporte al proyecto

Power-Flex Power Base Attachment (Soul Mobility) | Base motorizada adaptable con control por joystick. | Alto costo y mayor peso. | Motivó el desarrollo de una solución más liviana y económica.

Empulse StreetJet Handbike Attachment (Sunrise Medical) | Dispositivo frontal de tracción eléctrica para largas distancias. | Voluminoso y poco práctico en interiores. | Inspiró el diseño de un sistema compacto y desmontable.

# DESCRIPCIÓN

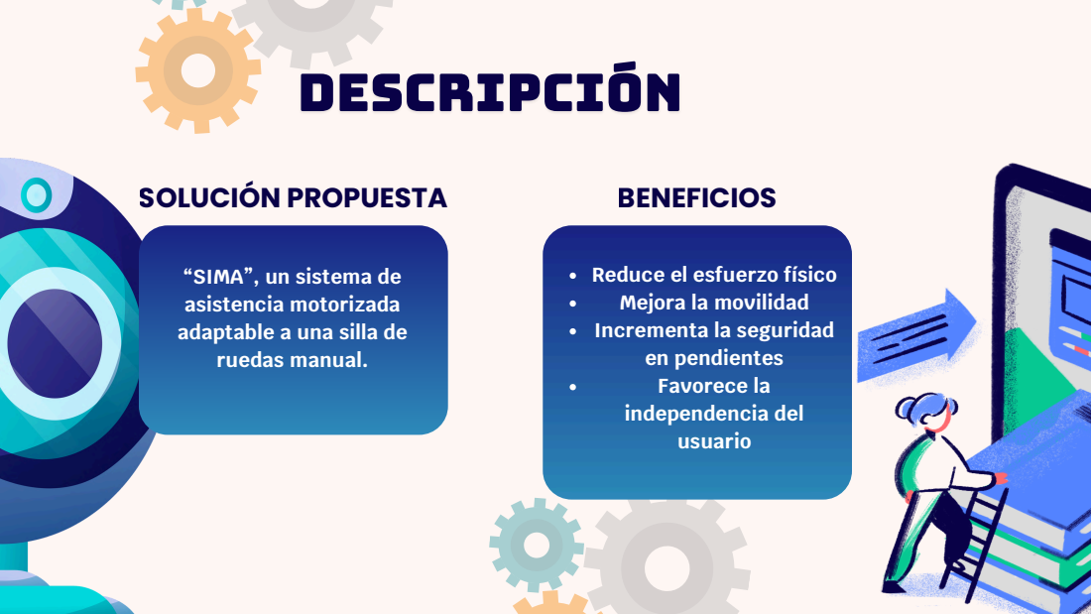
[picture p198: page 8]
SOLUCIÓN PROPUESTA; BENEFICIOS

“SIMA”
asistencia motorizada
adaptable a una silla de
ruedas manual.

, un sistema de

Reduce el esfuerzo físico
Mejora la movilidad
Incrementa la seguridad
en pendientes
Favorece la
independencia del
usuario

# Requerimientos funcionales

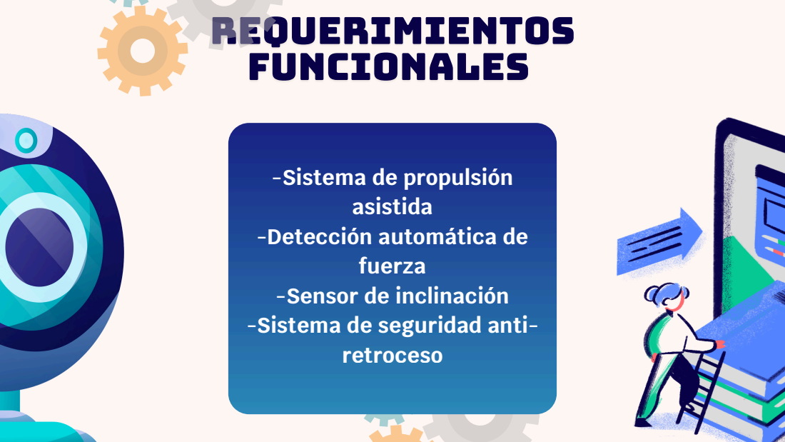
[picture p199: page 9]
Requerimientos funcionales; fuerza; retroceso

-Sistema de propulsión
asistida

-Detección automática de

-Sensor de inclinación
-Sistema de seguridad anti-

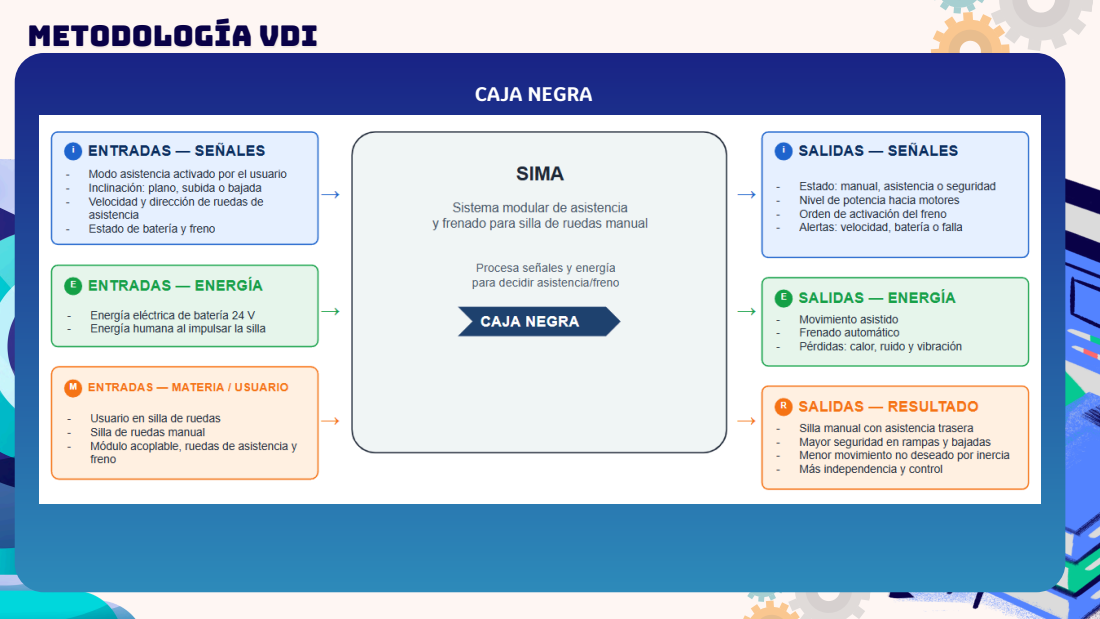
[picture p200: page 10]
Metodología VDI; CAJA NEGRA

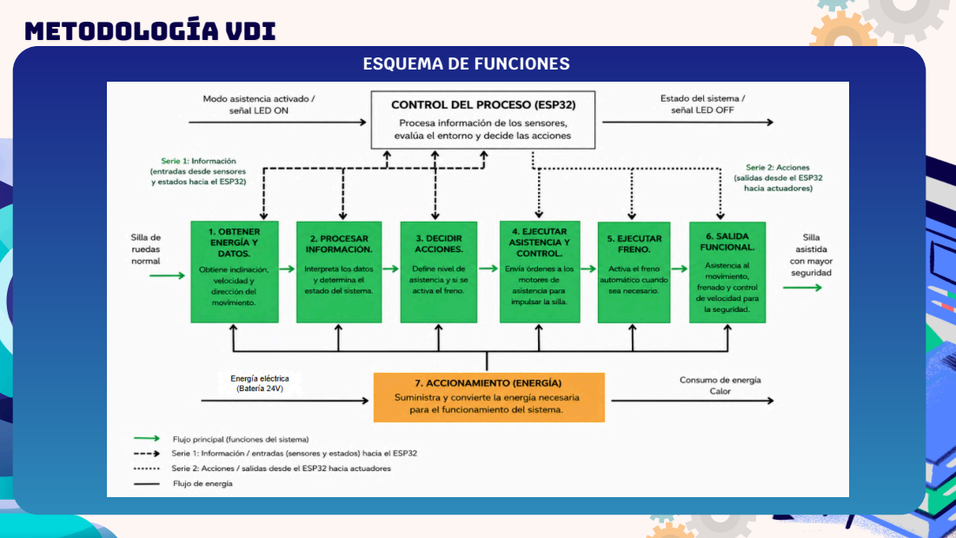
[picture p201: page 11]
Metodología VDI

ESQUEMA DE FUNCIONES

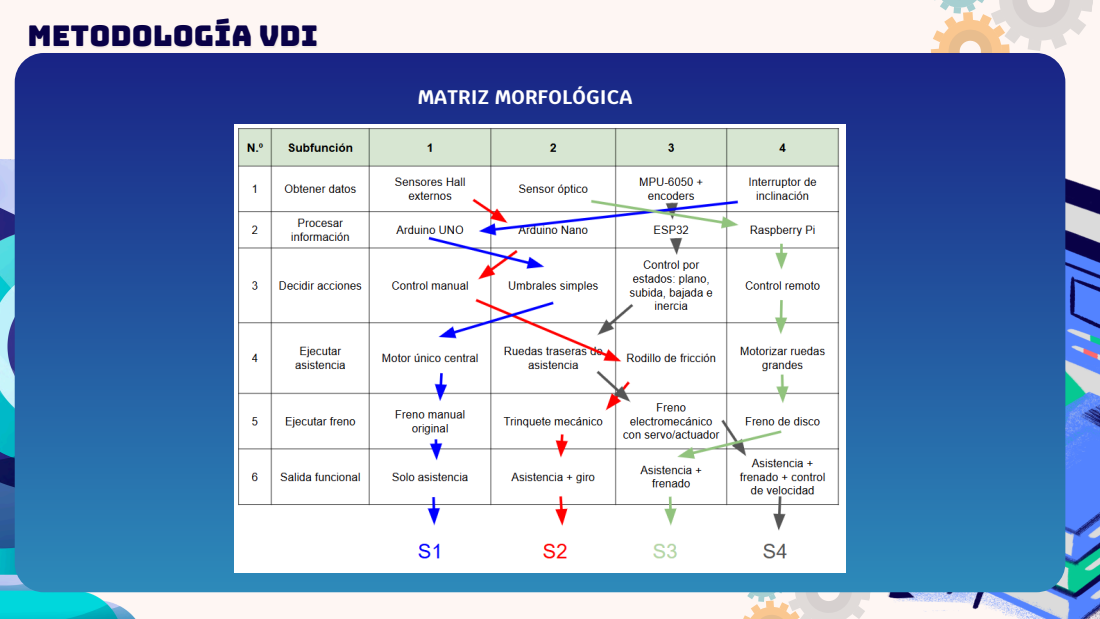
[picture p202: page 12]
Metodología VDI; MATRIZ MORFOLÓGICA

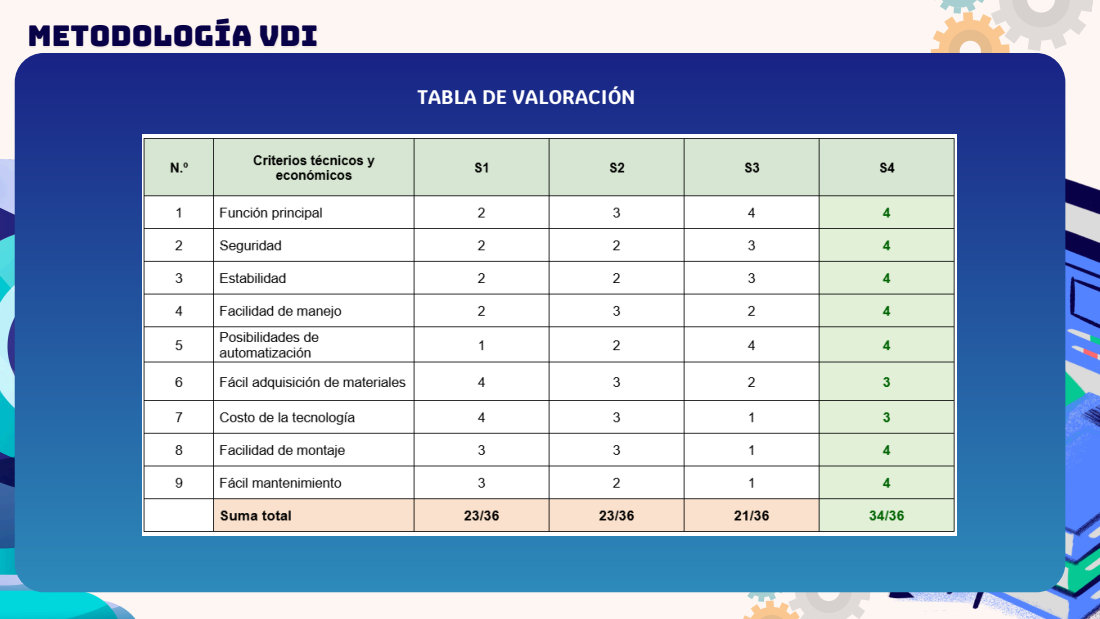
[picture p203: page 13]
Metodología VDI

TABLA DE VALORACIÓN

# Metodología VDI

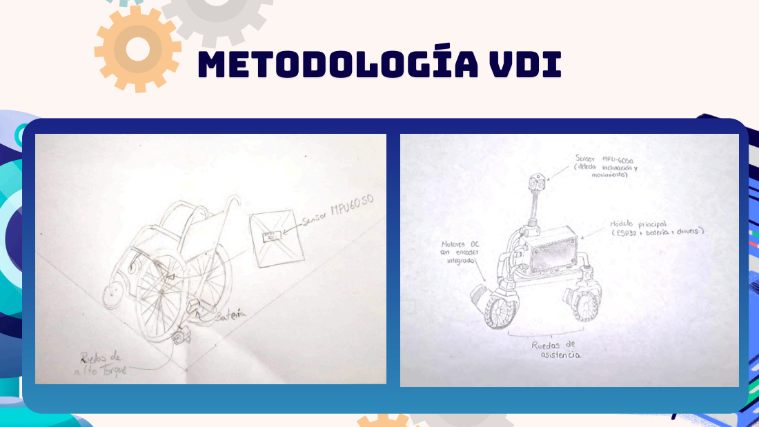
[picture p204: page 14]

# Conclusiones/siguientes pasos

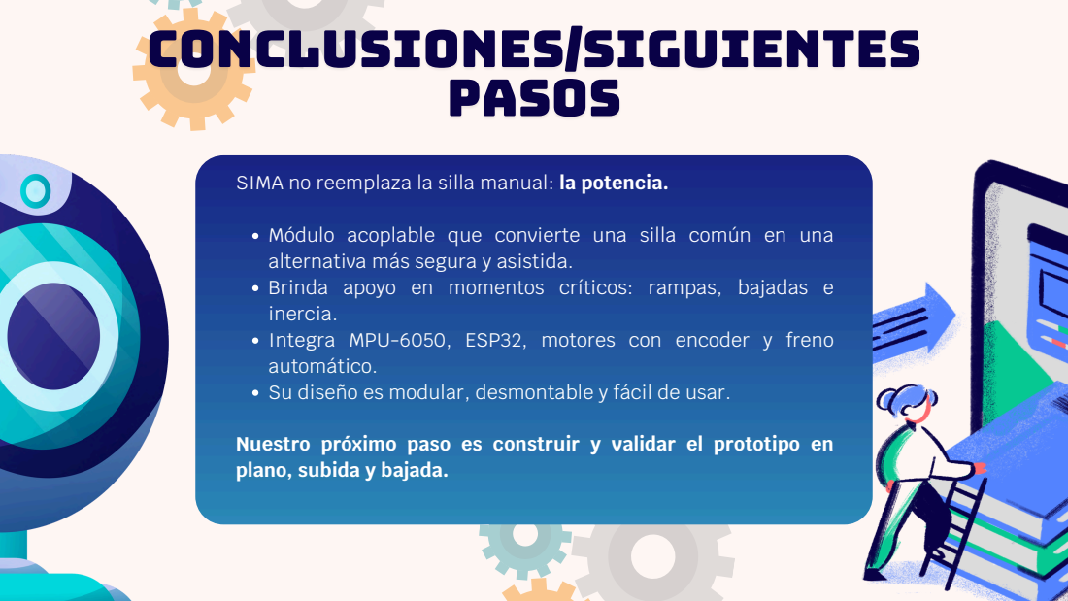
[picture p205: page 15]
Conclusiones/siguientes pasos

SIMA no reemplaza la silla manual: la potencia.

Módulo acoplable que convierte una silla común en una
alternativa más segura y asistida.
Brinda apoyo en momentos críticos: rampas, bajadas e
inercia.
Integra MPU-6050, ESP32, motores con encoder y freno
automático.
Su diseño es modular, desmontable y fácil de usar.

Nuestro próximo paso es construir y validar el prototipo en
plano, subida y bajada.

# Referencias

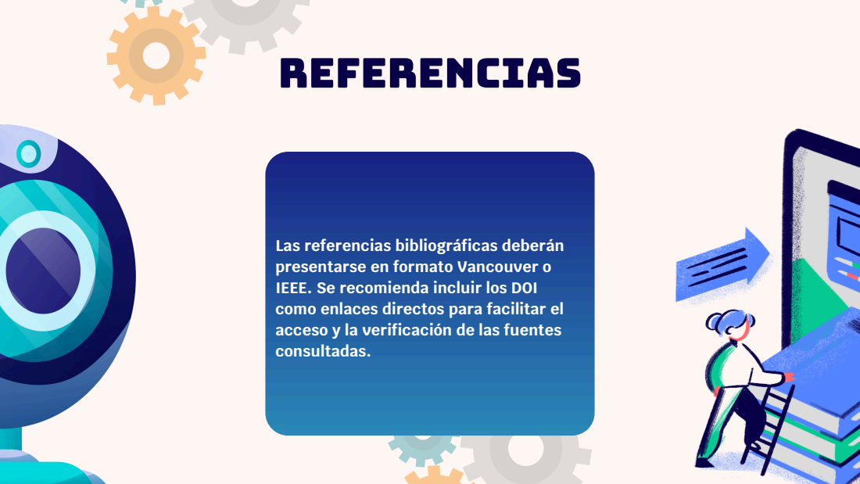
[picture p206: page 16]

Las referencias bibliográficas deberán
presentarse en formato Vancouver o
IEEE. Se recomienda incluir los DOI
como enlaces directos para facilitar el
acceso y la verificación de las fuentes
consultadas.

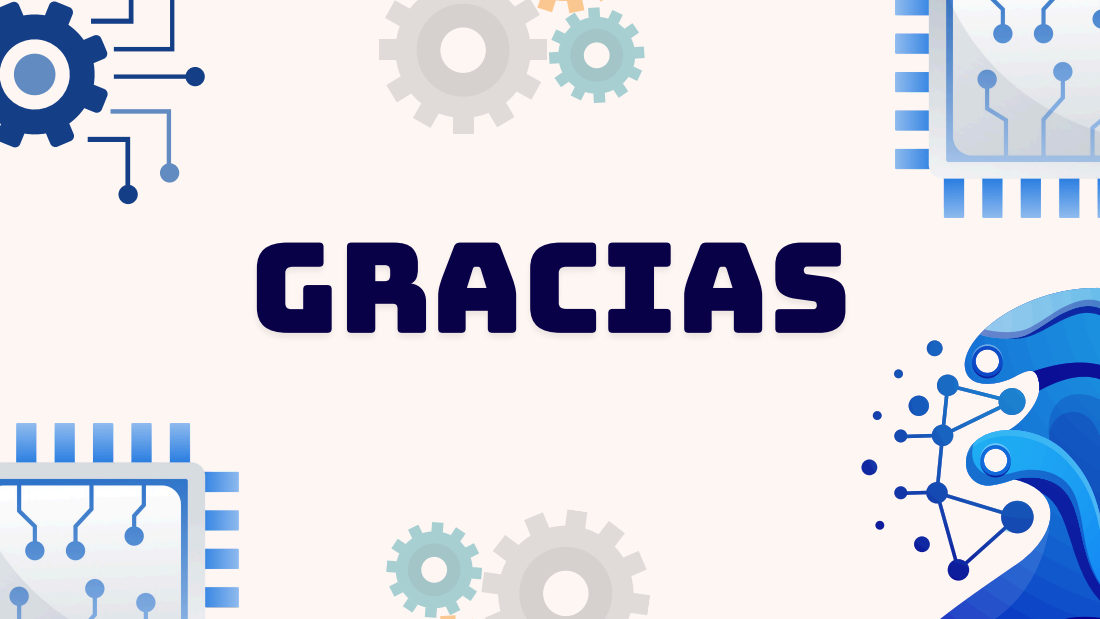
[picture p207: page 17]
GRACIAS
