Nadya-85/Grupo-3--FUNBIO/Documentación/Entregables/Presentaciones/PPT Entregable N°7.pdf

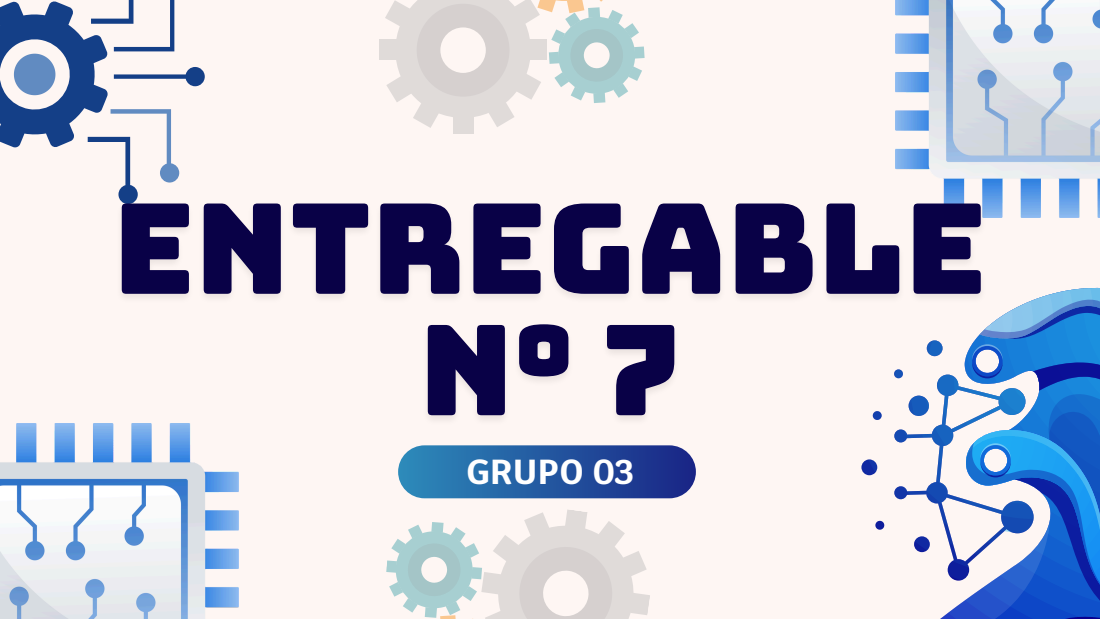
[picture p208: page 1]
GRUPO 03; ENTREGABLE N° 7

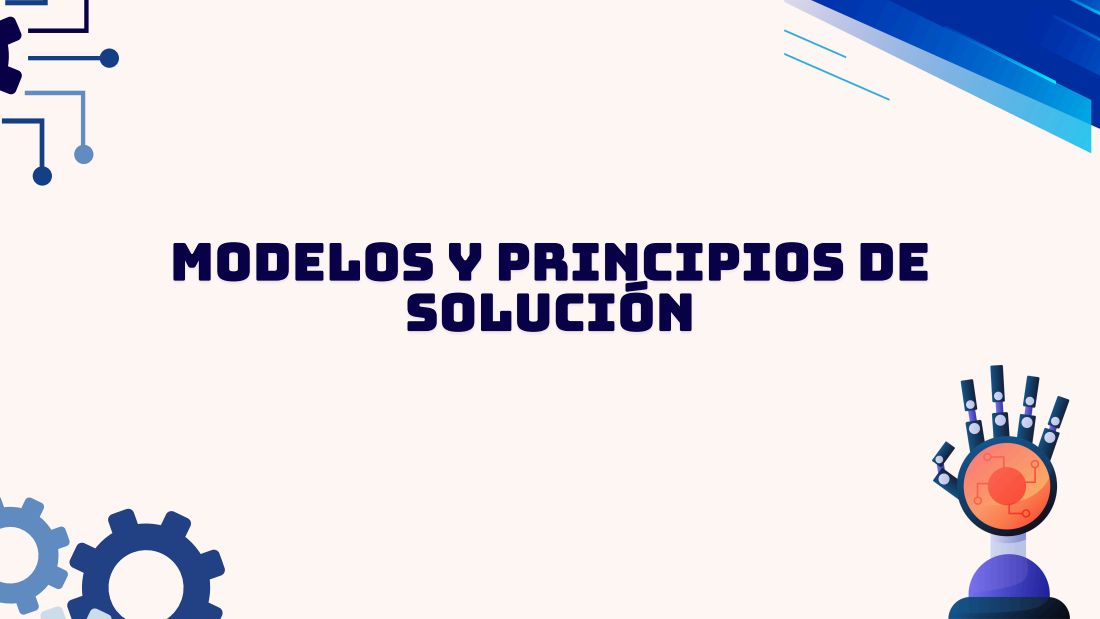
[picture p209: page 2]
solución

Modelos y principios de

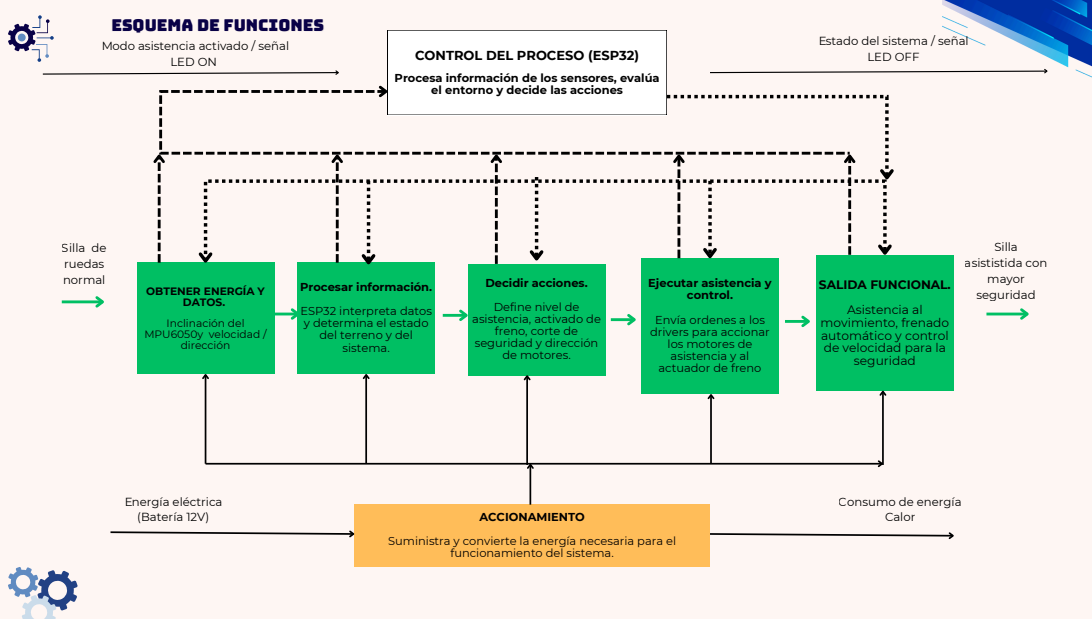
[picture p210: page 3]
OBTENER ENERGÍA Y DATOS.; Inclinación del MPU6050y velocidad / dirección; ACCIONAMIENTO; LED ON; LED OFF; Calor; Energía eléctrica (Batería 12V); Silla de ruedas normal; Silla asististida con mayor seguridad

esquema de funciones
Modo asistencia activado / señal

Estado del sistema / señal

CONTROL DEL PROCESO (ESP32)
Procesa información de los sensores, evalúa
el entorno y decide las acciones

Decidir acciones.
Define nivel de
asistencia, activado de
freno, corte de
seguridad y dirección
de motores.

Ejecutar asistencia y
control.
Envía ordenes a los
drivers para accionar
los motores de
asistencia y al
actuador de freno

SALIDA FUNCIONAL.
Asistencia al
movimiento, frenado
automático y control
de velocidad para la
seguridad

Procesar información.
ESP32 interpreta datos
y determina el estado
del terreno y del
sistema.

Consumo de energía

Suministra y convierte la energía necesaria para el

funcionamiento del sistema.

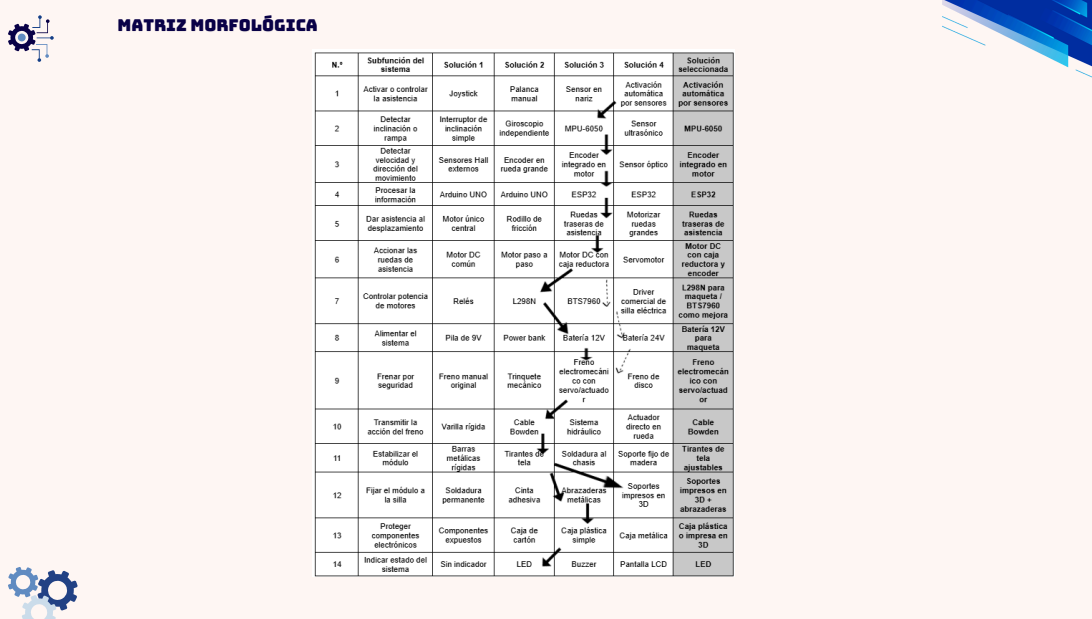
[picture p211: page 4]
MATRIZ MORFOLÓGICA

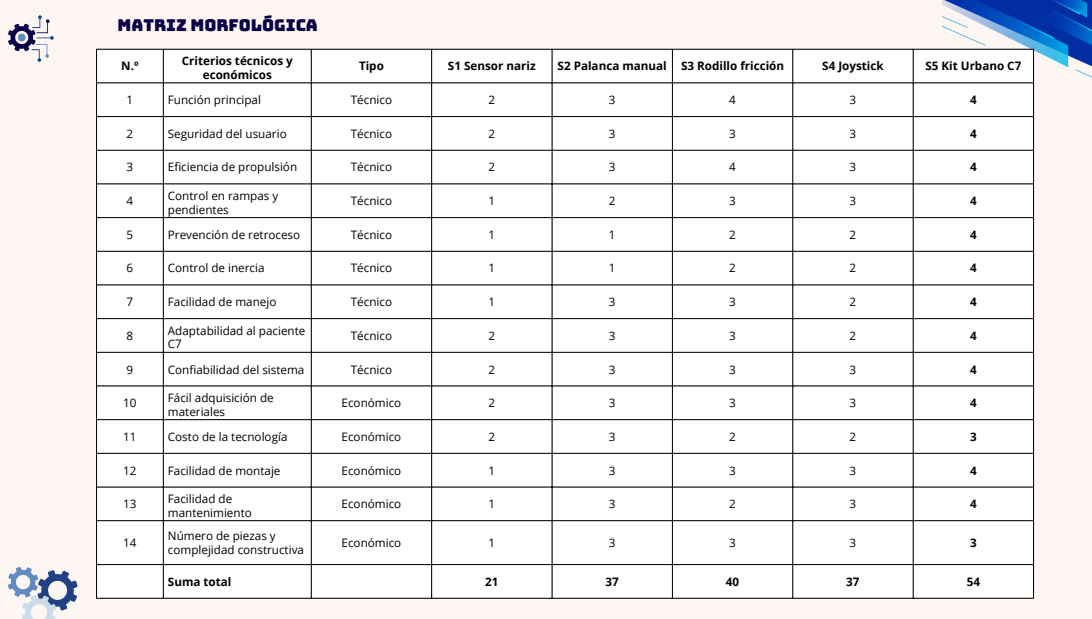
[picture p212: page 5]
MATRIZ MORFOLÓGICA

N.º | Criterios técnicos y económicos | Tipo | S1 Sensor nariz | S2 Palanca manual | S3 Rodillo fricción | S4 Joystick | S5 Kit Urbano C7

1 | Función principal | Técnico | 2 | 3 | 4 | 3 | 4

2 | Seguridad del usuario | Técnico | 2 | 3 | 3 | 3 | 4

3 | Eficiencia de propulsión | Técnico | 2 | 3 | 4 | 3 | 4
4 | Control en rampas y pendientes | Técnico | 1 | 2 | 3 | 3 | 4

5 | Prevención de retroceso | Técnico | 1 | 1 | 2 | 2 | 4

6 | Control de inercia | Técnico | 1 | 1 | 2 | 2 | 4

7 | Facilidad de manejo | Técnico | 1 | 3 | 3 | 2 | 4
8 | Adaptabilidad al paciente C7 | Técnico | 2 | 3 | 3 | 2 | 4

9 | Confiabilidad del sistema | Técnico | 2 | 3 | 3 | 3 | 4
10 | Fácil adquisición de materiales | Económico | 2 | 3 | 3 | 3 | 4

11 | Costo de la tecnología | Económico | 2 | 3 | 2 | 2 | 3

12 | Facilidad de montaje | Económico | 1 | 3 | 3 | 3 | 4
13 | Facilidad de mantenimiento | Económico | 1 | 3 | 2 | 3 | 4

14 | Número de piezas y complejidad constructiva | Económico | 1 | 3 | 3 | 3 | 3

Suma total | | 21 | 37 | 40 | 37 | 54

# Espacio de solución

## BOCETOS 1 Y 2 (VISTA LATERAL Y

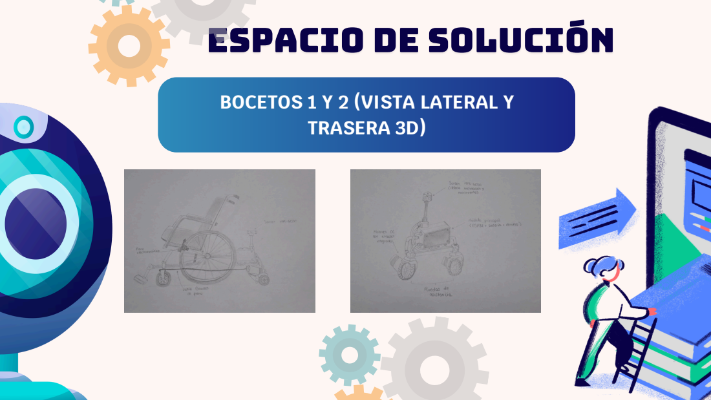
[picture p213: page 6]
TRASERA 3D)

# Espacio de solución

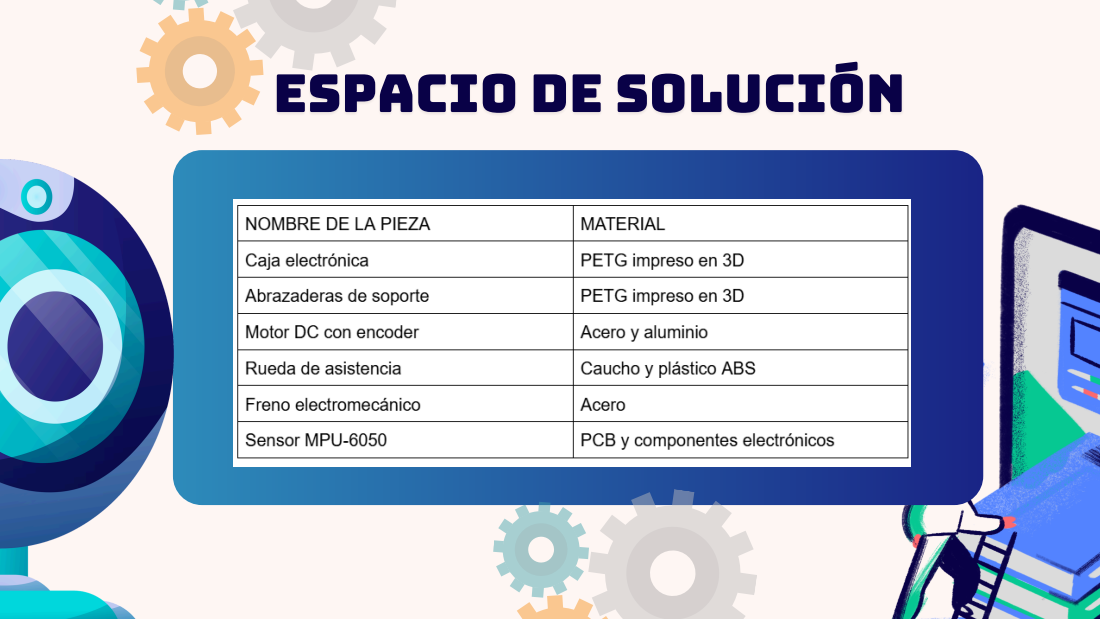
[picture p214: page 7]

# ¿Fabricar o adquirir?

FABRICAR | ADQUIRIR

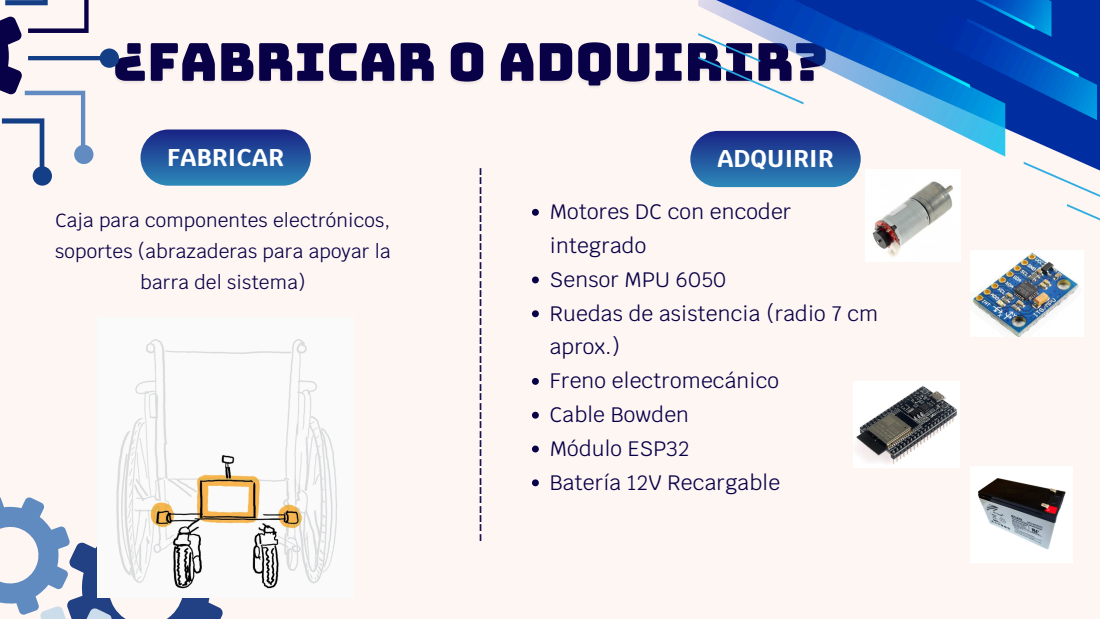
[picture p215: page 8]
Módulo ESP32 Batería 12V Recargable

Motores DC con encoder
integrado
Sensor MPU 6050
Ruedas de asistencia (radio 7 cm
aprox.)
Freno electromecánico
Cable Bowden

Caja para componentes electrónicos,
soportes (abrazaderas para apoyar la

barra del sistema)

# Secuencia de procesos

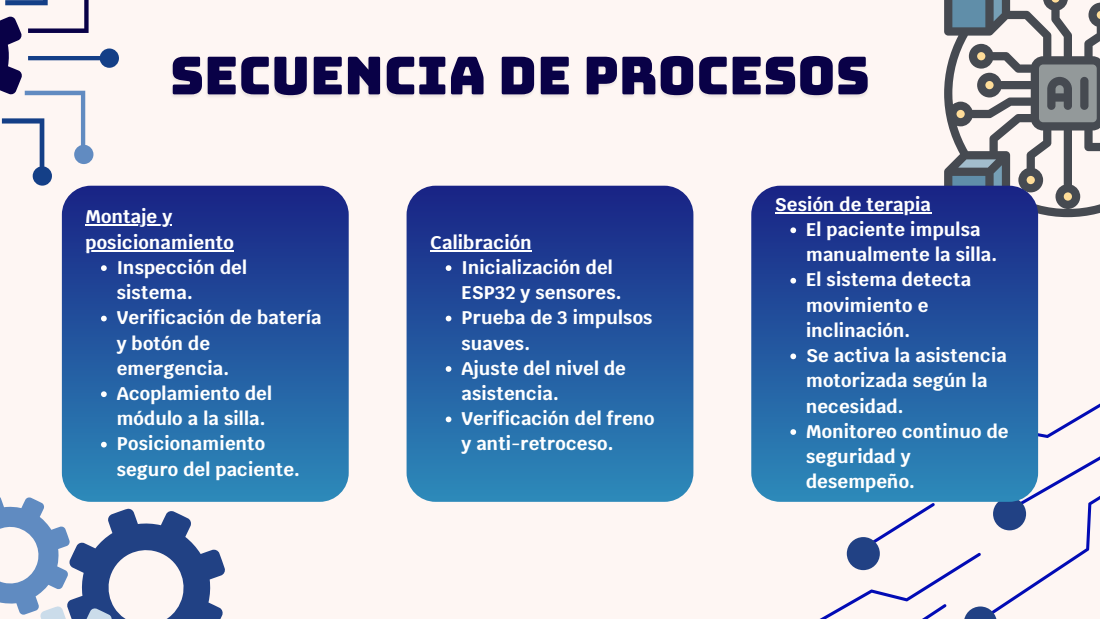
[picture p216: page 9]

Sesión de terapia
El paciente impulsa
manualmente la silla.
El sistema detecta
movimiento e
inclinación.
Se activa la asistencia
motorizada según la
necesidad.
Monitoreo continuo de
seguridad y
desempeño.

Montaje y
posicionamiento
Inspección del
sistema.
Verificación de batería
y botón de
emergencia.
Acoplamiento del
módulo a la silla.
Posicionamiento
seguro del paciente.

Calibración
Inicialización del
ESP32 y sensores.
Prueba de 3 impulsos
suaves.
Ajuste del nivel de
asistencia.
Verificación del freno
y anti-retroceso.

# Secuencia de procesos

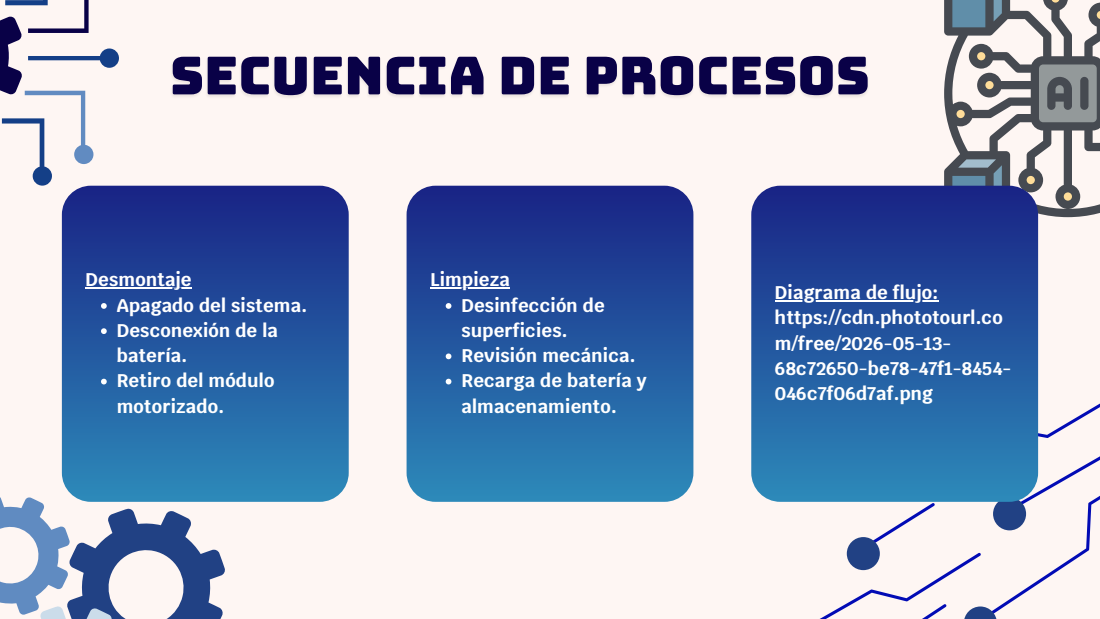
[picture p217: page 10]

Desmontaje
Apagado del sistema.
Desconexión de la
batería.
Retiro del módulo
motorizado.

Limpieza
Desinfección de
superficies.
Revisión mecánica.
Recarga de batería y
almacenamiento.

Diagrama de flujo:
https://cdn.phototourl.co
m/free/2026-05-13-
046c7f06d7af.png

## Impresión 3D con Filamento PETG

# Técnicas de producción

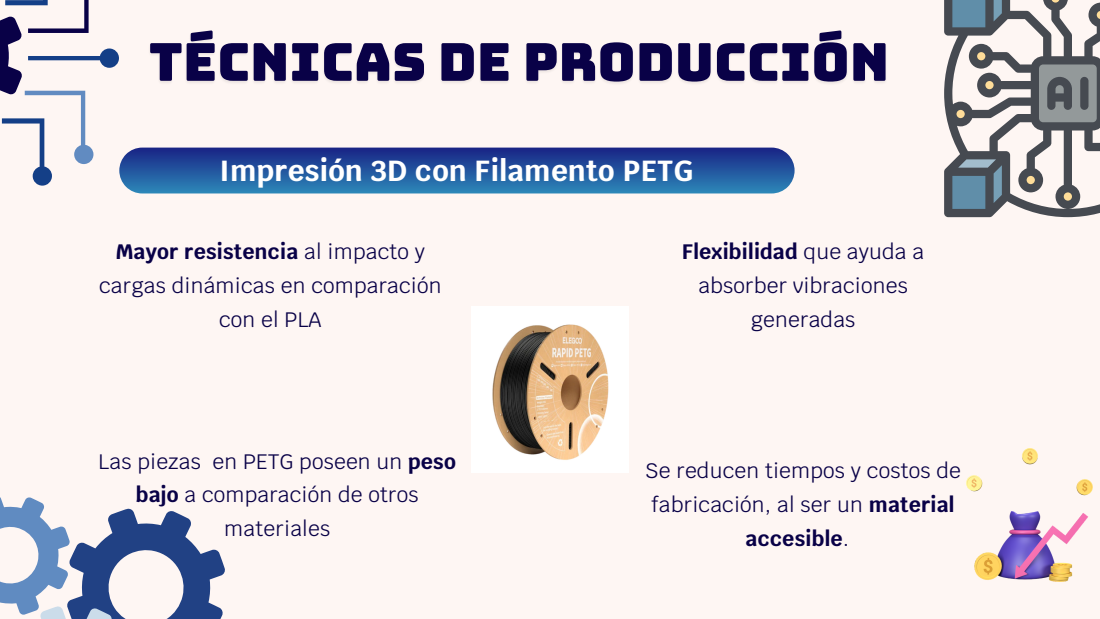
[picture p218: page 11]
materiales; accesible.

Mayor resistencia al impacto y
cargas dinámicas en comparación

Flexibilidad que ayuda a
absorber vibraciones
generadas

con el PLA

Las piezas en PETG poseen un peso
bajo a comparación de otros

Se reducen tiempos y costos de
fabricación, al ser un material

# Estaciones de trabajo

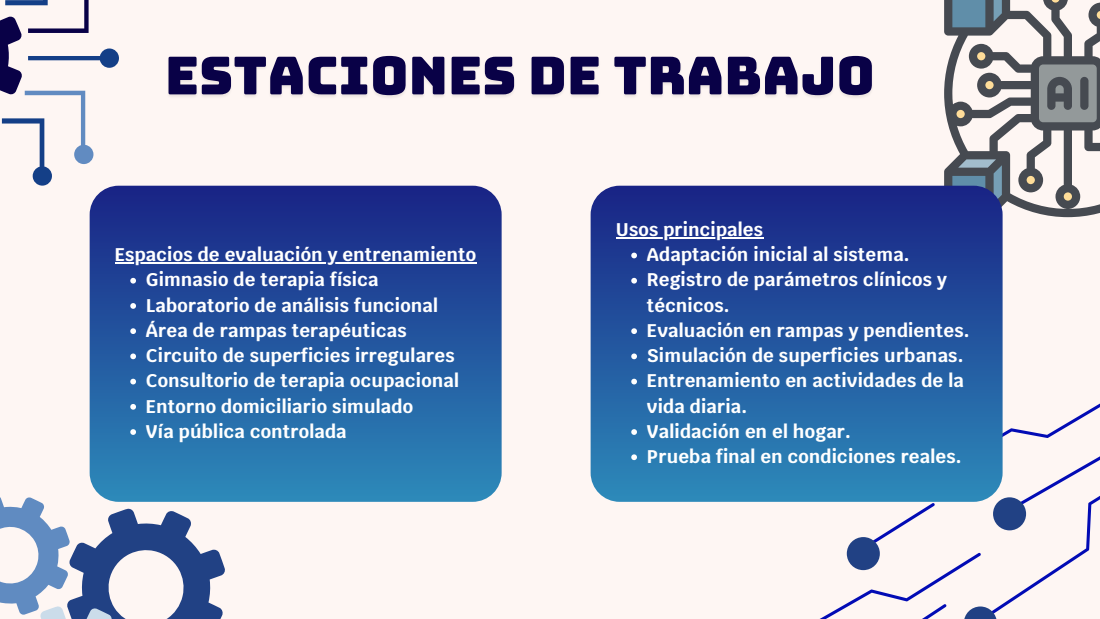
[picture p219: page 12]

Usos principales
Adaptación inicial al sistema.
Registro de parámetros clínicos y
técnicos.
Evaluación en rampas y pendientes.
Simulación de superficies urbanas.
Entrenamiento en actividades de la
vida diaria.
Validación en el hogar.
Prueba final en condiciones reales.

Espacios de evaluación y entrenamiento
Gimnasio de terapia física
Laboratorio de análisis funcional
Área de rampas terapéuticas
Circuito de superficies irregulares
Consultorio de terapia ocupacional
Entorno domiciliario simulado
Vía pública controlada

# Estaciones de trabajo

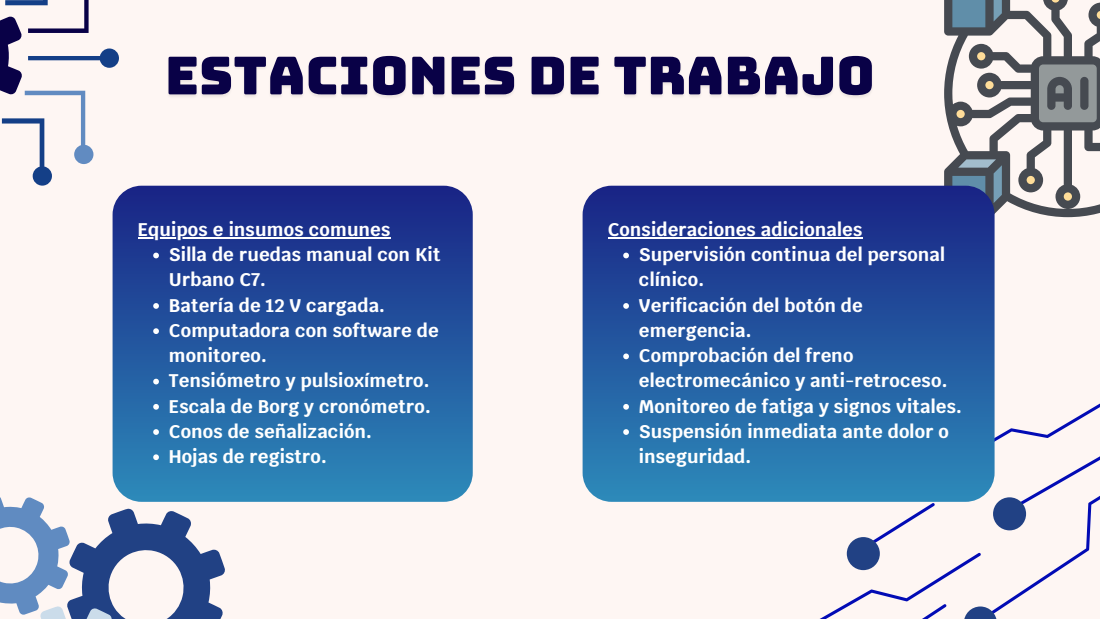
[picture p220: page 13]

Equipos e insumos comunes
Silla de ruedas manual con Kit
Urbano C7.
Batería de 12 V cargada.
Computadora con software de
monitoreo.
Tensiómetro y pulsioxímetro.
Escala de Borg y cronómetro.
Conos de señalización.
Hojas de registro.

Consideraciones adicionales
Supervisión continua del personal
clínico.
Verificación del botón de
emergencia.
Comprobación del freno
electromecánico y anti-retroceso.
Monitoreo de fatiga y signos vitales.
Suspensión inmediata ante dolor o
inseguridad.

# Automatización del Sistema Semiautónomo

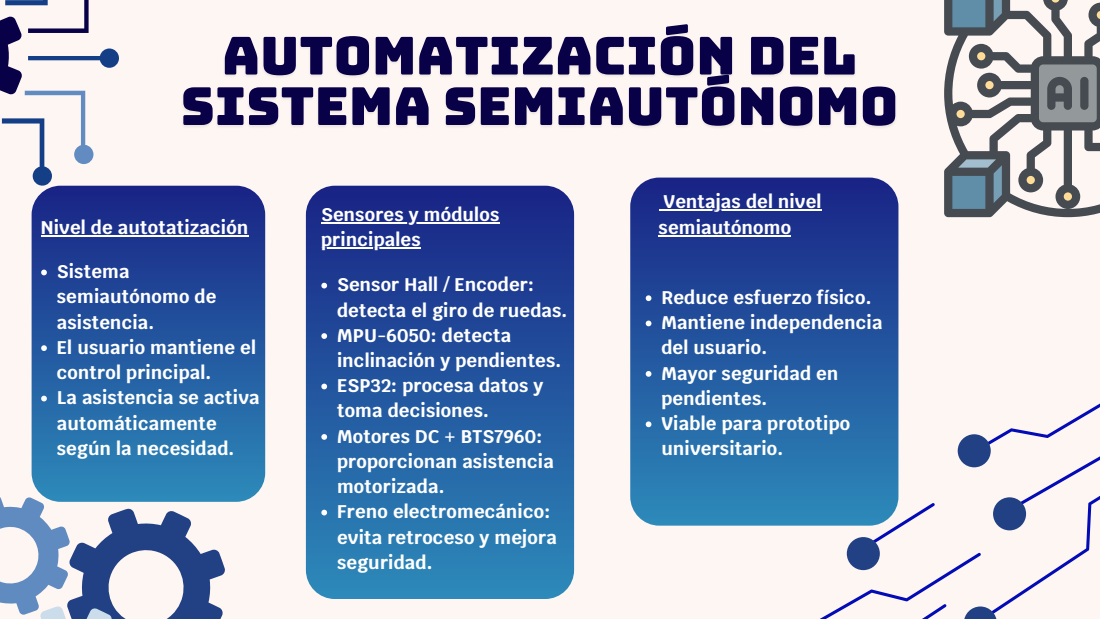
[picture p221: page 14]
Automatización del Sistema Semiautónomo; Sensores y módulos principales

Ventajas del nivel
semiautónomo

Nivel de autotatización
Sistema
semiautónomo de
asistencia.
El usuario mantiene el
control principal.
La asistencia se activa
automáticamente
según la necesidad.

Sensor Hall / Encoder:
detecta el giro de ruedas.
MPU-6050: detecta
inclinación y pendientes.
ESP32: procesa datos y
toma decisiones.
Motores DC + BTS7960:
proporcionan asistencia
motorizada.
Freno electromecánico:
evita retroceso y mejora
seguridad.

Reduce esfuerzo físico.
Mantiene independencia
del usuario.
Mayor seguridad en
pendientes.
Viable para prototipo
universitario.

# Interfaces de red global (IoT y telesalud)

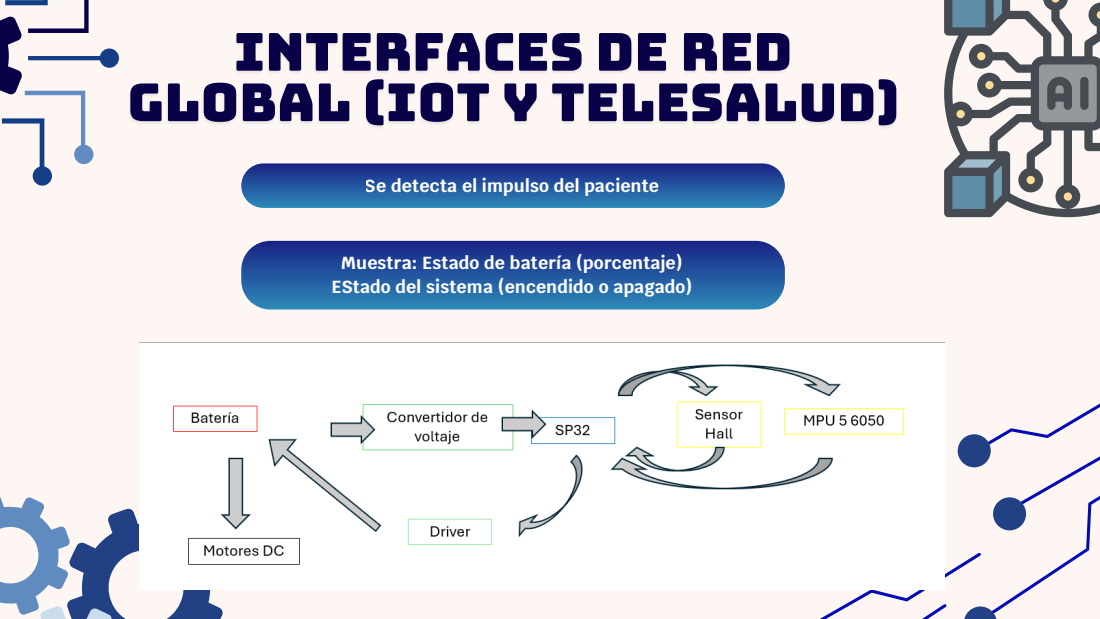
[picture p222: page 15]

Interfaces de red
global (IoT y telesalud)

Se detecta el impulso del paciente

Muestra: Estado de batería (porcentaje)
EStado del sistema (encendido o apagado)

GRACIAS
