Nadya-85/Grupo-3--FUNBIO/Documentación/Entregables/Presentaciones/PPT Entregable N°4.pdf

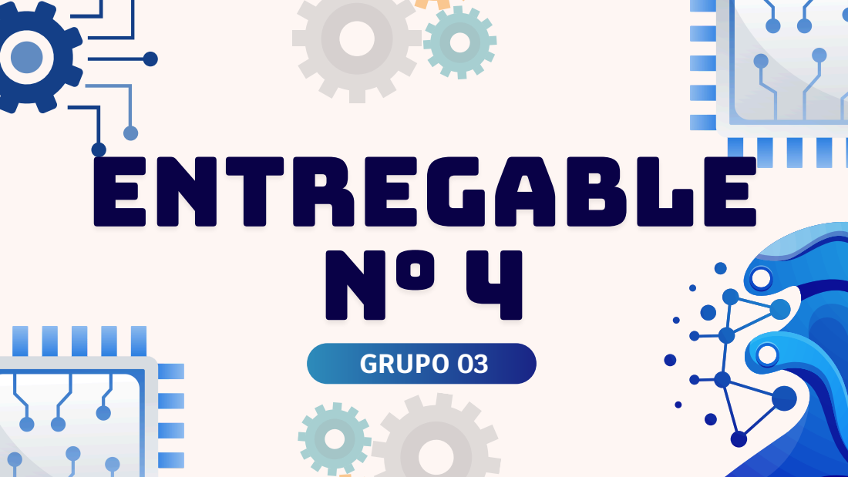
[picture p223: page 1]
GRUPO 03; ENTREGABLE N° 4

# Identificación de la necesidad

# Identificación de la necesidad

Maximización de la autonomía funcional mediante una
locomoción más independiente, segura y controlada en silla de ruedas, tanto en el hogar como en espacios públicos.

NECESIDAD INMEDIATA
Manejo seguro e independiente de la silla de ruedas.
Control de velocidad, equilibrio y postura. Adaptación a rampas, veredas, desniveles y obstáculos.
Reducción de la dependencia hacia cuidadores.

A mediano plazo, optimizar la locomoción en silla de ruedas mediante el entrenamiento progresivo en desplazamientos seguros, eficientes y con menor fatiga, favoreciendo su adaptación al hogar y a la vía pública. Además de fortalecer el uso funcional de miembros superiores para prevenir lesiones por sobreuso en hombros, codos y muñecas.

# TEcnología 1

## Detachable Motor Assist for

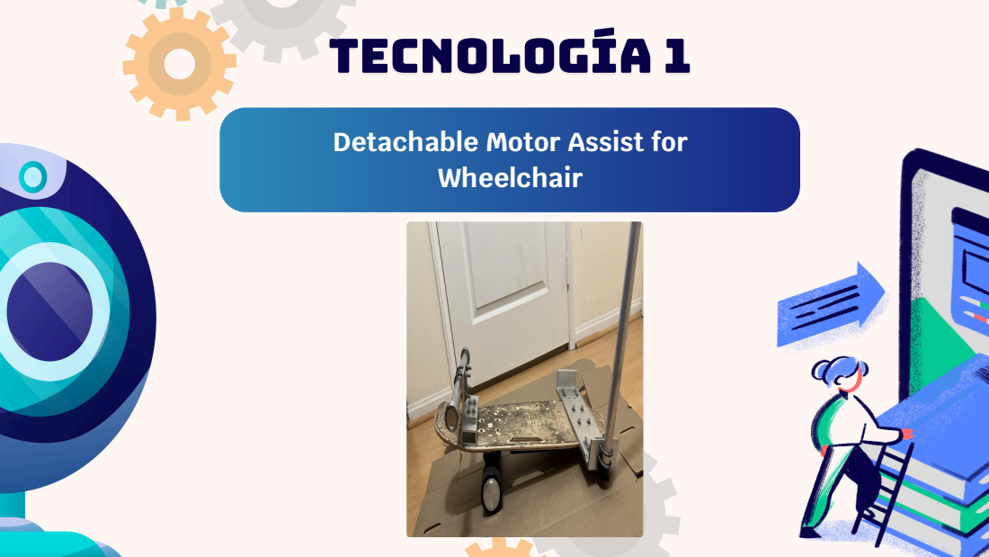
[picture p224: page 3]
Wheelchair

# TEcnología 4

## Portable Ultra Light Power Wheelchair with Carbon Fiber Material

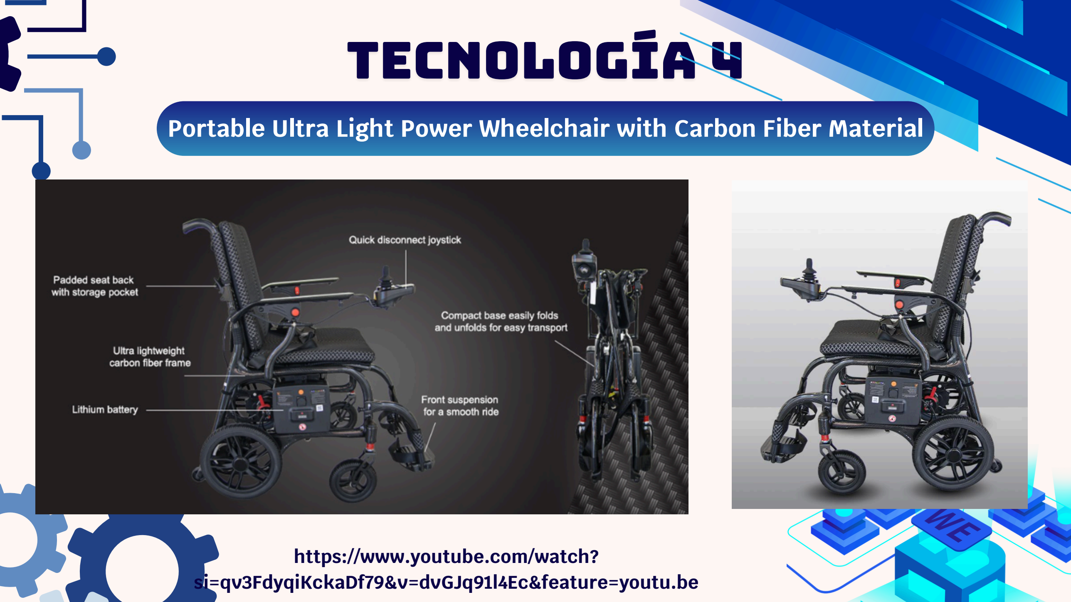
[picture p225: page 4]

https://www.youtube.com/watch?si=qv3FdyqiKckaDf79&v=dvGJq91l4Ec&feature=youtu.be

# TEcnología 6

## e-motion: sistema de asistencia eléctrica para

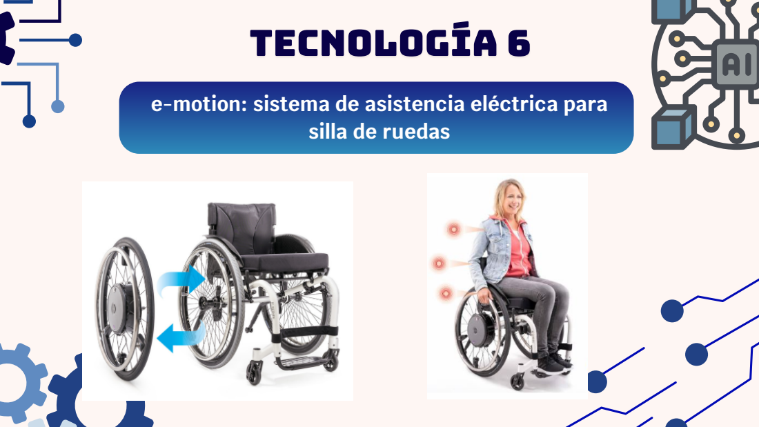
[picture p226: page 5]

silla de ruedas

# TEcnología 7

## Power-Flex Power Base Attachment (Base

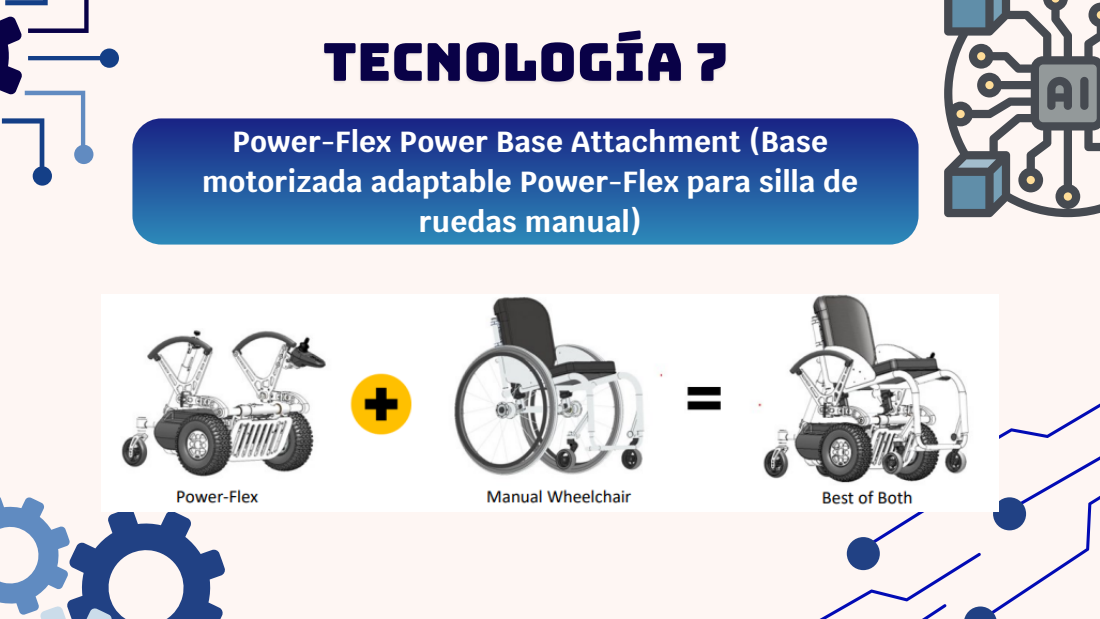
[picture p227: page 6]
ruedas manual)

motorizada adaptable Power-Flex para silla de

## Dispositivo de rueda delantera acoplable (FreeWheel

# TEcnología 9

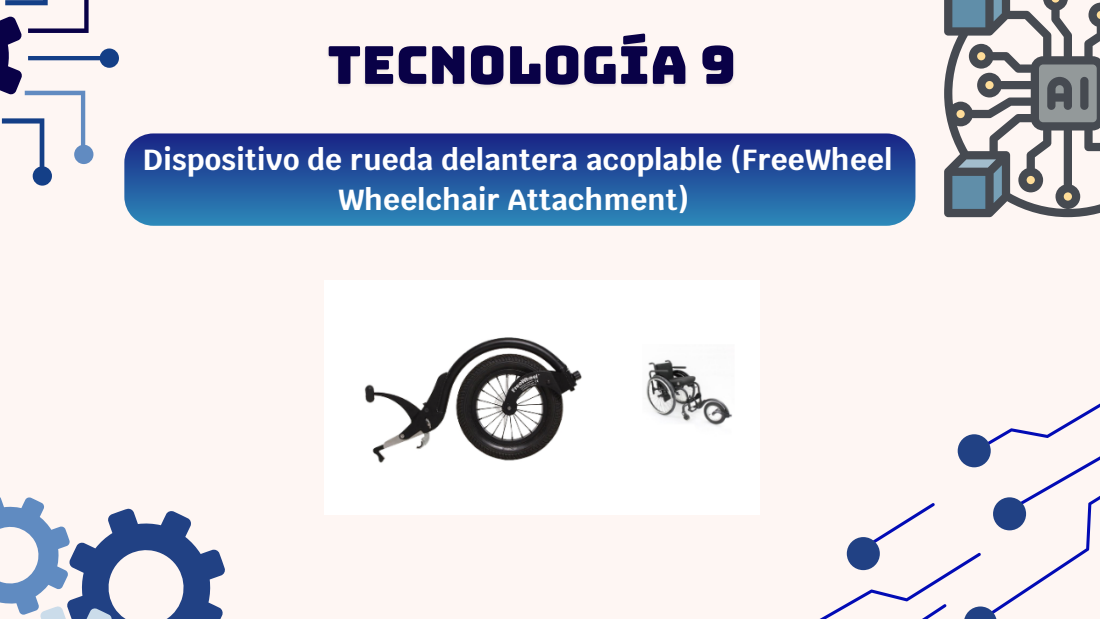
[picture p228: page 7]
Wheelchair Attachment)

GRACIAS
