Nadya-85/Grupo-3--FUNBIO/Documentación/Entregables/Presentaciones/PPT Entregable N°6.pdf

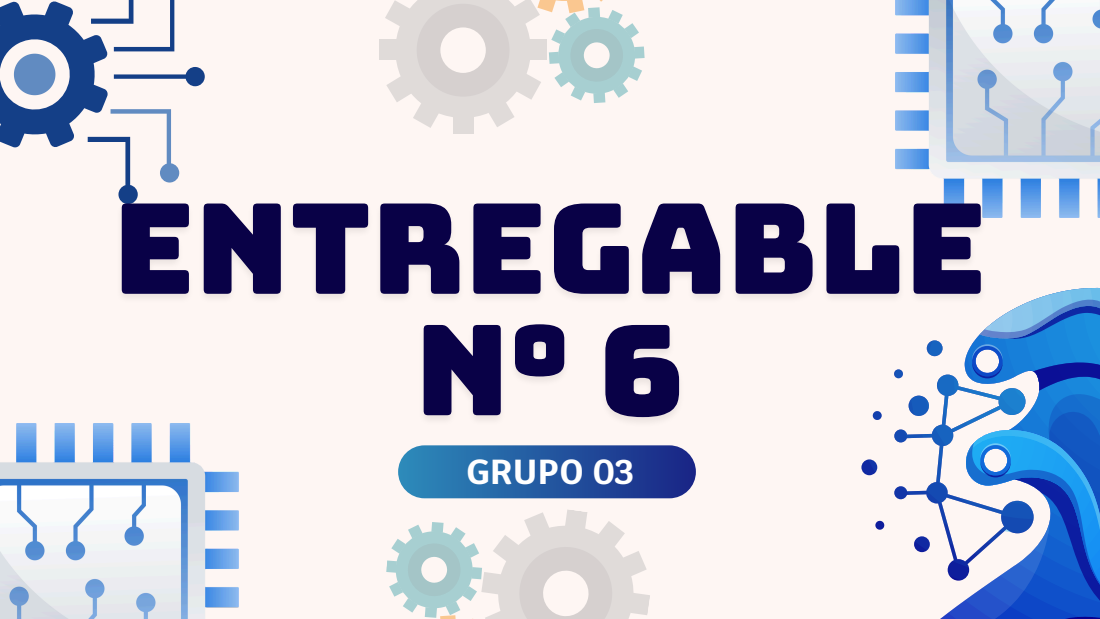
[picture p229: page 1]
GRUPO 03; ENTREGABLE N° 6

# Checkpoint 1 ⁻ Business Case

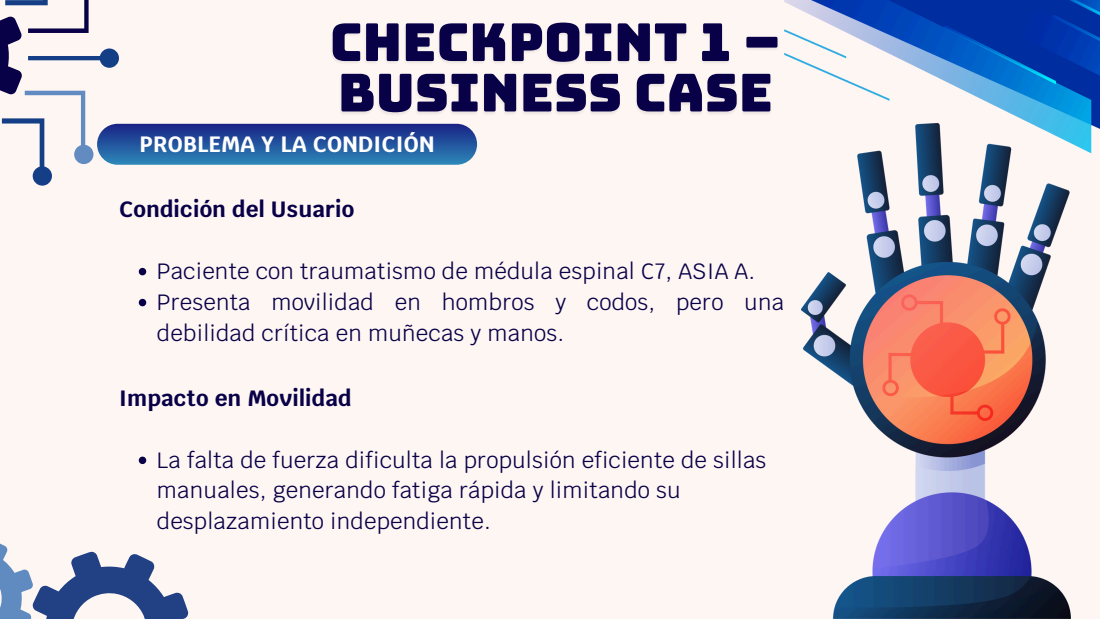
[picture p230: page 2]
Checkpoint 1 ⁻ Business Case

PROBLEMA Y LA CONDICIÓN

Condición del Usuario

Paciente con traumatismo de médula espinal C7, ASIA A.
Presenta movilidad en hombros y codos, pero una
debilidad crítica en muñecas y manos.

Impacto en Movilidad

La falta de fuerza dificulta la propulsión eficiente de sillas
manuales, generando fatiga rápida y limitando su
desplazamiento independiente.

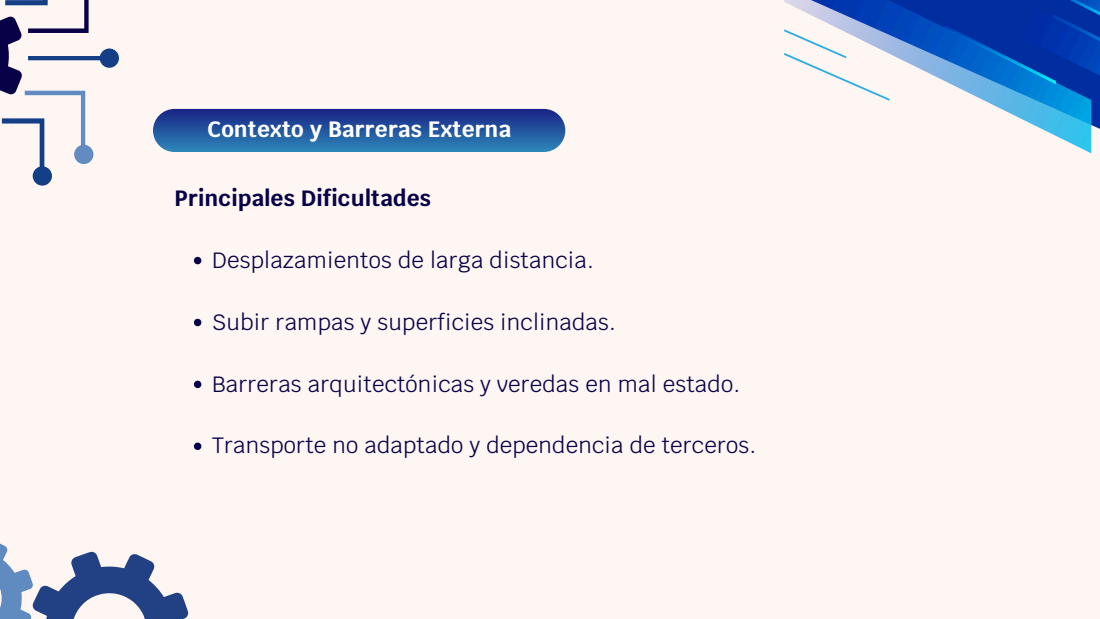
[picture p231: page 3]
Principales Dificultades

Contexto y Barreras Externa

Desplazamientos de larga distancia.

Subir rampas y superficies inclinadas.

Barreras arquitectónicas y veredas en mal estado.

Transporte no adaptado y dependencia de terceros.

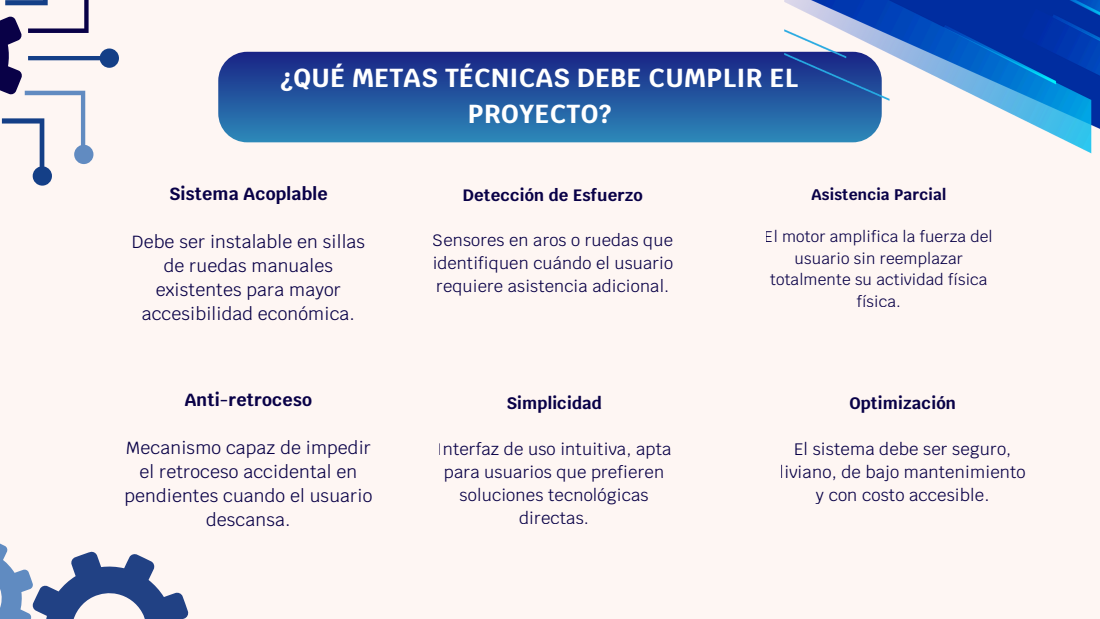
[picture p232: page 4]
Sistema Acoplable; PROYECTO?; Asistencia Parcial; física.; Anti-retroceso; descansa.; Simplicidad; Optimización

¿QUÉ METAS TÉCNICAS DEBE CUMPLIR EL

Detección de Esfuerzo

El motor amplifica la fuerza del
usuario sin reemplazar
totalmente su actividad física

Debe ser instalable en sillas
de ruedas manuales
existentes para mayor
accesibilidad económica.

Sensores en aros o ruedas que
identifiquen cuándo el usuario
requiere asistencia adicional.

Mecanismo capaz de impedir
el retroceso accidental en
pendientes cuando el usuario

Interfaz de uso intuitiva, apta
para usuarios que prefieren
soluciones tecnológicas
directas.

El sistema debe ser seguro,
liviano, de bajo mantenimiento
y con costo accesible.

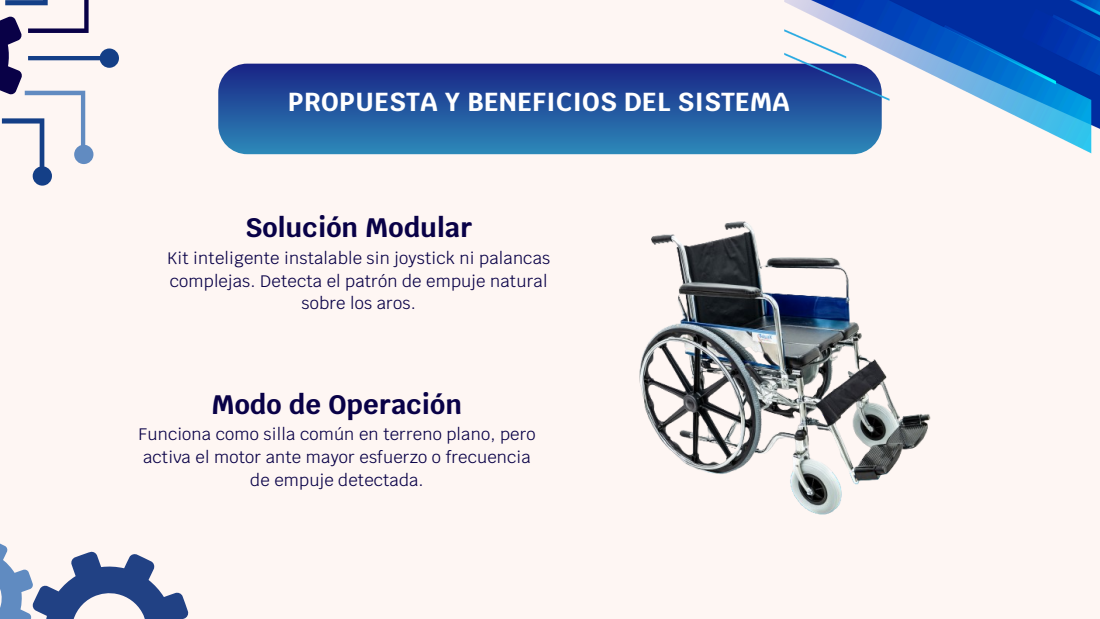
[picture p233: page 5]
Solución Modular

PROPUESTA Y BENEFICIOS DEL SISTEMA

Kit inteligente instalable sin joystick ni palancas
complejas. Detecta el patrón de empuje natural

sobre los aros.

Modo de Operación

Funciona como silla común en terreno plano, pero
activa el motor ante mayor esfuerzo o frecuencia

de empuje detectada.

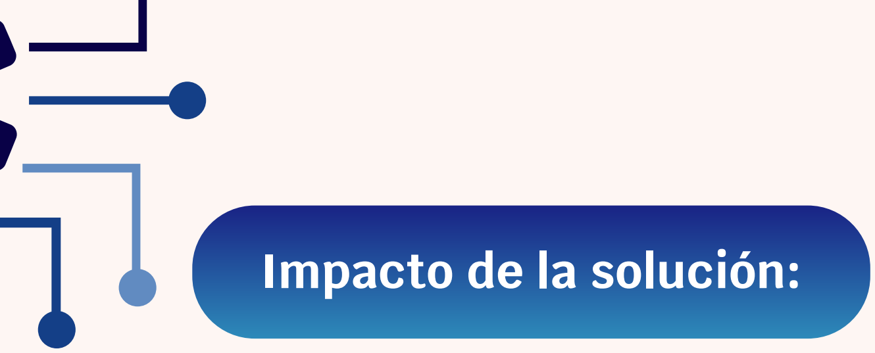
[picture p234: figure]
Impacto de la solución:
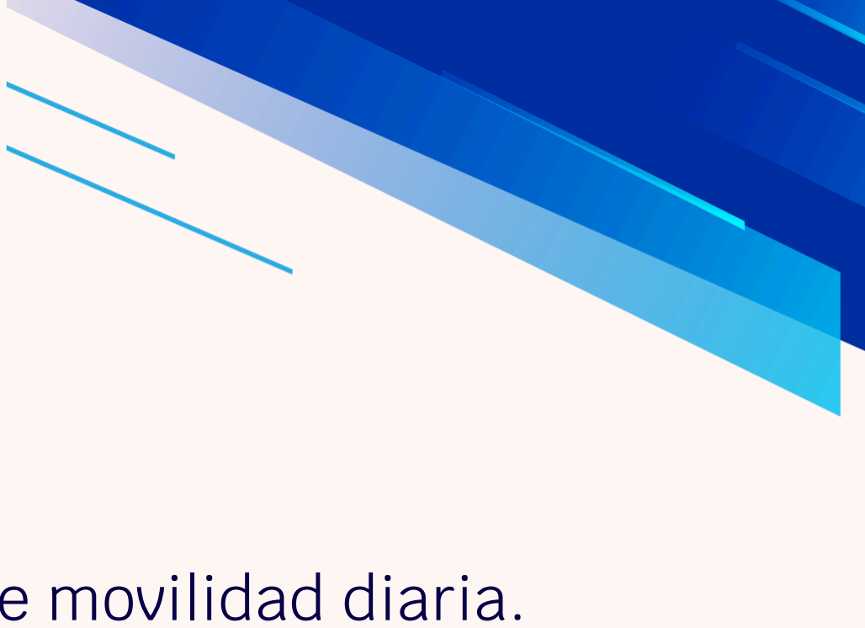
[picture p235: figure]

Usuario: Independencia real, menor fatiga física y mayor radio de movilidad diaria.

Familia: Alivio de la carga de cuidado y menor necesidad de asistencia en exteriores.

Sociedad: Inclusión social efectiva y reducción de barreras arquitectónicas percibidas.

Empresa: Modelo de negocio escalable basado en módulos asequibles de alta demanda.

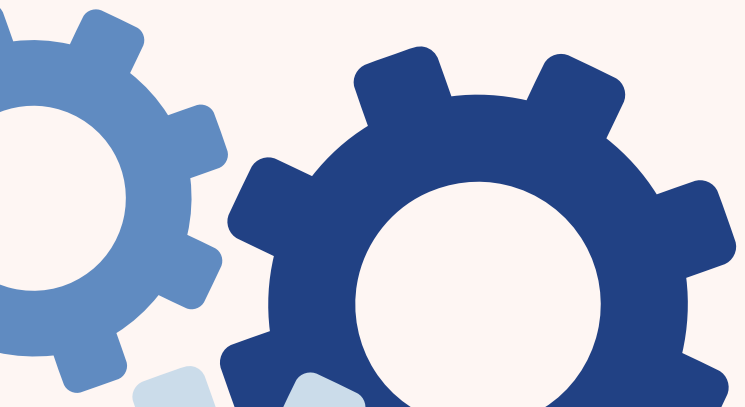
[picture p236: figure]

### USUARIOS, CLIENTES Y PARTES INTERESADAS CLAVE

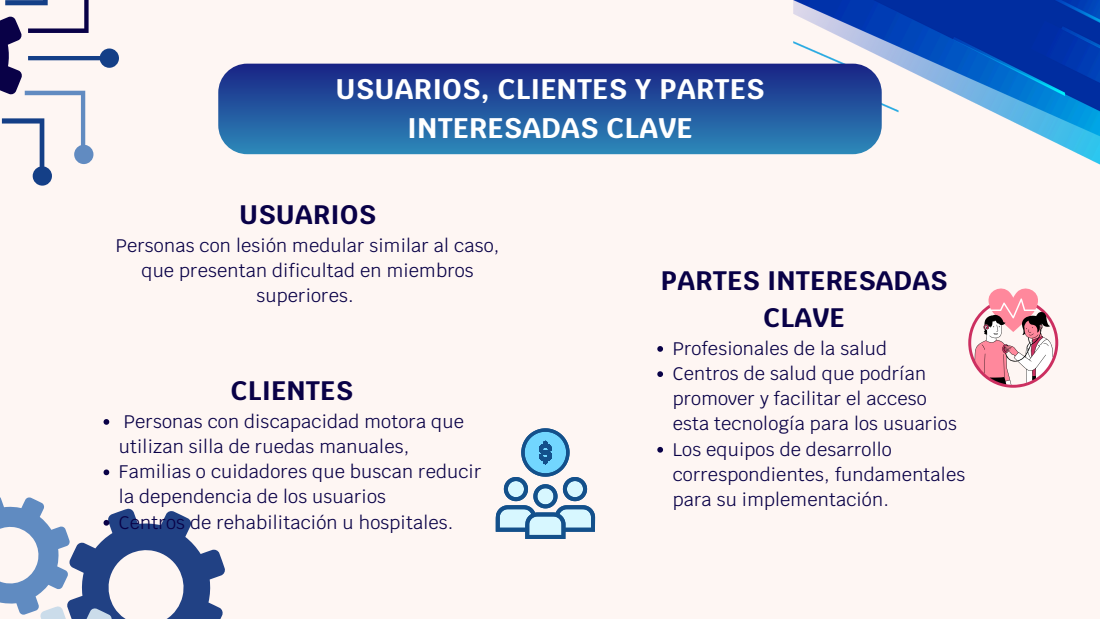
[picture p237: page 7]
USUARIOS; superiores.; PARTES INTERESADAS CLAVE; CLIENTES

Personas con lesión medular similar al caso,
que presentan dificultad en miembros

Profesionales de la salud
Centros de salud que podrían
promover y facilitar el acceso
esta tecnología para los usuarios
Los equipos de desarrollo
correspondientes, fundamentales
para su implementación.

Personas con discapacidad motora que
utilizan silla de ruedas manuales,
Familias o cuidadores que buscan reducir
la dependencia de los usuarios
Centros de rehabilitación u hospitales.

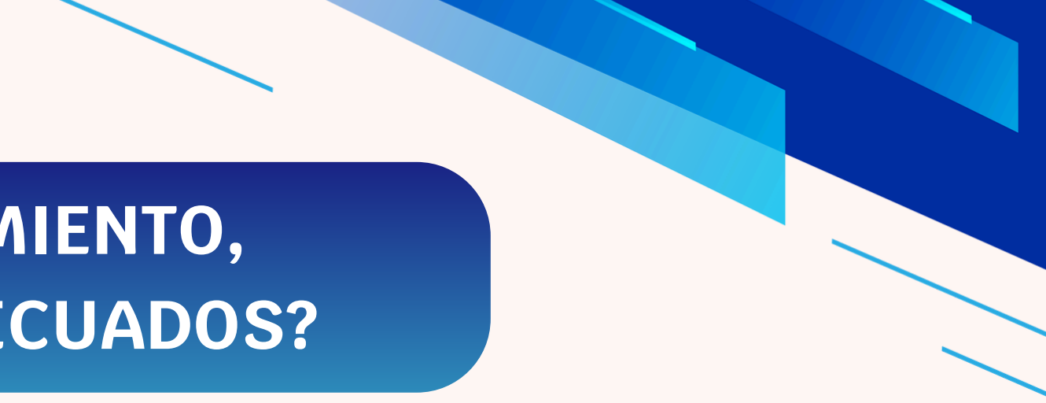
[picture p238: figure]

¿SE CUENTA CON EL CONOCIMIENTO,

### HABILIDADES Y RECURSOS ADECUADOS?

### CONOCIMIENTO Y HABILIDADES

Información clínica y funcional del usuario, lo que permite comprender su entorno (limitaciones, necesidades).

Se requiere conocimientos de diseño de sistemas electrónicos (uso de sensores, control de motores)

Diseño mecánico para que se acople a la silla

Conocimientos en rehabilitación y ergonomía (para que el sistema sea funcional y seguro)

### RECURSOS

Componentes electrónicos,

herramientas de prototipado o materiales para la estructura.

Analizando estos puntos,
consideramos que de forma
preliminar se cuenta con una base para iniciar el proyecto.

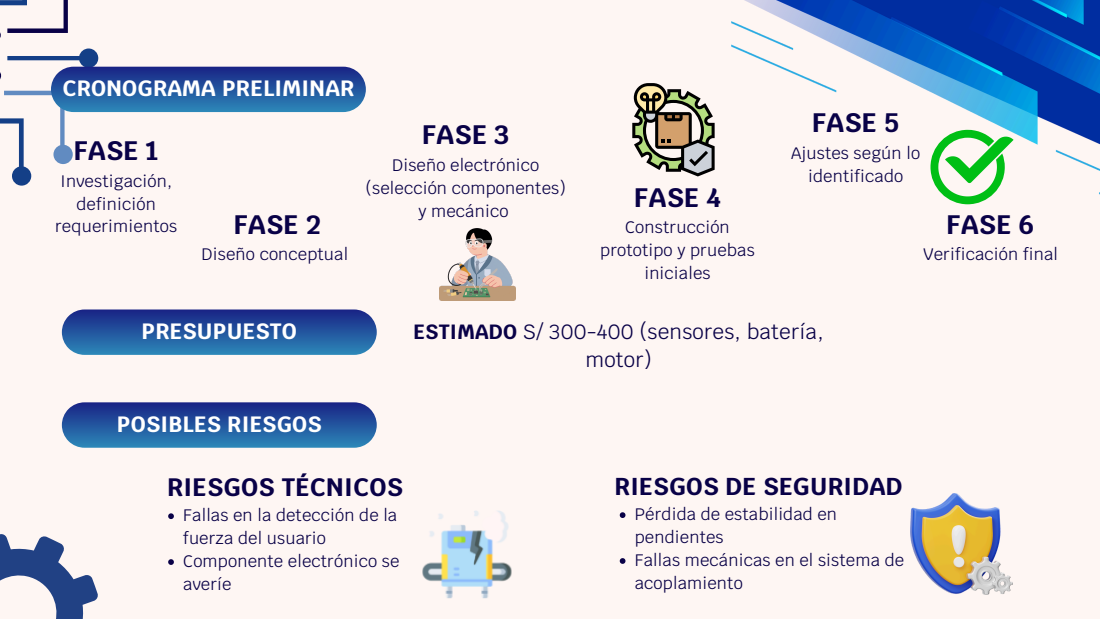
[picture p239: page 9]
CRONOGRAMA PRELIMINAR; PRESUPUESTO; FASE 1; Investigación, definición; requerimientos; FASE 2; Diseño conceptual; FASE 3; Diseño electrónico (selección componentes) y mecánico; FASE 4; Construcción prototipo y pruebas iniciales; FASE 6; Verificación final; motor)

FASE 5
Ajustes según lo
identificado

ESTIMADO S/ 300-400 (sensores, batería,

POSIBLES RIESGOS
RIESGOS TÉCNICOS
Fallas en la detección de la
fuerza del usuario
Componente electrónico se
averíe

RIESGOS DE SEGURIDAD
Pérdida de estabilidad en
pendientes
Fallas mecánicas en el sistema de
acoplamiento

# Descripción del proceso técnico

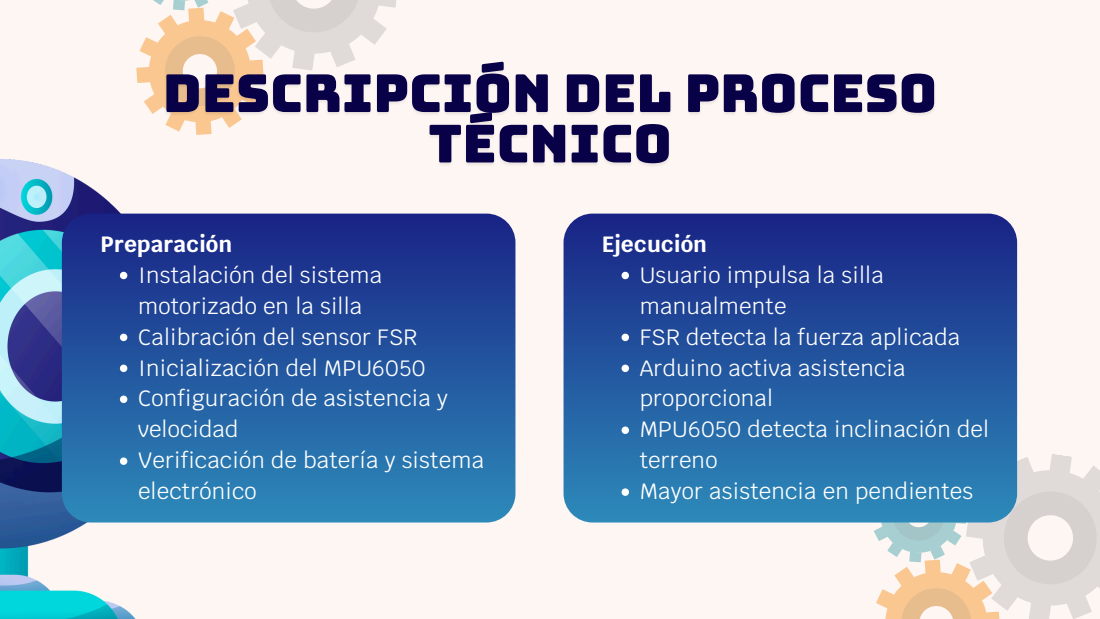
[picture p240: page 10]
técnico

Descripción del proceso

Preparación
Instalación del sistema
motorizado en la silla
Calibración del sensor FSR
Inicialización del MPU6050
Configuración de asistencia y
velocidad
Verificación de batería y sistema
electrónico

Ejecución
Usuario impulsa la silla
manualmente
FSR detecta la fuerza aplicada
Arduino activa asistencia
proporcional
MPU6050 detecta inclinación del
terreno
Mayor asistencia en pendientes

# Descripción del proceso técnico

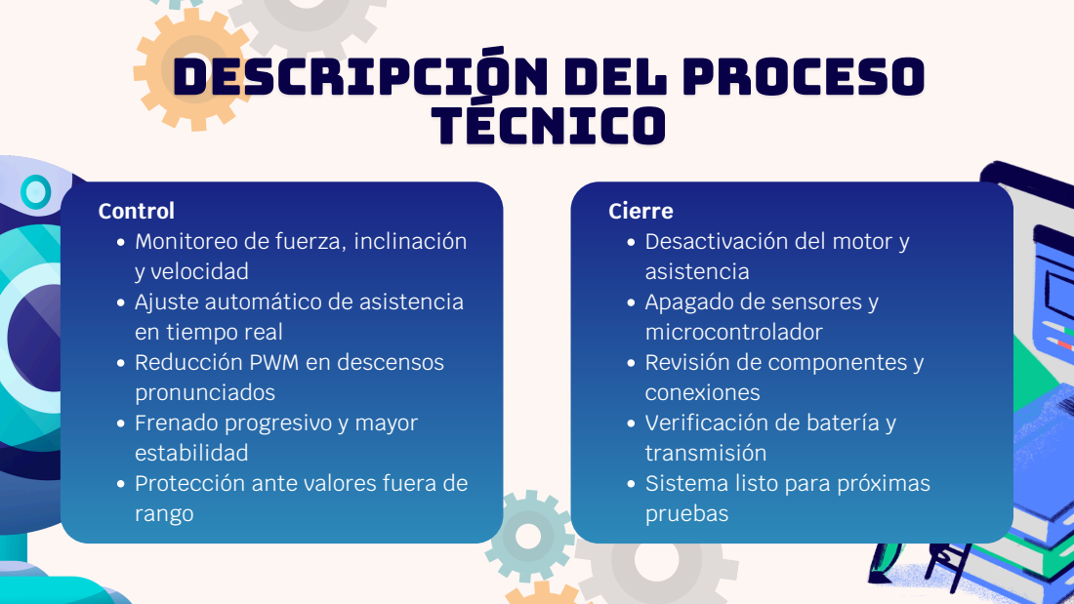
[picture p241: page 11]
técnico

Descripción del proceso

Control
Monitoreo de fuerza, inclinación
y velocidad
Ajuste automático de asistencia
en tiempo real
Reducción PWM en descensos
pronunciados
Frenado progresivo y mayor
estabilidad
Protección ante valores fuera de
rango

Cierre
Desactivación del motor y
asistencia
Apagado de sensores y
microcontrolador
Revisión de componentes y
conexiones
Verificación de batería y
transmisión
Sistema listo para próximas
pruebas

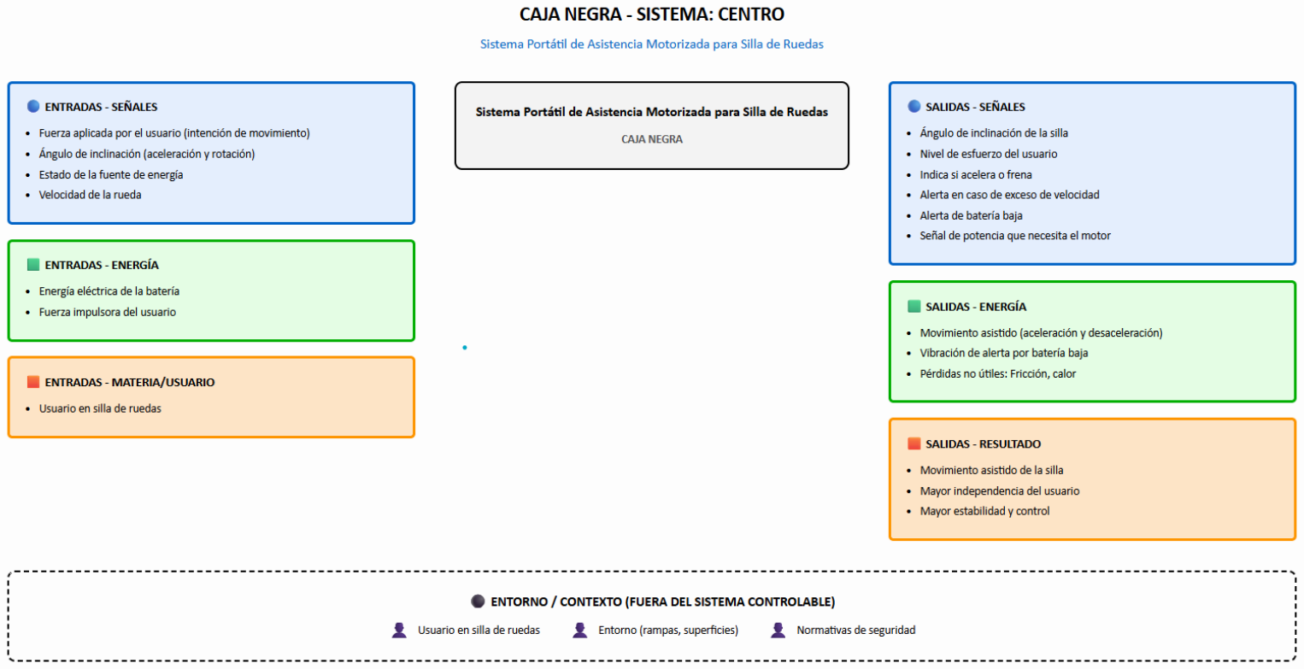
[picture p242: page 12]

# características del prototipo

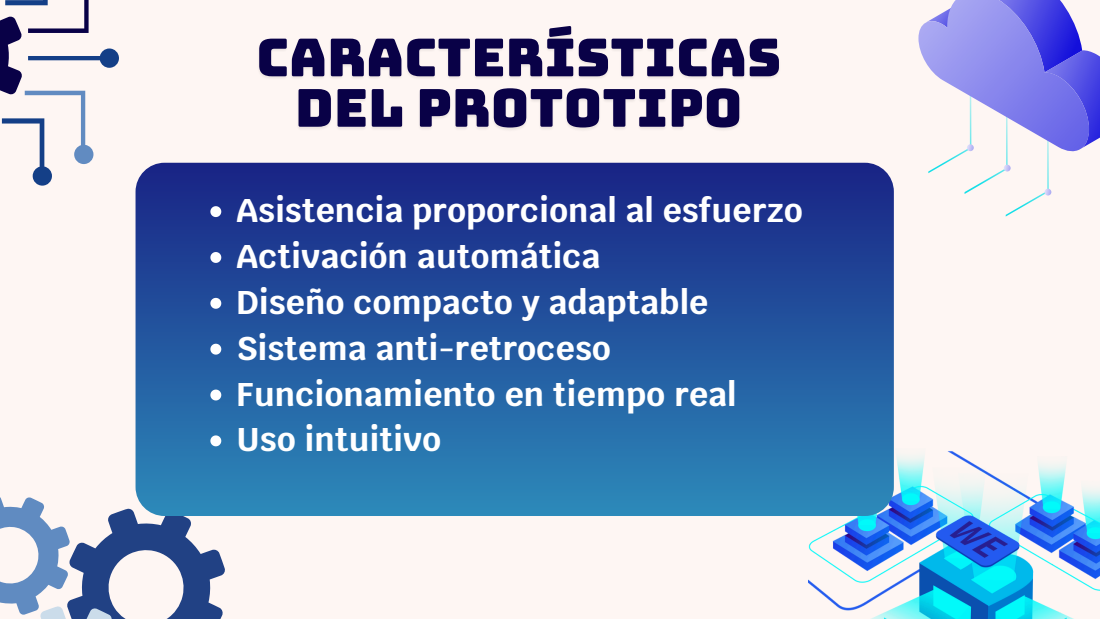
[picture p243: page 13]
características del prototipo

Asistencia proporcional al esfuerzo
Activación automática
Diseño compacto y adaptable
Sistema anti-retroceso
Funcionamiento en tiempo real
Uso intuitivo

# REQUISITOS FUNCIONALES y no funcionales

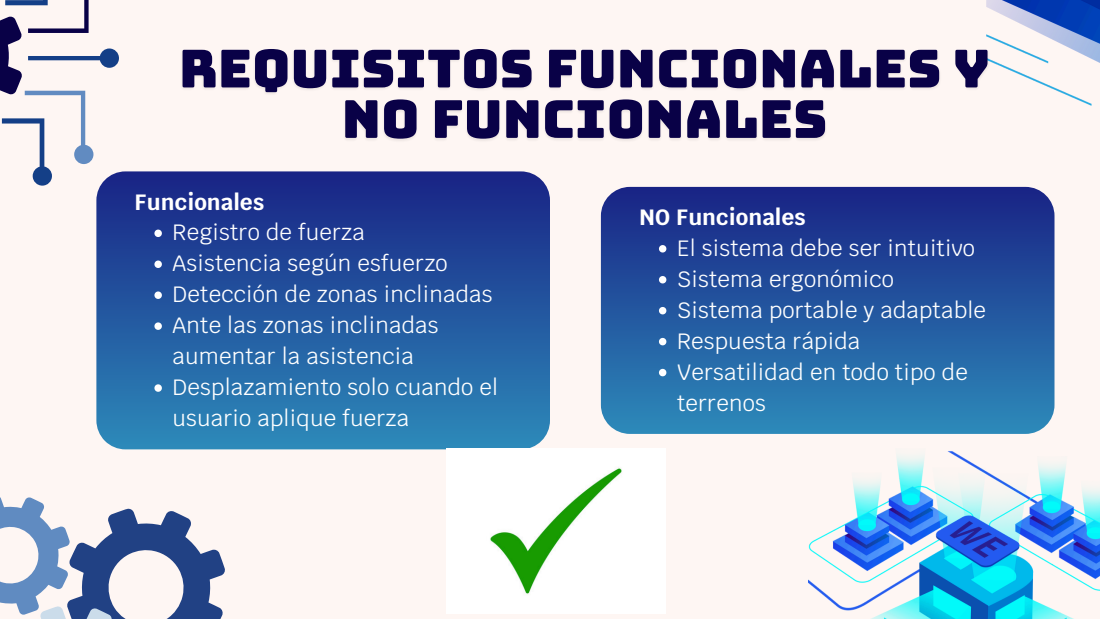
[picture p244: page 14]
REQUISITOS FUNCIONALES y no funcionales

Funcionales
Registro de fuerza
Asistencia según esfuerzo
Detección de zonas inclinadas
Ante las zonas inclinadas
aumentar la asistencia
Desplazamiento solo cuando el
usuario aplique fuerza

NO Funcionales
El sistema debe ser intuitivo
Sistema ergonómico
Sistema portable y adaptable
Respuesta rápida
Versatilidad en todo tipo de
terrenos

# Clasificacion de requisitos

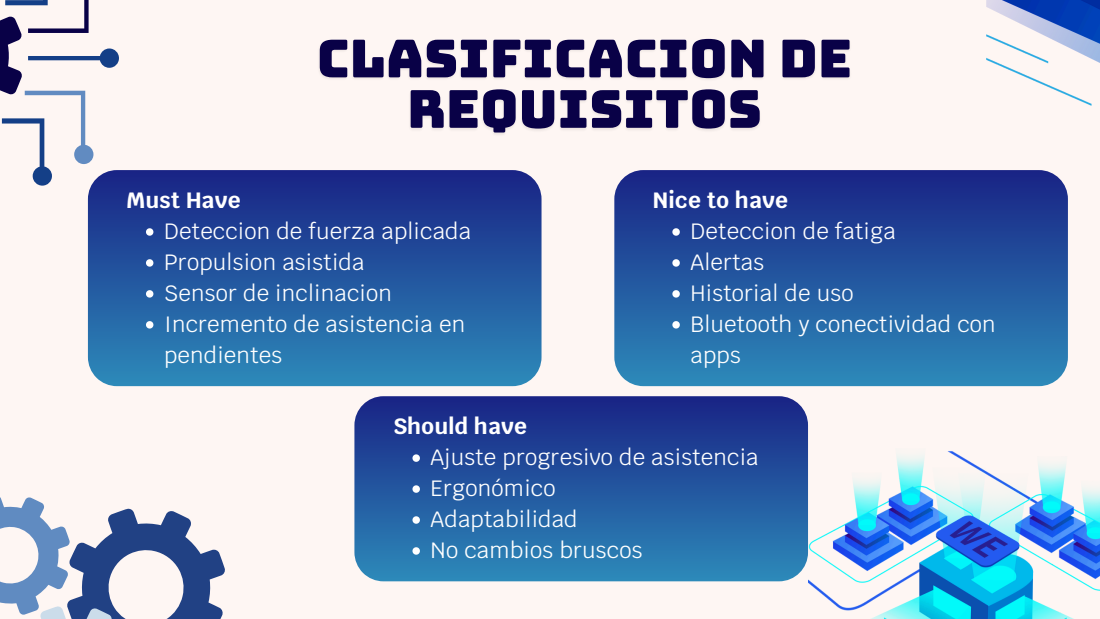
[picture p245: page 15]
Clasificacion de requisitos

Must Have
Deteccion de fuerza aplicada
Propulsion asistida
Sensor de inclinacion
Incremento de asistencia en
pendientes

Nice to have
Deteccion de fatiga
Alertas
Historial de uso
Bluetooth y conectividad con
apps

Should have
Ajuste progresivo de asistencia
Ergonómico
Adaptabilidad
No cambios bruscos

GRACIAS
