Nadya-85/Grupo-3--FUNBIO/Documentación/Entregables/Presentaciones/PPT Entregable N°5.pdf

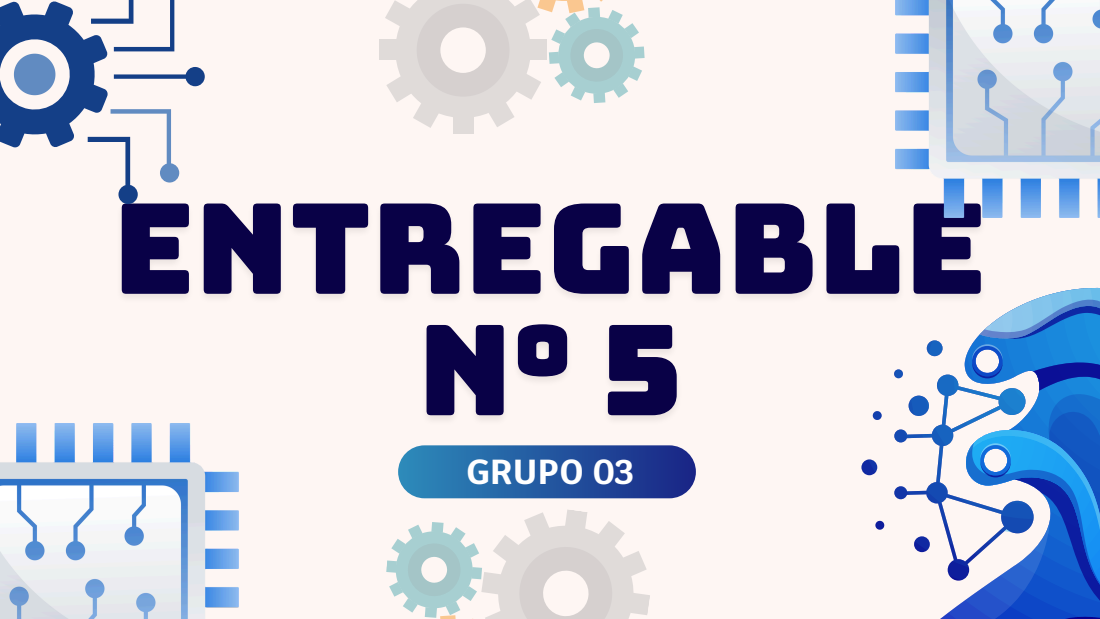
[picture p246: page 1]
ENTREGABLE N° 5; GRUPO 03

# PROBLEMáTICA

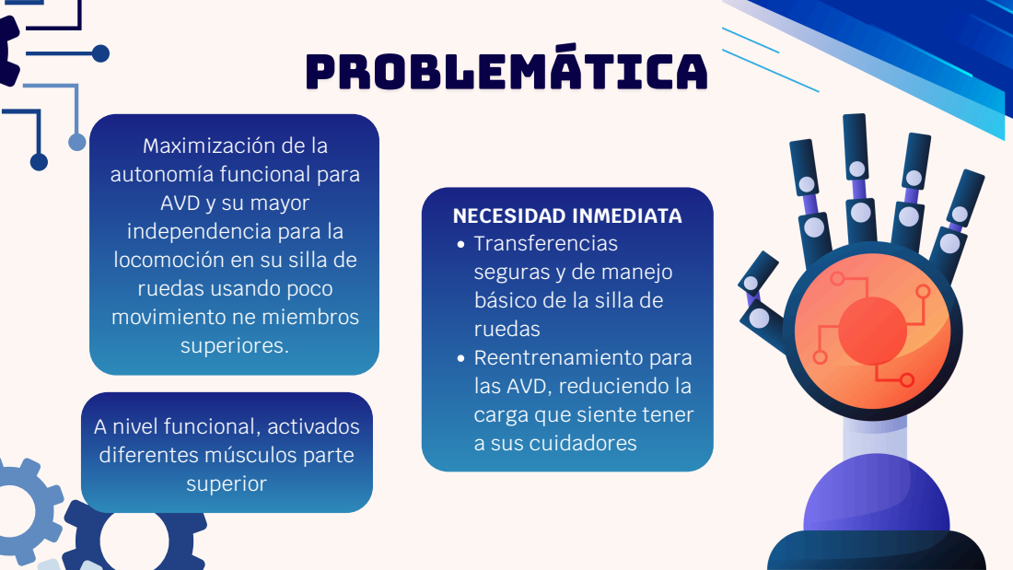
[picture p247: page 2]
superior

Maximización de la
autonomía funcional para
AVD y su mayor
independencia para la
locomoción en su silla de
ruedas usando poco
movimiento ne miembros
superiores.

NECESIDAD INMEDIATA
Transferencias
seguras y de manejo
básico de la silla de
ruedas
Reentrenamiento para
las AVD, reduciendo la
carga que siente tener
a sus cuidadores

A nivel funcional, activados
diferentes músculos parte

# PATENTE 1

## Sistema de asistencia de movimiento

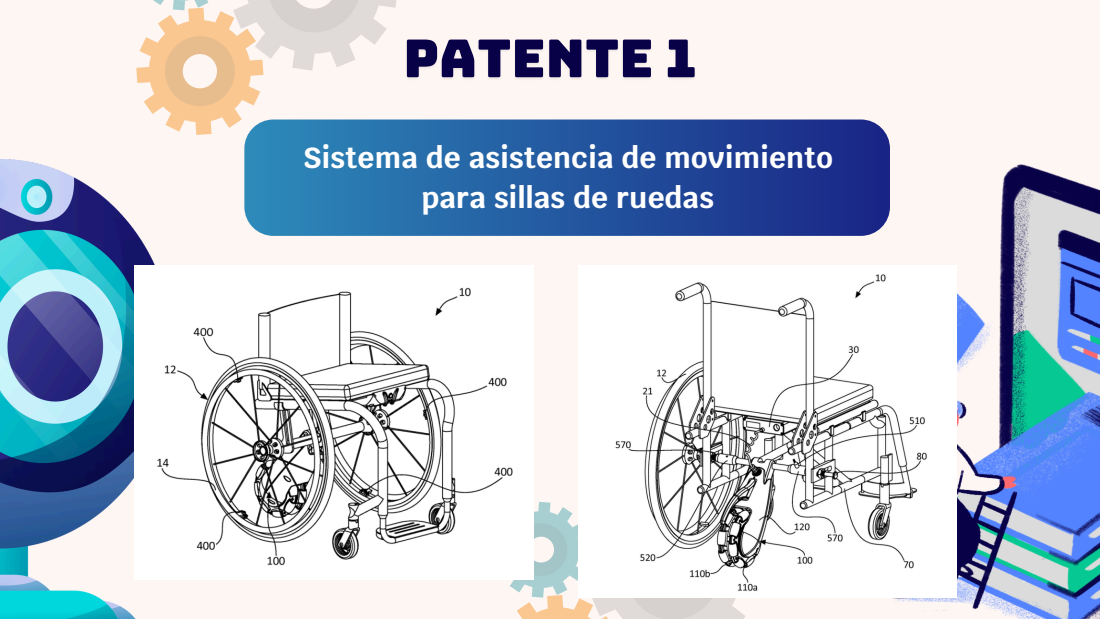
[picture p248: page 3]

para sillas de ruedas

# PATENTE 2

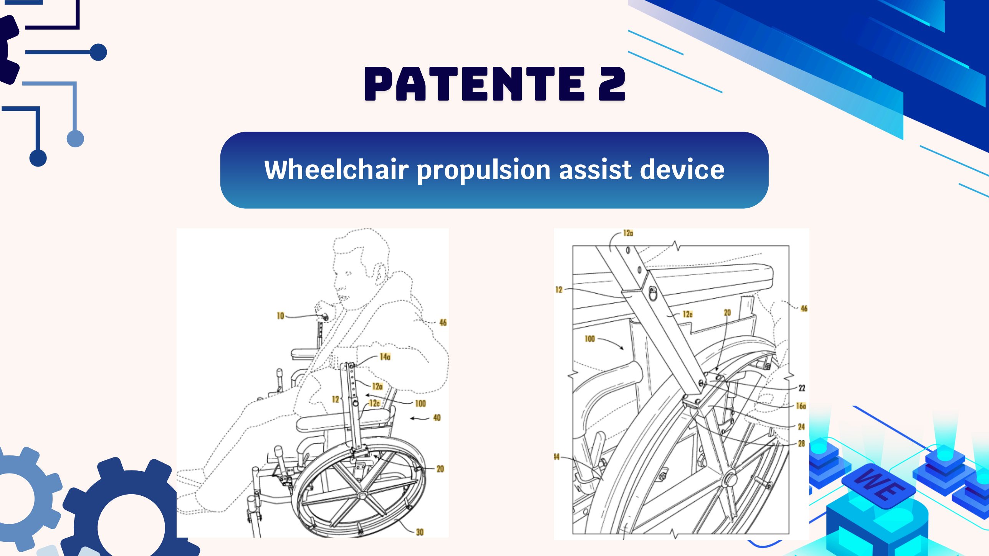
[picture p249: page 4]

## Wheelchair propulsion assist device

# PATENTE 3

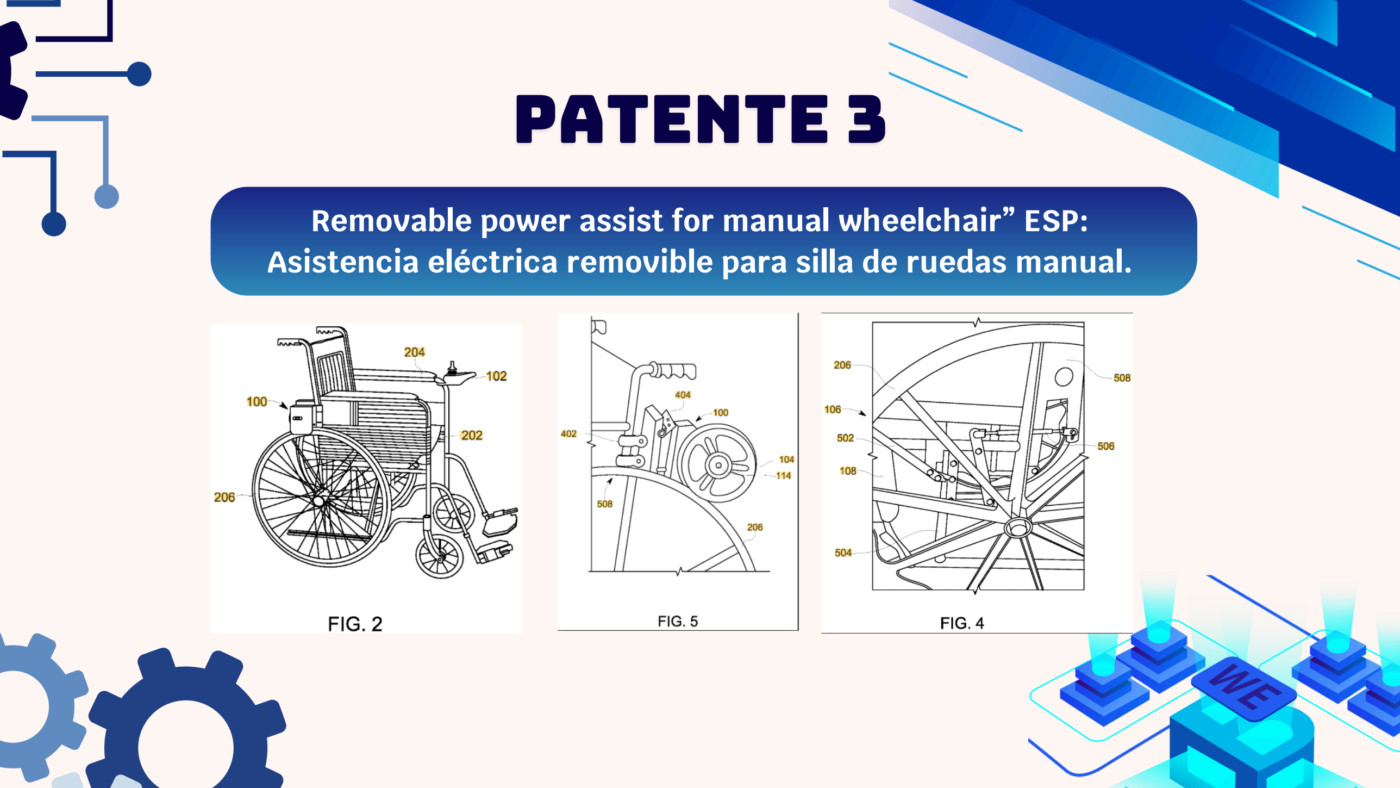
[picture p250: page 5]

Removable power assist for manual wheelchair” ESP: Asistencia eléctrica removible para silla de ruedas manual.

# PATENTE 4

## Silla de ruedas propulsada por movimiento de remo que

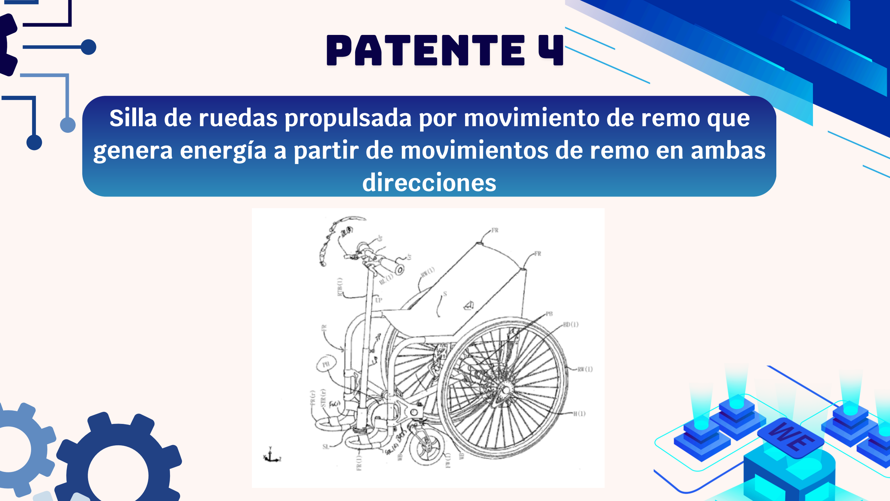
[picture p251: page 6]

## genera energía a partir de movimientos de remo en ambas direcciones

# PATENTE 5

## Electric wheelchair

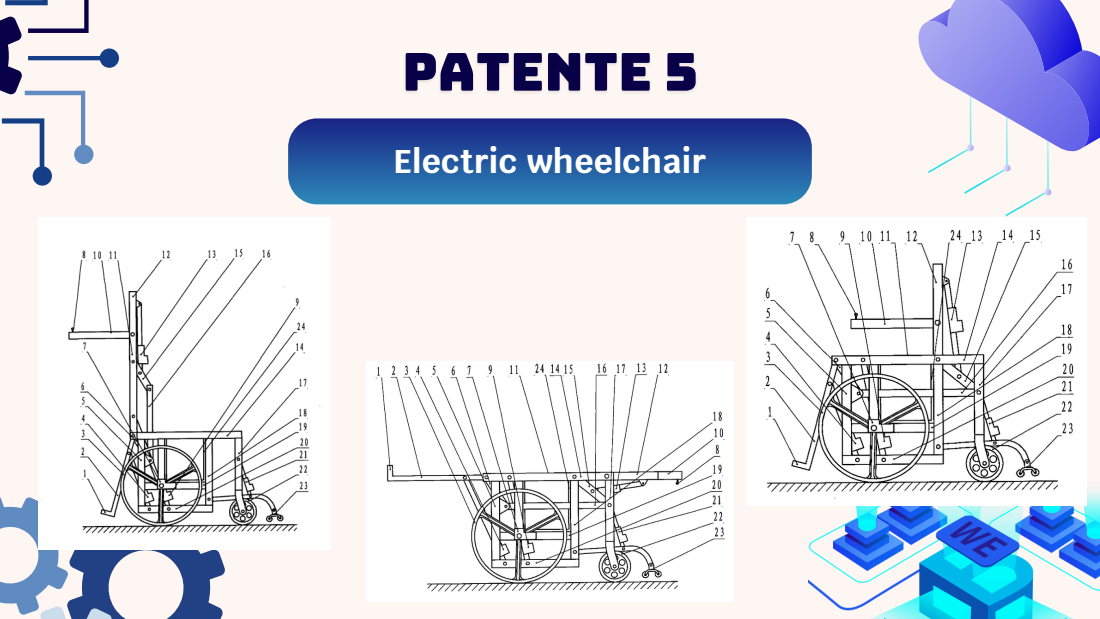
[picture p252: page 7]

# PATENTE 6

## Wheelchair mobility system and method (Sistema

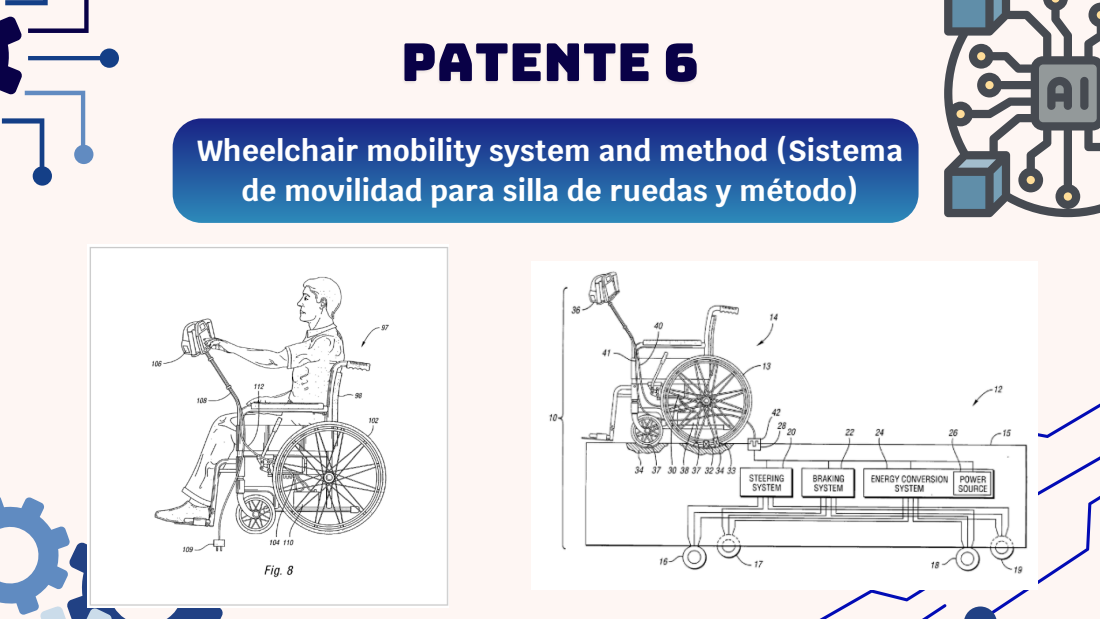
[picture p253: page 8]

de movilidad para silla de ruedas y método)

# REFLEXIÓN FINAL

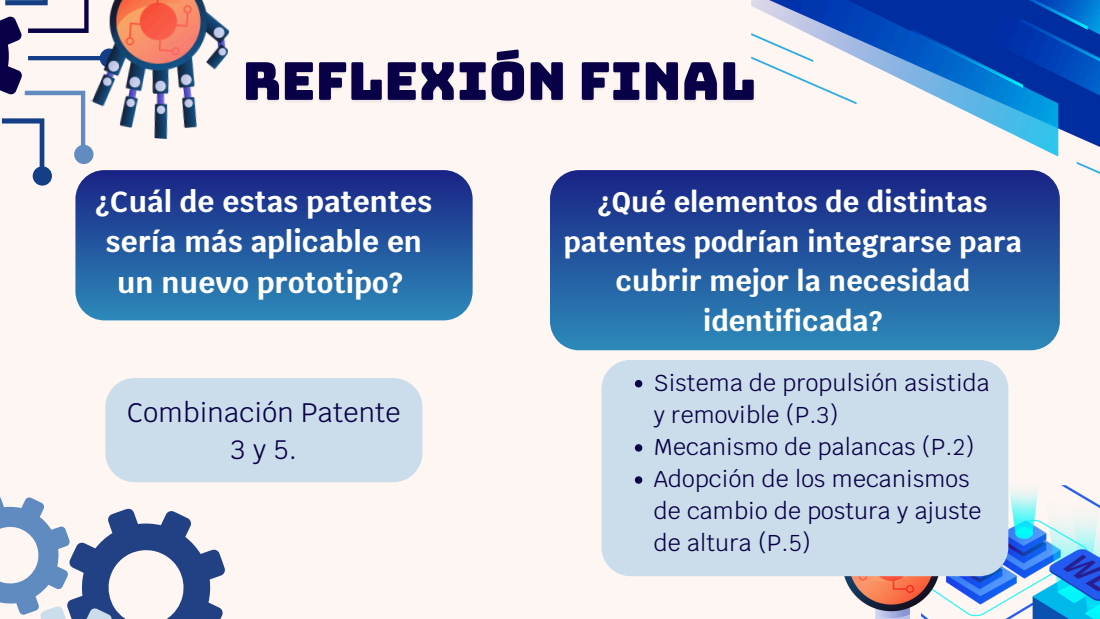
[picture p254: page 9]
Combinación Patente 3 y 5.

¿Cuál de estas patentes
sería más aplicable en
un nuevo prototipo?

¿Qué elementos de distintas
patentes podrían integrarse para
cubrir mejor la necesidad
identificada?

Sistema de propulsión asistida
y removible (P.3)
Mecanismo de palancas (P.2)
Adopción de los mecanismos
de cambio de postura y ajuste
de altura (P.5)

GRACIAS
